gralco/l5-schematic/CAD/PADS/librem5_mainboard/librem5_mainboard_kicad_conversion/librem5_mainboard_sheet3.kicad_sch

## KiCad design CAD/PADS/librem5_mainboard/librem5_mainboard_kicad_conversion/librem5_mainboard_sheet3.kicad_sch (2026-05-21)

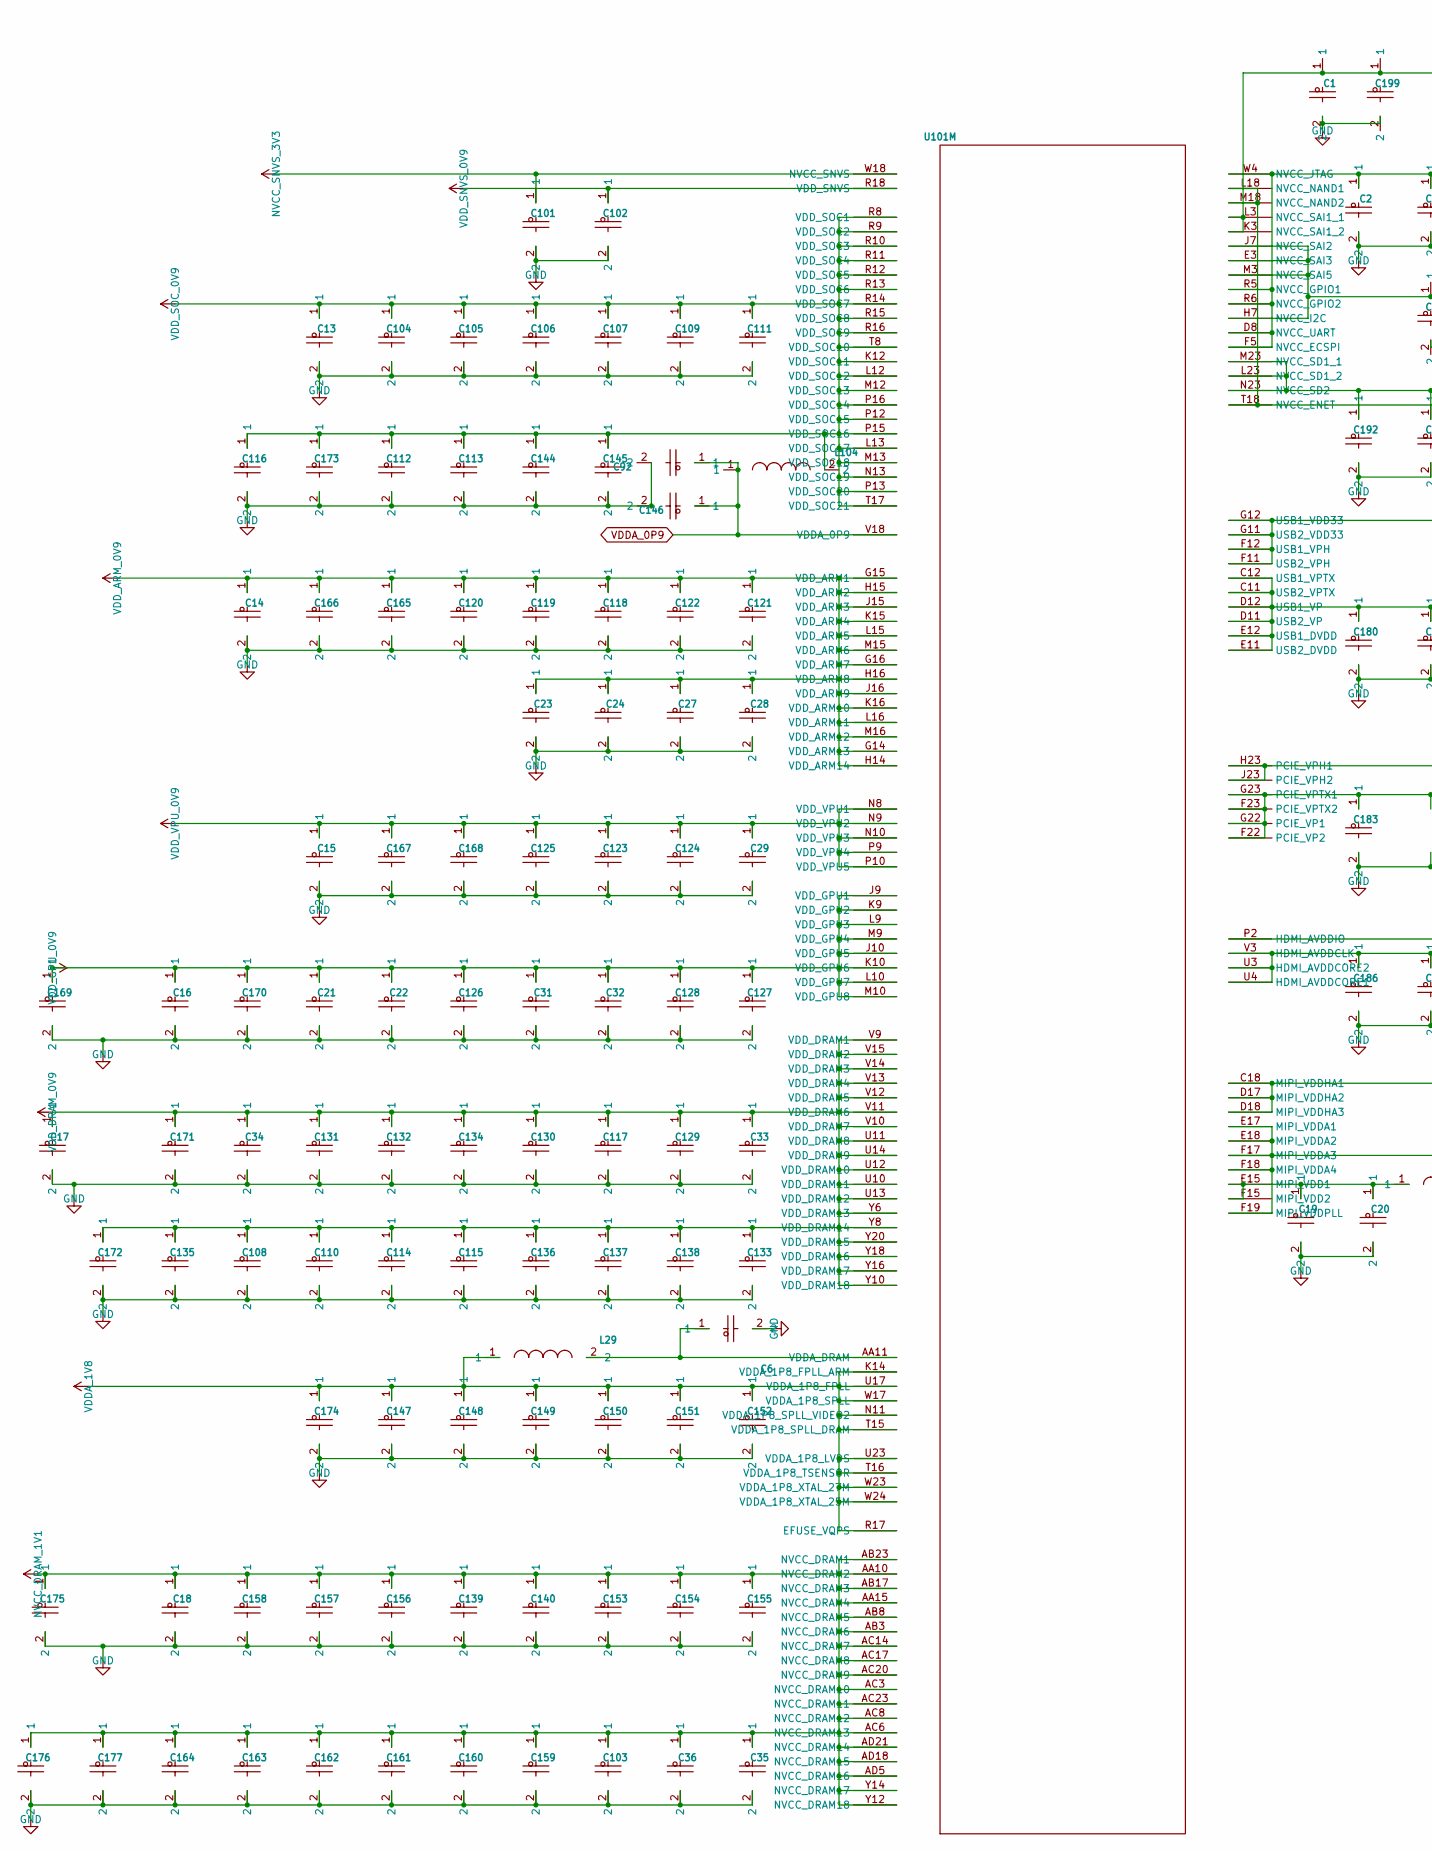
[picture p36: schematic librem5_mainboard_sheet3.kicad_sch, part in row 1, column 1]

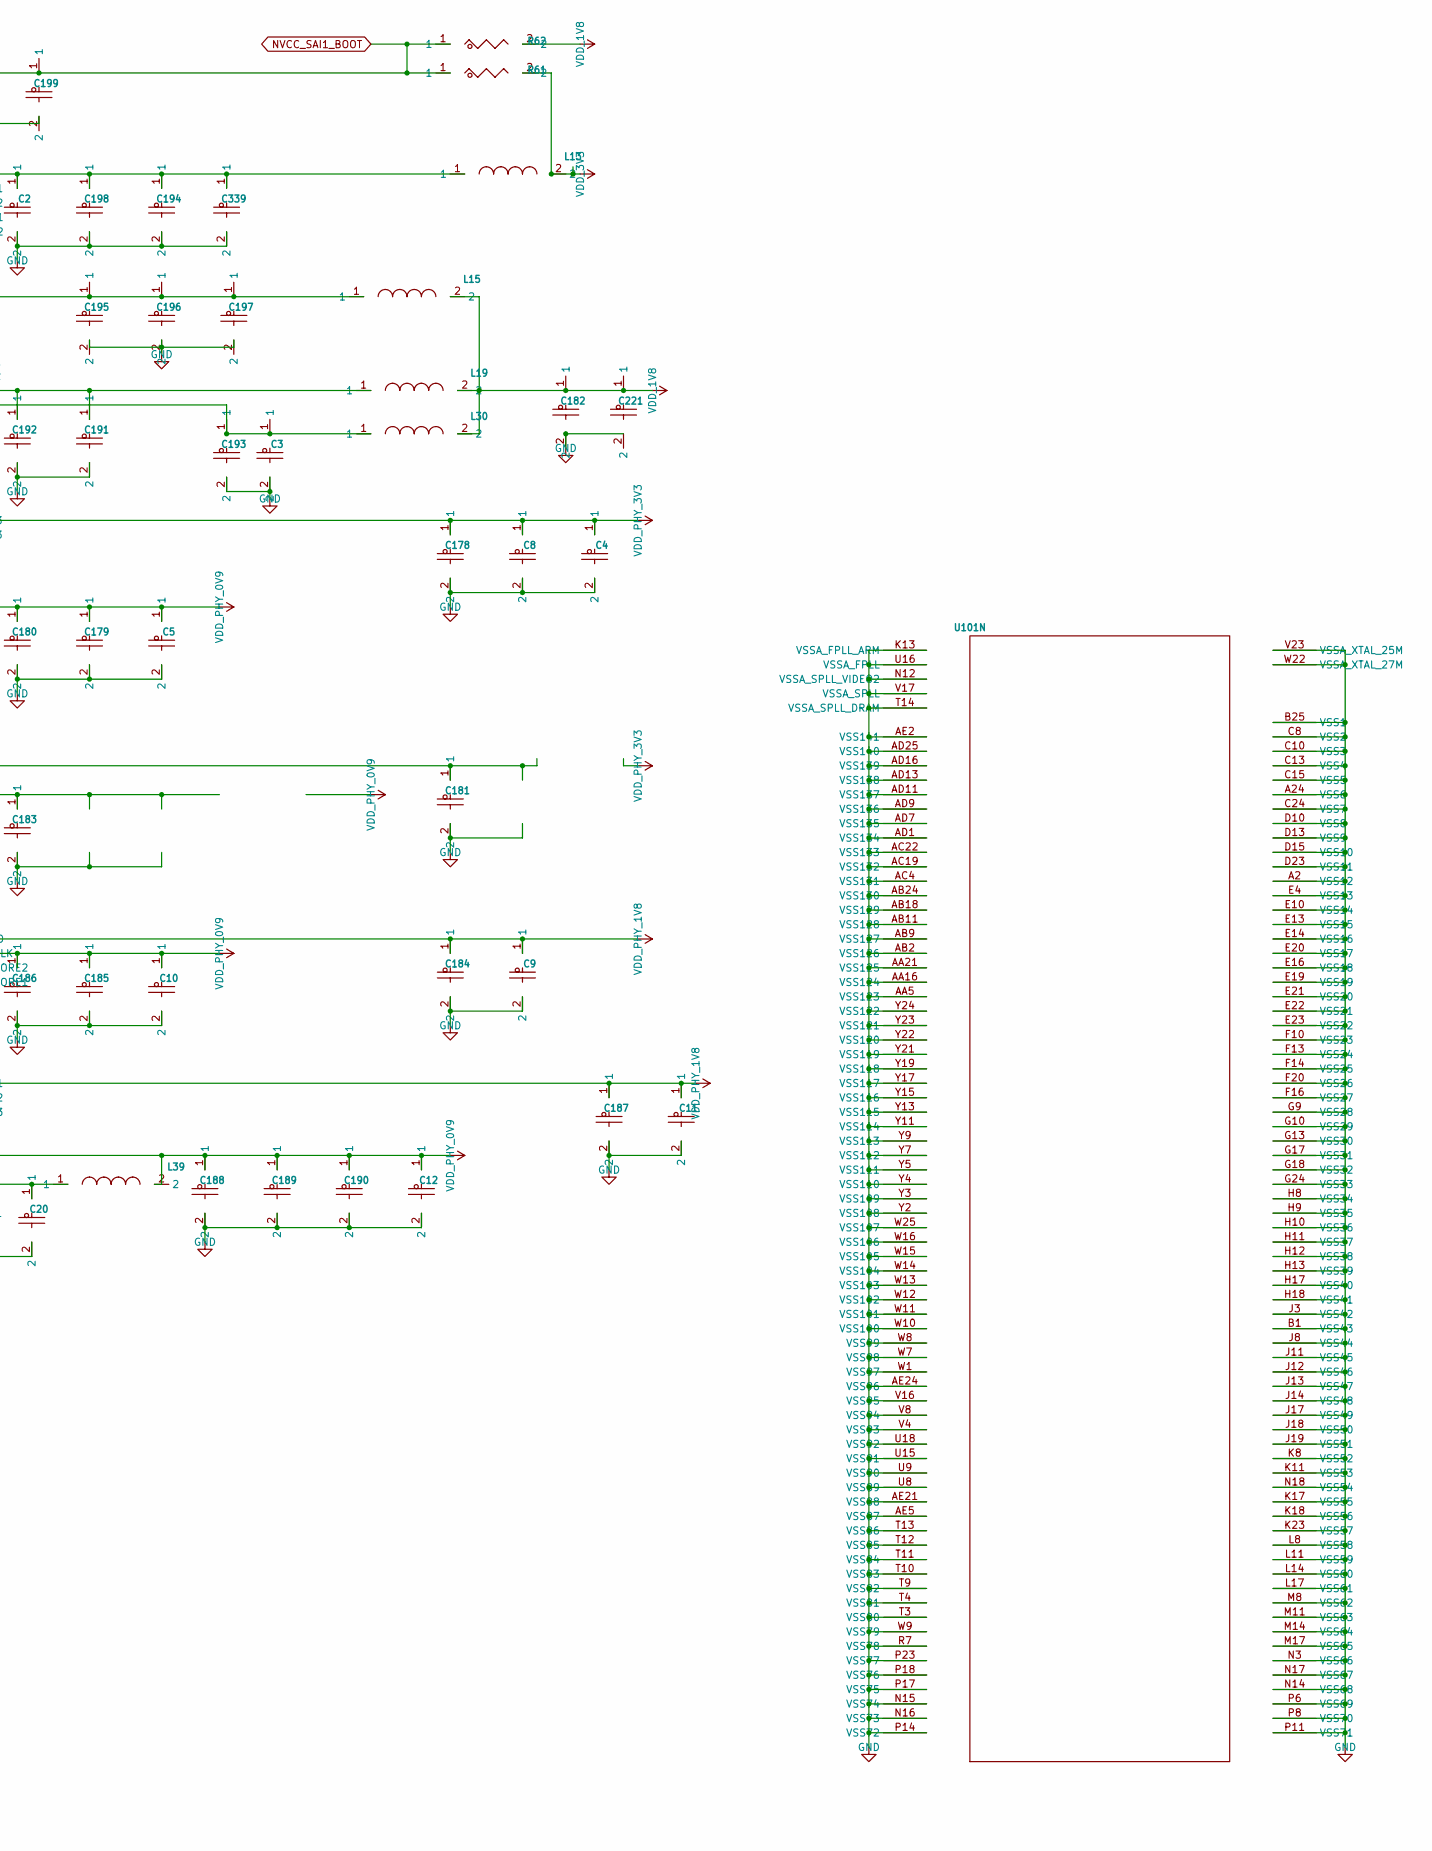
[picture p37: schematic librem5_mainboard_sheet3.kicad_sch, part in row 1, column 2]

Parts:
C1, C2, C3, C6, C8, C19, C20, C21, C22, C23, C24, C27, C28, C29, C31, C32, C34, C35, C36, C101, C102, C103, C104, C105, C106, C107, C109, C111, C112, C113, C118, C119, C120, C121, C122, C123, C124, C125, C126, C127, C128, C131, C132, C134, C139, C140, C144, C145, C146, C147, C148, C149, C150, C151, C152, C153, C154, C155, C156, C157, C158, C159, C160, C161, C162, C163, C164, C177, C178, C179, C180, C182, C184, C185, C186, C187, C188, C189, C190, C191, C192, C193, C194, C195, C196, C197, C198, C199, C221, C339: C0201; VOLTAGE 6.3V
C4, C5, C9, C10, C11, C12, C92: C0402; VOLTAGE 6.3V
C13, C14, C15, C16, C17, C18, C116, C165, C166, C167, C168, C169, C170, C171, C172, C173, C174, C175, C176: C0603; VOLTAGE 6.3V
C33, C108, C110, C114, C115, C117, C129, C130, C133, C135, C136, C137, C138: C0201; VOLTAGE 25V
C181, C183: C0201
L13, L15, L19, L29, L30, L39, L104: BEAD-0201
R61, R62: RES_2
U101: MIMX8MQ6DVAJZAA_BGA621

Connections:
GND: C1.2, C2.2, C3.2, C4.2, C5.2, C6.2, C8.2, C9.2, C10.2, C11.2, C12.2, C13.2, C14.2, C15.2, C16.2, C17.2, C18.2, C19.2, C20.2, C21.2, C22.2, C23.2, C24.2, C27.2, C28.2, C29.2, C31.2, C32.2, C33.2, C34.2, C35.2, C36.2, C92.2, C101.2, C102.2, C103.2, C104.2, C105.2, C106.2, C107.2, C108.2, C109.2, C110.2, C111.2, C112.2, C113.2, C114.2, C115.2, C116.2, C117.2, C118.2, C119.2, C120.2, C121.2, C122.2, C123.2, C124.2, C125.2, C126.2, C127.2, C128.2, C129.2, C130.2, C131.2, C132.2, C133.2, C134.2, C135.2, C136.2, C137.2, C138.2, C139.2, C140.2, C144.2, C145.2, C146.2, C147.2, C148.2, C149.2, C150.2, C151.2, C152.2, C153.2, C154.2, C155.2, C156.2, C157.2, C158.2, C159.2, C160.2, C161.2, C162.2, C163.2, C164.2, C165.2, C166.2, C167.2, C168.2, C169.2, C170.2, C171.2, C172.2, C173.2, C174.2, C175.2, C176.2, C177.2, C178.2, C179.2, C180.2, C181.2, C182.2, C183.2, C184.2, C185.2, C186.2, C187.2, C188.2, C189.2, C190.2, C191.2, C192.2, C193.2, C194.2, C195.2, C196.2, C197.2, C198.2, C199.2, C221.2, C339.2, U101.A2 (VSS12), U101.A24 (VSS6), U101.AA5 (VSS123), U101.AA16 (VSS124), U101.AA21 (VSS125), U101.AB2 (VSS126), U101.AB9 (VSS127), U101.AB11 (VSS128), U101.AB18 (VSS129), U101.AB24 (VSS130), U101.AC4 (VSS131), U101.AC19 (VSS132), U101.AC22 (VSS133), U101.AD1 (VSS134), U101.AD7 (VSS135), U101.AD9 (VSS136), U101.AD11 (VSS137), U101.AD13 (VSS138), U101.AD16 (VSS139), U101.AD25 (VSS140), U101.AE2 (VSS141), U101.AE5 (VSS87), U101.AE21 (VSS88), U101.AE24 (VSS96), U101.B1 (VSS43), U101.B25 (VSS1), U101.C8 (VSS2), U101.C10 (VSS3), U101.C13 (VSS4), U101.C15 (VSS5), U101.C24 (VSS7), U101.D10 (VSS8), U101.D13 (VSS9), U101.D15 (VSS10), U101.D23 (VSS11), U101.E4 (VSS13), U101.E10 (VSS14), U101.E13 (VSS15), U101.E14 (VSS16), U101.E16 (VSS18), U101.E19 (VSS19), U101.E20 (VSS17), U101.E21 (VSS20), U101.E22 (VSS21), U101.E23 (VSS22), U101.F10 (VSS23), U101.F13 (VSS24), U101.F14 (VSS25), U101.F16 (VSS27), U101.F20 (VSS26), U101.G9 (VSS28), U101.G10 (VSS29), U101.G13 (VSS30), U101.G17 (VSS31), U101.G18 (VSS32), U101.G24 (VSS33), U101.H8 (VSS34), U101.H9 (VSS35), U101.H10 (VSS36), U101.H11 (VSS37), U101.H12 (VSS38), U101.H13 (VSS39), U101.H17 (VSS40), U101.H18 (VSS41), U101.J3 (VSS42), U101.J8 (VSS44), U101.J11 (VSS45), U101.J12 (VSS46), U101.J13 (VSS47), U101.J14 (VSS48), U101.J17 (VSS49), U101.J18 (VSS50), U101.J19 (VSS51), U101.K8 (VSS52), U101.K11 (VSS53), U101.K13 (VSSA_FPLL_ARM), U101.K17 (VSS55), U101.K18 (VSS56), U101.K23 (VSS57), U101.L8 (VSS58), U101.L11 (VSS59), U101.L14 (VSS60), U101.L17 (VSS61), U101.M8 (VSS62), U101.M11 (VSS63), U101.M14 (VSS64), U101.M17 (VSS65), U101.N3 (VSS66), U101.N12 (VSSA_SPLL_VIDEO2), U101.N14 (VSS68), U101.N15 (VSS74), U101.N16 (VSS73), U101.N17 (VSS67), U101.N18 (VSS54), U101.P6 (VSS69), U101.P8 (VSS70), U101.P11 (VSS71), U101.P14 (VSS72), U101.P17 (VSS75), U101.P18 (VSS76), U101.P23 (VSS77), U101.R7 (VSS78), U101.T3 (VSS80), U101.T4 (VSS81), U101.T9 (VSS82), U101.T10 (VSS83), U101.T11 (VSS84), U101.T12 (VSS85), U101.T13 (VSS86), U101.T14 (VSSA_SPLL_DRAM), U101.U8 (VSS89), U101.U9 (VSS90), U101.U15 (VSS91), U101.U16 (VSSA_FPLL), U101.U18 (VSS92), U101.V4 (VSS93), U101.V8 (VSS94), U101.V16 (VSS95), U101.V17 (VSSA_SPLL), U101.V23 (VSSA_XTAL_25M), U101.W1 (VSS97), U101.W7 (VSS98), U101.W8 (VSS99), U101.W9 (VSS79), U101.W10 (VSS100), U101.W11 (VSS101), U101.W12 (VSS102), U101.W13 (VSS103), U101.W14 (VSS104), U101.W15 (VSS105), U101.W16 (VSS106), U101.W22 (VSSA_XTAL_27M), U101.W25 (VSS107), U101.Y2 (VSS108), U101.Y3 (VSS109), U101.Y4 (VSS110), U101.Y5 (VSS111), U101.Y7 (VSS112), U101.Y9 (VSS113), U101.Y11 (VSS114), U101.Y13 (VSS115), U101.Y15 (VSS116), U101.Y17 (VSS117), U101.Y19 (VSS118), U101.Y21 (VSS119), U101.Y22 (VSS120), U101.Y23 (VSS121), U101.Y24 (VSS122)
NVCC_DRAM_1V1: C18.1, C35.1, C36.1, C103.1, C139.1, C140.1, C153.1, C154.1, C155.1, C156.1, C157.1, C158.1, C159.1, C160.1, C161.1, C162.1, C163.1, C164.1, C175.1, C176.1, C177.1, U101.AA10 (NVCC_DRAM2), U101.AA15 (NVCC_DRAM4), U101.AB3 (NVCC_DRAM6), U101.AB8 (NVCC_DRAM5), U101.AB17 (NVCC_DRAM3), U101.AB23 (NVCC_DRAM1), U101.AC3 (NVCC_DRAM10), U101.AC6 (NVCC_DRAM13), U101.AC8 (NVCC_DRAM12), U101.AC14 (NVCC_DRAM7), U101.AC17 (NVCC_DRAM8), U101.AC20 (NVCC_DRAM9), U101.AC23 (NVCC_DRAM11), U101.AD5 (NVCC_DRAM16), U101.AD18 (NVCC_DRAM15), U101.AD21 (NVCC_DRAM14), U101.Y12 (NVCC_DRAM18), U101.Y14 (NVCC_DRAM17)
NVCC_SAI1_BOOT: C1.1, C199.1, R61.1, R62.1, U101.K3 (NVCC_SAI1_2), U101.L3 (NVCC_SAI1_1)
NVCC_SNVS_3V3: C101.1, U101.W18 (NVCC_SNVS)
unnamed: C6.1, L29.2, U101.AA11 (VDDA_DRAM)
unnamed: C19.1, C20.1, L39.1, U101.E15 (MIPI_VDD1), U101.F15 (MIPI_VDD2)
unnamed: C181.1, U101.H23 (PCIE_VPH1), U101.J23 (PCIE_VPH2)
unnamed: C183.1, U101.F22 (PCIE_VP2), U101.F23 (PCIE_VPTX2), U101.G22 (PCIE_VP1), U101.G23 (PCIE_VPTX1)
unnamed: C191.1, C192.1, L19.1, U101.L23 (NVCC_SD1_2), U101.M23 (NVCC_SD1_1), U101.N23 (NVCC_SD2)
unnamed: C3.1, C193.1, L30.1, U101.L18 (NVCC_NAND1), U101.M18 (NVCC_NAND2), U101.T18 (NVCC_ENET)
unnamed: C2.1, C194.1, C198.1, C339.1, L13.1, U101.D8 (NVCC_UART), U101.F5 (NVCC_ECSPI), U101.R5 (NVCC_GPIO1), U101.R6 (NVCC_GPIO2), U101.W4 (NVCC_JTAG)
unnamed: C195.1, C196.1, C197.1, L15.1, U101.E3 (NVCC_SAI3), U101.H7 (NVCC_I2C), U101.J7 (NVCC_SAI2), U101.M3 (NVCC_SAI5)
VDDA_0P9: C92.1, C146.1, L104.1, U101.V18 (VDDA_0P9)
VDDA_1V8: C147.1, C148.1, C149.1, C150.1, C151.1, C152.1, C174.1, L29.1, U101.K14 (VDDA_1P8_FPLL_ARM), U101.N11 (VDDA_1P8_SPLL_VIDEO2), U101.R17 (EFUSE_VQPS), U101.T15 (VDDA_1P8_SPLL_DRAM), U101.T16 (VDDA_1P8_TSENSOR), U101.U17 (VDDA_1P8_FPLL), U101.U23 (VDDA_1P8_LVDS), U101.W17 (VDDA_1P8_SPLL), U101.W23 (VDDA_1P8_XTAL_27M), U101.W24 (VDDA_1P8_XTAL_25M)
VDD_1V8: C182.1, C221.1, L15.2, L19.2, L30.2, R62.2
VDD_3V3: L13.2, R61.2
VDD_ARM_0V9: C14.1, C23.1, C24.1, C27.1, C28.1, C118.1, C119.1, C120.1, C121.1, C122.1, C165.1, C166.1, U101.G14 (VDD_ARM13), U101.G15 (VDD_ARM1), U101.G16 (VDD_ARM7), U101.H14 (VDD_ARM14), U101.H15 (VDD_ARM2), U101.H16 (VDD_ARM8), U101.J15 (VDD_ARM3), U101.J16 (VDD_ARM9), U101.K15 (VDD_ARM4), U101.K16 (VDD_ARM10), U101.L15 (VDD_ARM5), U101.L16 (VDD_ARM11), U101.M15 (VDD_ARM6), U101.M16 (VDD_ARM12)
VDD_DRAM_0V9: C17.1, C33.1, C34.1, C108.1, C110.1, C114.1, C115.1, C117.1, C129.1, C130.1, C131.1, C132.1, C133.1, C134.1, C135.1, C136.1, C137.1, C138.1, C171.1, C172.1, U101.U10 (VDD_DRAM11), U101.U11 (VDD_DRAM8), U101.U12 (VDD_DRAM10), U101.U13 (VDD_DRAM12), U101.U14 (VDD_DRAM9), U101.V9 (VDD_DRAM1), U101.V10 (VDD_DRAM7), U101.V11 (VDD_DRAM6), U101.V12 (VDD_DRAM5), U101.V13 (VDD_DRAM4), U101.V14 (VDD_DRAM3), U101.V15 (VDD_DRAM2), U101.Y6 (VDD_DRAM13), U101.Y8 (VDD_DRAM14), U101.Y10 (VDD_DRAM18), U101.Y16 (VDD_DRAM17), U101.Y18 (VDD_DRAM16), U101.Y20 (VDD_DRAM15)
VDD_GPU_0V9: C16.1, C21.1, C22.1, C31.1, C32.1, C126.1, C127.1, C128.1, C169.1, C170.1, U101.J9 (VDD_GPU1), U101.J10 (VDD_GPU5), U101.K9 (VDD_GPU2), U101.K10 (VDD_GPU6), U101.L9 (VDD_GPU3), U101.L10 (VDD_GPU7), U101.M9 (VDD_GPU4), U101.M10 (VDD_GPU8)
VDD_PHY_0V9: C5.1, C10.1, C12.1, C179.1, C180.1, C185.1, C186.1, C188.1, C189.1, C190.1, L39.2, U101.C11 (USB2_VPTX), U101.C12 (USB1_VPTX), U101.D11 (USB2_VP), U101.D12 (USB1_VP), U101.E11 (USB2_DVDD), U101.E12 (USB1_DVDD), U101.E17 (MIPI_VDDA1), U101.E18 (MIPI_VDDA2), U101.F17 (MIPI_VDDA3), U101.F18 (MIPI_VDDA4), U101.F19 (MIPI_VDDPLL), U101.U3 (HDMI_AVDDCORE2), U101.U4 (HDMI_AVDDCORE1), U101.V3 (HDMI_AVDDCLK)
VDD_PHY_1V8: C9.1, C11.1, C184.1, C187.1, U101.C18 (MIPI_VDDHA1), U101.D17 (MIPI_VDDHA2), U101.D18 (MIPI_VDDHA3), U101.P2 (HDMI_AVDDIO)
VDD_PHY_3V3: C4.1, C8.1, C178.1, U101.F11 (USB2_VPH), U101.F12 (USB1_VPH), U101.G11 (USB2_VDD33), U101.G12 (USB1_VDD33)
VDD_SNVS_0V9: C102.1, U101.R18 (VDD_SNVS)
VDD_SOC_0V9: C13.1, C104.1, C105.1, C106.1, C107.1, C109.1, C111.1, C112.1, C113.1, C116.1, C144.1, C145.1, C173.1, L104.2, U101.K12 (VDD_SOC11), U101.L12 (VDD_SOC12), U101.L13 (VDD_SOC17), U101.M12 (VDD_SOC13), U101.M13 (VDD_SOC18), U101.N13 (VDD_SOC19), U101.P12 (VDD_SOC15), U101.P13 (VDD_SOC20), U101.P15 (VDD_SOC16), U101.P16 (VDD_SOC14), U101.R8 (VDD_SOC1), U101.R9 (VDD_SOC2), U101.R10 (VDD_SOC3), U101.R11 (VDD_SOC4), U101.R12 (VDD_SOC5), U101.R13 (VDD_SOC6), U101.R14 (VDD_SOC7), U101.R15 (VDD_SOC8), U101.R16 (VDD_SOC9), U101.T8 (VDD_SOC10), U101.T17 (VDD_SOC21)
VDD_VPU_0V9: C15.1, C29.1, C123.1, C124.1, C125.1, C167.1, C168.1, U101.N8 (VDD_VPU1), U101.N9 (VDD_VPU2), U101.N10 (VDD_VPU3), U101.P9 (VDD_VPU4), U101.P10 (VDD_VPU5)
