gralco/l5-schematic/CAD/PADS/librem5_mainboard/librem5_mainboard_kicad_conversion/librem5_mainboard_sheet4.kicad_sch

## KiCad design CAD/PADS/librem5_mainboard/librem5_mainboard_kicad_conversion/librem5_mainboard_sheet4.kicad_sch (2026-05-21)

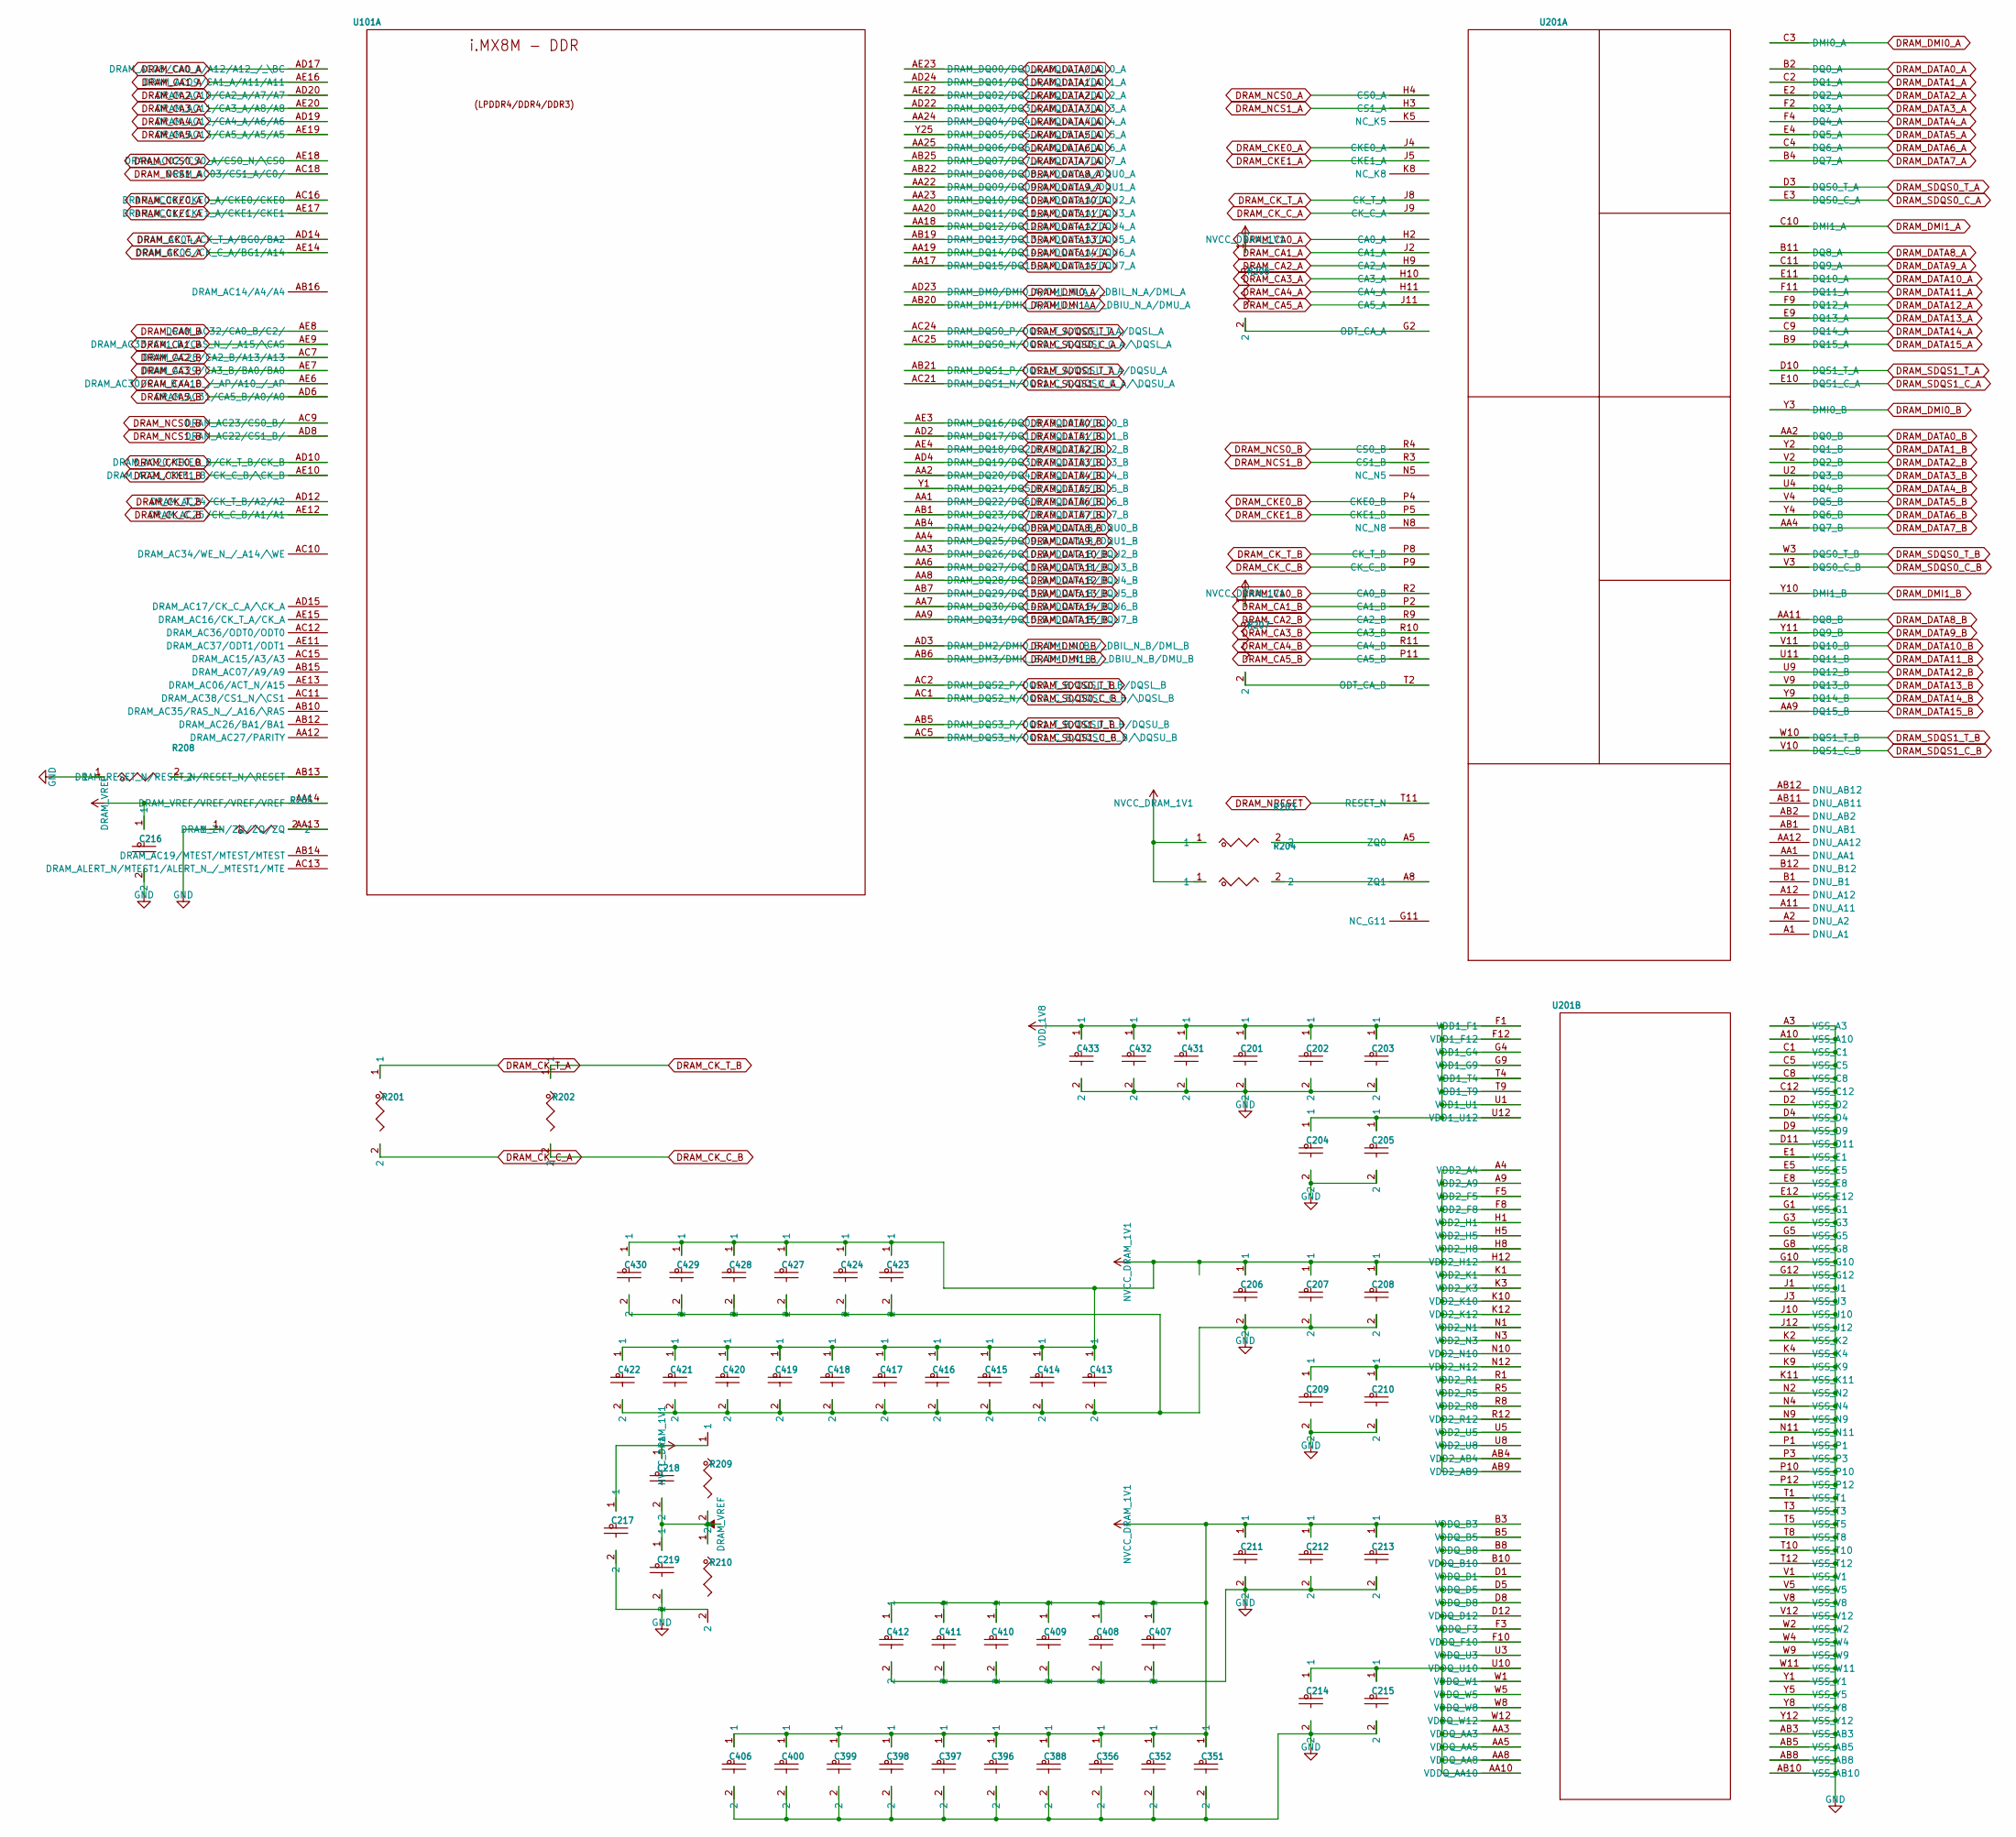
[picture p38: schematic librem5_mainboard_sheet4.kicad_sch]

Parts:
C201, C206, C211: C0603; VOLTAGE 6.3V
C202, C203, C204, C205, C207, C208, C209, C210, C212, C213, C214, C215, C217: C0402; VOLTAGE 6.3V
C216, C218, C219, C351, C352, C356, C388, C396, C397, C398, C399, C400, C406, C407, C408, C409, C410, C411, C412, C413, C414, C415, C416, C417, C418, C419, C420, C421, C422, C423, C424, C427, C428, C429, C430, C431, C432, C433: C0201; VOLTAGE 6.3V
R201, R202, R203, R204, R205, R206, R207, R208, R209, R210: RES_2
U101: MIMX8MQ6DVAJZAA_BGA621
U201: MT53B768M32D4NQ_200P

Connections:
DRAM_CA0_A: U101.AD17 (DRAM_AC08/CA0_A/A12/A12_/_\BC), U201.H2 (CA0_A)
DRAM_CA0_B: U101.AE8 (DRAM_AC32/CA0_B/C2/), U201.R2 (CA0_B)
DRAM_CA1_A: U101.AE16 (DRAM_AC09/CA1_A/A11/A11), U201.J2 (CA1_A)
DRAM_CA1_B: U101.AE9 (DRAM_AC33/CA1_B/CAS_N_/_A15/\CAS), U201.P2 (CA1_B)
DRAM_CA2_A: U101.AD20 (DRAM_AC10/CA2_A/A7/A7), U201.H9 (CA2_A)
DRAM_CA2_B: U101.AC7 (DRAM_AC28/CA2_B/A13/A13), U201.R9 (CA2_B)
DRAM_CA3_A: U101.AE20 (DRAM_AC11/CA3_A/A8/A8), U201.H10 (CA3_A)
DRAM_CA3_B: U101.AE7 (DRAM_AC29/CA3_B/BA0/BA0), U201.R10 (CA3_B)
DRAM_CA4_A: U101.AD19 (DRAM_AC12/CA4_A/A6/A6), U201.H11 (CA4_A)
DRAM_CA4_B: U101.AE6 (DRAM_AC30/CA4_B/A10_/_AP/A10_/_AP), U201.R11 (CA4_B)
DRAM_CA5_A: U101.AE19 (DRAM_AC13/CA5_A/A5/A5), U201.J11 (CA5_A)
DRAM_CA5_B: U101.AD6 (DRAM_AC31/CA5_B/A0/A0), U201.P11 (CA5_B)
DRAM_CKE0_A: U101.AC16 (DRAM_AC00/CKE0_A/CKE0/CKE0), U201.J4 (CKE0_A)
DRAM_CKE0_B: U101.AD10 (DRAM_AC20/CKE0_B/CK_T_B/CK_B), U201.P4 (CKE0_B)
DRAM_CKE1_A: U101.AE17 (DRAM_AC01/CKE1_A/CKE1/CKE1), U201.J5 (CKE1_A)
DRAM_CKE1_B: U101.AE10 (DRAM_AC21/CKE1_B/CK_C_B/\CK_B), U201.P5 (CKE1_B)
DRAM_CK_C_A: R201.2, U101.AE14 (DRAM_AC05/CK_C_A/BG1/A14), U201.J9 (CK_C_A)
DRAM_CK_C_B: R202.2, U101.AE12 (DRAM_AC25/CK_C_B/A1/A1), U201.P9 (CK_C_B)
DRAM_CK_T_A: R201.1, U101.AD14 (DRAM_AC04/CK_T_A/BG0/BA2), U201.J8 (CK_T_A)
DRAM_CK_T_B: R202.1, U101.AD12 (DRAM_AC24/CK_T_B/A2/A2), U201.P8 (CK_T_B)
DRAM_DATA0_A: U101.AE23 (DRAM_DQ00/DQ0_A/DQL0_A/DQL0_A), U201.B2 (DQ0_A)
DRAM_DATA0_B: U101.AE3 (DRAM_DQ16/DQ0_B/DQL0_B/DQL0_B), U201.AA2 (DQ0_B)
DRAM_DATA1_A: U101.AD24 (DRAM_DQ01/DQ1_A/DQL1_A/DQL1_A), U201.C2 (DQ1_A)
DRAM_DATA1_B: U101.AD2 (DRAM_DQ17/DQ1_B/DQL1_B/DQL1_B), U201.Y2 (DQ1_B)
DRAM_DATA2_A: U101.AE22 (DRAM_DQ02/DQ2_A/DQL2_A/DQL2_A), U201.E2 (DQ2_A)
DRAM_DATA2_B: U101.AE4 (DRAM_DQ18/DQ2_B/DQL2_B/DQL2_B), U201.V2 (DQ2_B)
DRAM_DATA3_A: U101.AD22 (DRAM_DQ03/DQ3_A/DQL3_A/DQL3_A), U201.F2 (DQ3_A)
DRAM_DATA3_B: U101.AD4 (DRAM_DQ19/DQ3_B/DQL3_B/DQL3_B), U201.U2 (DQ3_B)
DRAM_DATA4_A: U101.AA24 (DRAM_DQ04/DQ4_A/DQL4_A/DQL4_A), U201.F4 (DQ4_A)
DRAM_DATA4_B: U101.AA2 (DRAM_DQ20/DQ4_B/DQL4_B/DQL4_B), U201.U4 (DQ4_B)
DRAM_DATA5_A: U101.Y25 (DRAM_DQ05/DQ5_A/DQL5_A/DQL5_A), U201.E4 (DQ5_A)
DRAM_DATA5_B: U101.Y1 (DRAM_DQ21/DQ5_B/DQL5_B/DQL5_B), U201.V4 (DQ5_B)
DRAM_DATA6_A: U101.AA25 (DRAM_DQ06/DQ6_A/DQL6_A/DQL6_A), U201.C4 (DQ6_A)
DRAM_DATA6_B: U101.AA1 (DRAM_DQ22/DQ6_B/DQL6_B/DQL6_B), U201.Y4 (DQ6_B)
DRAM_DATA7_A: U101.AB25 (DRAM_DQ07/DQ7_A/DQL7_A/DQL7_A), U201.B4 (DQ7_A)
DRAM_DATA7_B: U101.AB1 (DRAM_DQ23/DQ7_B/DQL7_B/DQL7_B), U201.AA4 (DQ7_B)
DRAM_DATA8_A: U101.AB22 (DRAM_DQ08/DQ08_A/DQU0_A/DQU0_A), U201.B11 (DQ8_A)
DRAM_DATA8_B: U101.AB4 (DRAM_DQ24/DQ08_B/DQU0_B/DQU0_B), U201.AA11 (DQ8_B)
DRAM_DATA9_A: U101.AA22 (DRAM_DQ09/DQ09_A/DQU1_A/DQU1_A), U201.C11 (DQ9_A)
DRAM_DATA9_B: U101.AA4 (DRAM_DQ25/DQ09_B/DQU1_B/DQU1_B), U201.Y11 (DQ9_B)
DRAM_DATA10_A: U101.AA23 (DRAM_DQ10/DQ10_A/DQU2_A/DQU2_A), U201.E11 (DQ10_A)
DRAM_DATA10_B: U101.AA3 (DRAM_DQ26/DQ10_B/DQU2_B/DQU2_B), U201.V11 (DQ10_B)
DRAM_DATA11_A: U101.AA20 (DRAM_DQ11/DQ11_A/DQU3_A/DQU3_A), U201.F11 (DQ11_A)
DRAM_DATA11_B: U101.AA6 (DRAM_DQ27/DQ11_B/DQU3_B/DQU3_B), U201.U11 (DQ11_B)
DRAM_DATA12_A: U101.AA18 (DRAM_DQ12/DQ12_A/DQU4_A/DQU4_A), U201.F9 (DQ12_A)
DRAM_DATA12_B: U101.AA8 (DRAM_DQ28/DQ12_B/DQU4_B/DQU4_B), U201.U9 (DQ12_B)
DRAM_DATA13_A: U101.AB19 (DRAM_DQ13/DQ13_A/DQU5_A/DQU5_A), U201.E9 (DQ13_A)
DRAM_DATA13_B: U101.AB7 (DRAM_DQ29/DQ13_B/DQU5_B/DQU5_B), U201.V9 (DQ13_B)
DRAM_DATA14_A: U101.AA19 (DRAM_DQ14/DQ14_A/DQU6_A/DQU6_A), U201.C9 (DQ14_A)
DRAM_DATA14_B: U101.AA7 (DRAM_DQ30/DQ14_B/DQU6_B/DQU6_B), U201.Y9 (DQ14_B)
DRAM_DATA15_A: U101.AA17 (DRAM_DQ15/DQ15_A/DQU7_A/DQU7_A), U201.B9 (DQ15_A)
DRAM_DATA15_B: U101.AA9 (DRAM_DQ31/DQ15_B/DQU7_B/DQU7_B), U201.AA9 (DQ15_B)
DRAM_DMI0_A: U101.AD23 (DRAM_DM0/DMI0_A/DML_N_A_/_DBIL_N_A/DML_A), U201.C3 (DMI0_A)
DRAM_DMI0_B: U101.AD3 (DRAM_DM2/DMI0_B/DML_N_B_/_DBIL_N_B/DML_B), U201.Y3 (DMI0_B)
DRAM_DMI1_A: U101.AB20 (DRAM_DM1/DMI1_A/DMU_N_A_/_DBIU_N_A/DMU_A), U201.C10 (DMI1_A)
DRAM_DMI1_B: U101.AB6 (DRAM_DM3/DMI1_B/DMU_N_B_/_DBIU_N_B/DMU_B), U201.Y10 (DMI1_B)
DRAM_NCS0_A: U101.AE18 (DRAM_AC02/CS0_A/CS0_N/\CS0), U201.H4 (CS0_A)
DRAM_NCS0_B: U101.AC9 (DRAM_AC23/CS0_B/), U201.R4 (CS0_B)
DRAM_NCS1_A: U101.AC18 (DRAM_AC03/CS1_A/C0/), U201.H3 (CS1_A)
DRAM_NCS1_B: U101.AD8 (DRAM_AC22/CS1_B/), U201.R3 (CS1_B)
DRAM_NRESET: U201.T11 (RESET_N)
DRAM_SDQS0_C_A: U101.AC25 (DRAM_DQS0_N/DQS0_C_A/DQSL_C_A/\DQSL_A), U201.E3 (DQS0_C_A)
DRAM_SDQS0_C_B: U101.AC1 (DRAM_DQS2_N/DQS0_C_B/DQSL_C_B/\DQSL_B), U201.V3 (DQS0_C_B)
DRAM_SDQS0_T_A: U101.AC24 (DRAM_DQS0_P/DQS0_T_A/DQSL_T_A/DQSL_A), U201.D3 (DQS0_T_A)
DRAM_SDQS0_T_B: U101.AC2 (DRAM_DQS2_P/DQS0_T_B/DQSL_T_B/DQSL_B), U201.W3 (DQS0_T_B)
DRAM_SDQS1_C_A: U101.AC21 (DRAM_DQS1_N/DQS1_C_A/DQSU_C_A/\DQSU_A), U201.E10 (DQS1_C_A)
DRAM_SDQS1_C_B: U101.AC5 (DRAM_DQS3_N/DQS1_C_B/DQSU_C_B/\DQSU_B), U201.V10 (DQS1_C_B)
DRAM_SDQS1_T_A: U101.AB21 (DRAM_DQS1_P/DQS1_T_A/DQSU_T_A/DQSU_A), U201.D10 (DQS1_T_A)
DRAM_SDQS1_T_B: U101.AB5 (DRAM_DQS3_P/DQS1_T_B/DQSU_T_B/DQSU_B), U201.W10 (DQS1_T_B)
DRAM_VREF: C216.1, C218.2, C219.1, R209.2, R210.1, U101.AA14 (DRAM_VREF/VREF/VREF/VREF)
GND: C201.2, C202.2, C203.2, C204.2, C205.2, C206.2, C207.2, C208.2, C209.2, C210.2, C211.2, C212.2, C213.2, C214.2, C215.2, C216.2, C217.2, C219.2, C351.2, C352.2, C356.2, C388.2, C396.2, C397.2, C398.2, C399.2, C400.2, C406.2, C407.2, C408.2, C409.2, C410.2, C411.2, C412.2, C413.2, C414.2, C415.2, C416.2, C417.2, C418.2, C419.2, C420.2, C421.2, C422.2, C423.2, C424.2, C427.2, C428.2, C429.2, C430.2, C431.2, C432.2, C433.2, R205.1, R208.1, R210.2, U201.A3 (VSS_A3), U201.A10 (VSS_A10), U201.AB3 (VSS_AB3), U201.AB5 (VSS_AB5), U201.AB8 (VSS_AB8), U201.AB10 (VSS_AB10), U201.C1 (VSS_C1), U201.C5 (VSS_C5), U201.C8 (VSS_C8), U201.C12 (VSS_C12), U201.D2 (VSS_D2), U201.D4 (VSS_D4), U201.D9 (VSS_D9), U201.D11 (VSS_D11), U201.E1 (VSS_E1), U201.E5 (VSS_E5), U201.E8 (VSS_E8), U201.E12 (VSS_E12), U201.G1 (VSS_G1), U201.G3 (VSS_G3), U201.G5 (VSS_G5), U201.G8 (VSS_G8), U201.G10 (VSS_G10), U201.G12 (VSS_G12), U201.J1 (VSS_J1), U201.J3 (VSS_J3), U201.J10 (VSS_J10), U201.J12 (VSS_J12), U201.K2 (VSS_K2), U201.K4 (VSS_K4), U201.K9 (VSS_K9), U201.K11 (VSS_K11), U201.N2 (VSS_N2), U201.N4 (VSS_N4), U201.N9 (VSS_N9), U201.N11 (VSS_N11), U201.P1 (VSS_P1), U201.P3 (VSS_P3), U201.P10 (VSS_P10), U201.P12 (VSS_P12), U201.T1 (VSS_T1), U201.T3 (VSS_T3), U201.T5 (VSS_T5), U201.T8 (VSS_T8), U201.T10 (VSS_T10), U201.T12 (VSS_T12), U201.V1 (VSS_V1), U201.V5 (VSS_V5), U201.V8 (VSS_V8), U201.V12 (VSS_V12), U201.W2 (VSS_W2), U201.W4 (VSS_W4), U201.W9 (VSS_W9), U201.W11 (VSS_W11), U201.Y1 (VSS_Y1), U201.Y5 (VSS_Y5), U201.Y8 (VSS_Y8), U201.Y12 (VSS_Y12)
NVCC_DRAM_1V1: C206.1, C207.1, C208.1, C209.1, C210.1, C211.1, C212.1, C213.1, C214.1, C215.1, C217.1, C218.1, C351.1, C352.1, C356.1, C388.1, C396.1, C397.1, C398.1, C399.1, C400.1, C406.1, C407.1, C408.1, C409.1, C410.1, C411.1, C412.1, C413.1, C414.1, C415.1, C416.1, C417.1, C418.1, C419.1, C420.1, C421.1, C422.1, C423.1, C424.1, C427.1, C428.1, C429.1, C430.1, R203.1, R204.1, R206.1, R207.1, R209.1, U201.A4 (VDD2_A4), U201.A9 (VDD2_A9), U201.AA3 (VDDQ_AA3), U201.AA5 (VDDQ_AA5), U201.AA8 (VDDQ_AA8), U201.AA10 (VDDQ_AA10), U201.AB4 (VDD2_AB4), U201.AB9 (VDD2_AB9), U201.B3 (VDDQ_B3), U201.B5 (VDDQ_B5), U201.B8 (VDDQ_B8), U201.B10 (VDDQ_B10), U201.D1 (VDDQ_D1), U201.D5 (VDDQ_D5), U201.D8 (VDDQ_D8), U201.D12 (VDDQ_D12), U201.F3 (VDDQ_F3), U201.F5 (VDD2_F5), U201.F8 (VDD2_F8), U201.F10 (VDDQ_F10), U201.H1 (VDD2_H1), U201.H5 (VDD2_H5), U201.H8 (VDD2_H8), U201.H12 (VDD2_H12), U201.K1 (VDD2_K1), U201.K3 (VDD2_K3), U201.K10 (VDD2_K10), U201.K12 (VDD2_K12), U201.N1 (VDD2_N1), U201.N3 (VDD2_N3), U201.N10 (VDD2_N10), U201.N12 (VDD2_N12), U201.R1 (VDD2_R1), U201.R5 (VDD2_R5), U201.R8 (VDD2_R8), U201.R12 (VDD2_R12), U201.U3 (VDDQ_U3), U201.U5 (VDD2_U5), U201.U8 (VDD2_U8), U201.U10 (VDDQ_U10), U201.W1 (VDDQ_W1), U201.W5 (VDDQ_W5), U201.W8 (VDDQ_W8), U201.W12 (VDDQ_W12)
unnamed: R203.2, U201.A5 (ZQ0)
unnamed: R204.2, U201.A8 (ZQ1)
unnamed: R205.2, U101.AA13 (DRAM_ZN/ZQ/ZQ/ZQ)
unnamed: R206.2, U201.G2 (ODT_CA_A)
unnamed: R207.2, U201.T2 (ODT_CA_B)
unnamed: R208.2, U101.AB13 (DRAM_RESET_N/RESET_N/RESET_N/\RESET)
VDD_1V8: C201.1, C202.1, C203.1, C204.1, C205.1, C431.1, C432.1, C433.1, U201.F1 (VDD1_F1), U201.F12 (VDD1_F12), U201.G4 (VDD1_G4), U201.G9 (VDD1_G9), U201.T4 (VDD1_T4), U201.T9 (VDD1_T9), U201.U1 (VDD1_U1), U201.U12 (VDD1_U12)
