gralco/l5-schematic/CAD/PADS/librem5_mainboard/librem5_mainboard_kicad_conversion/librem5_mainboard_sheet5.kicad_sch

## KiCad design CAD/PADS/librem5_mainboard/librem5_mainboard_kicad_conversion/librem5_mainboard_sheet5.kicad_sch (2026-05-21)

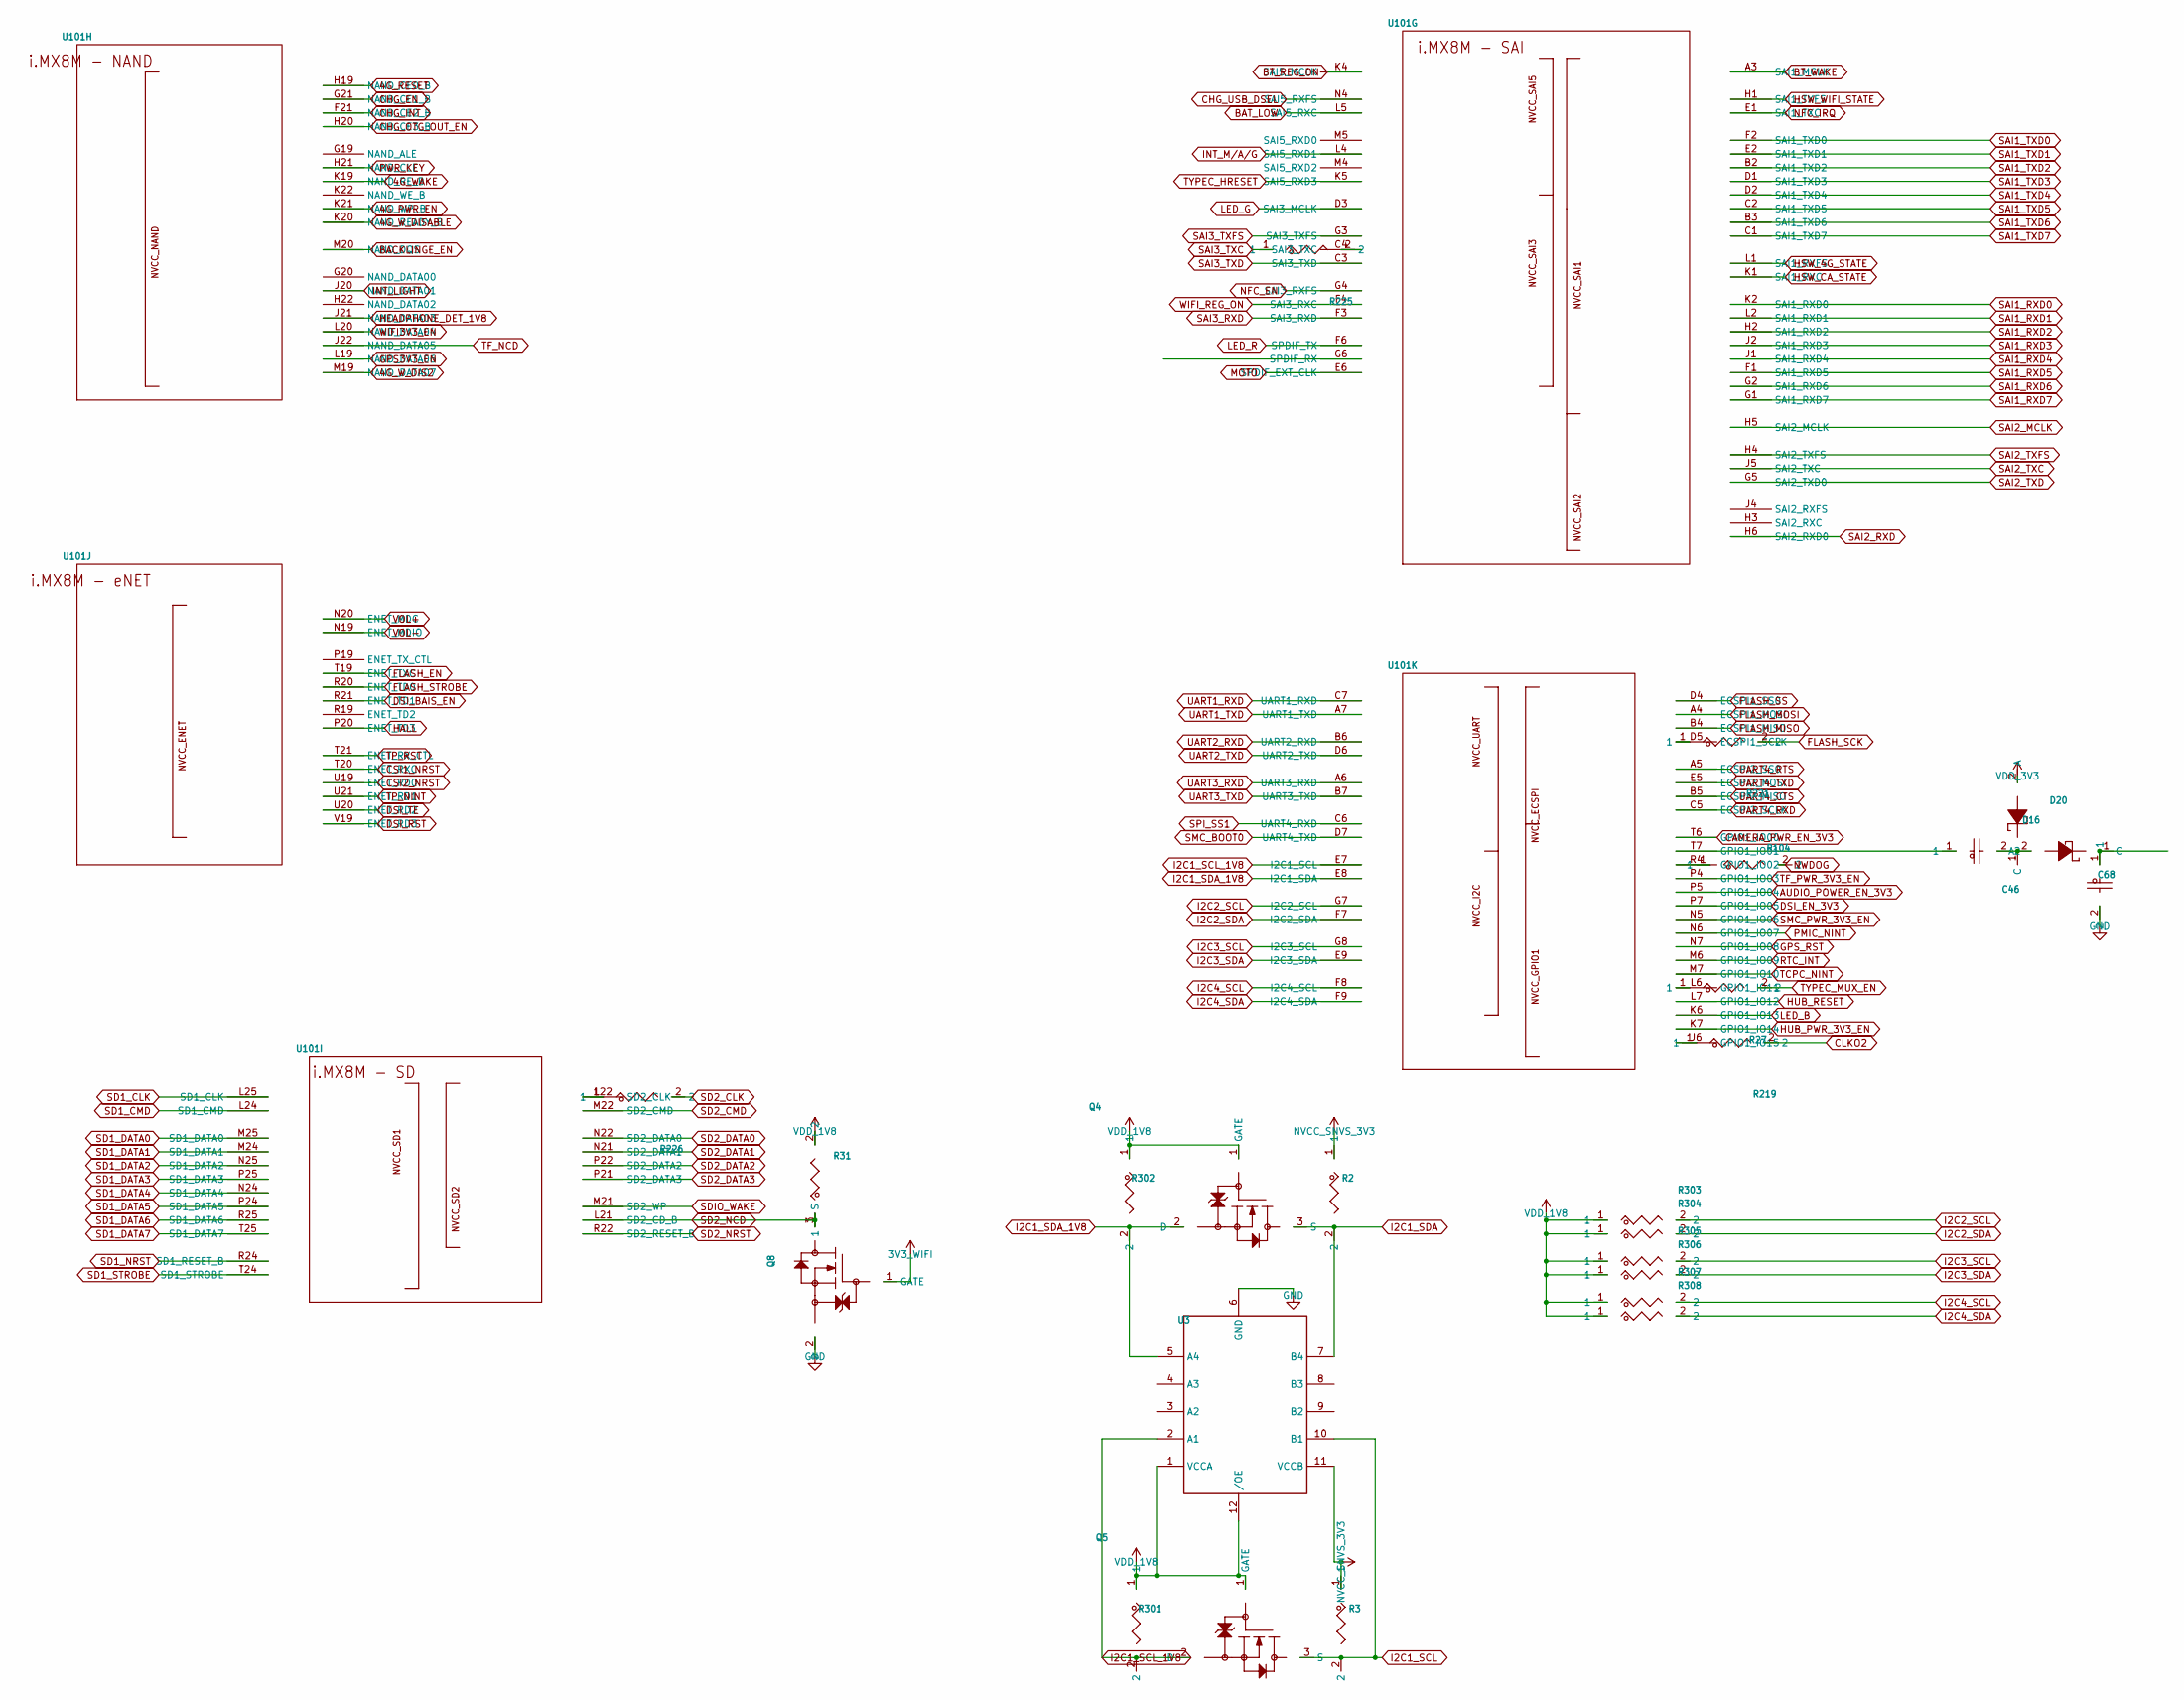
[picture p39: schematic librem5_mainboard_sheet5.kicad_sch]

Parts:
C46: C0402; VOLTAGE 6.3V
C68: C0402; VOLTAGE 25V
D16, D20: DIODE_SCHTKY_0
Q4, Q5, Q8: 2SK3018
R2, R3, R27, R31, R104, R219, R221, R225, R226, R301, R302, R303, R304, R305, R306, R307, R308: RES_2
U3: NTBA104_XQFN12
U101: MIMX8MQ6DVAJZAA_BGA621

Connections:
3V3_WIFI: Q8.1 (GATE)
4G_PWR_EN: U101.K21 (NAND_WP_B)
4G_RESET: U101.H19 (NAND_CE0_B)
4G_WAKE: U101.K19 (NAND_RE_B)
4G_W_DIS2: U101.M19 (NAND_DATA07)
4G_W_DISABLE: U101.K20 (NAND_READY_B)
AUDIO_POWER_EN_3V3: U101.P5 (GPIO1_IO04)
BACKLINGE_EN: U101.M20 (NAND_DQS)
BAT_LOW: U101.L5 (SAI5_RXC)
BT_REG_ON: U101.K4 (SAI5_MCLK)
BT_WAKE: U101.A3 (SAI1_MCLK)
CAMERA_PWR_EN_3V3: U101.T6 (GPIO1_IO00)
CHG_EN: U101.G21 (NAND_CE1_B)
CHG_INT: U101.F21 (NAND_CE2_B)
CHG_OTG_OUT_EN: U101.H20 (NAND_CE3_B)
CHG_USB_DSEL: U101.N4 (SAI5_RXFS)
CLKO2: R219.2
CSI1_NRST: U101.T20 (ENET_RXC)
CSI2_NRST: U101.U19 (ENET_RD0)
DSI_BAIS_EN: U101.R21 (ENET_TD1)
DSI_EN_3V3: U101.P7 (GPIO1_IO05)
DSI_RST: U101.V19 (ENET_RD3)
DSI_TE: U101.U20 (ENET_RD2)
FLASH_EN: U101.T19 (ENET_TXC)
FLASH_MISO: U101.B4 (ECSPI1_MISO)
FLASH_MOSI: U101.A4 (ECSPI1_MOSI)
FLASH_SCK: R221.2
FLASH_SS: U101.D4 (ECSPI1_SS0)
FLASH_STROBE: U101.R20 (ENET_TD0)
GND: C68.2, Q8.2 (D), U3.6 (GND)
GPS3V3_EN: U101.L19 (NAND_DATA06)
GPS_RST: U101.N7 (GPIO1_IO08)
HALL: U101.P20 (ENET_TD3)
HEADPHONE_DET_1V8: U101.J21 (NAND_DATA03)
HSW_4G_STATE: U101.L1 (SAI1_RXFS)
HSW_CA_STATE: U101.K1 (SAI1_RXC)
HSW_WIFI_STATE: U101.H1 (SAI1_TXFS)
HUB_PWR_3V3_EN: U101.K7 (GPIO1_IO14)
HUB_RESET: U101.L7 (GPIO1_IO12)
I2C1_SCL: Q5.3 (S), R3.2, U3.10 (B1)
I2C1_SCL_1V8: Q5.2 (D), R301.2, U3.2 (A1), U101.E7 (I2C1_SCL)
I2C1_SDA: Q4.3 (S), R2.2, U3.7 (B4)
I2C1_SDA_1V8: Q4.2 (D), R302.2, U3.5 (A4), U101.E8 (I2C1_SDA)
I2C2_SCL: R303.2, U101.G7 (I2C2_SCL)
I2C2_SDA: R304.2, U101.F7 (I2C2_SDA)
I2C3_SCL: R305.2, U101.G8 (I2C3_SCL)
I2C3_SDA: R306.2, U101.E9 (I2C3_SDA)
I2C4_SCL: R307.2, U101.F8 (I2C4_SCL)
I2C4_SDA: R308.2, U101.F9 (I2C4_SDA)
INT_LIGHT: U101.J20 (NAND_DATA01)
INT_M/A/G: U101.L4 (SAI5_RXD1)
LED_B: U101.K6 (GPIO1_IO13)
LED_G: U101.D3 (SAI3_MCLK)
LED_R: U101.F6 (SPDIF_TX)
MOTO: U101.E6 (SPDIF_EXT_CLK)
NFC_EN: U101.G4 (SAI3_RXFS)
NFC_IRQ: U101.E1 (SAI1_TXC)
NVCC_SNVS_3V3: R2.1, R3.1, U3.11 (VCCB)
NWDOG: R104.2
unnamed: C46.1, U101.T7 (GPIO1_IO01)
unnamed: C46.2, D16.1 (C), D20.2 (A)
unnamed: C68.1, D20.1 (C)
unnamed: R27.1, U101.L6 (GPIO1_IO11)
unnamed: R104.1, U101.R4 (GPIO1_IO02)
unnamed: R219.1, U101.J6 (GPIO1_IO15)
unnamed: R221.1, U101.D5 (ECSPI1_SCLK)
unnamed: R225.2, U101.C4 (SAI3_TXC)
unnamed: R226.1, U101.L22 (SD2_CLK)
PMIC_NINT: U101.N6 (GPIO1_IO07)
PWR_KEY: U101.H21 (NAND_CLE)
RTC_INT: U101.M6 (GPIO1_IO09)
SAI1_RXD0: U101.K2 (SAI1_RXD0)
SAI1_RXD1: U101.L2 (SAI1_RXD1)
SAI1_RXD2: U101.H2 (SAI1_RXD2)
SAI1_RXD3: U101.J2 (SAI1_RXD3)
SAI1_RXD4: U101.J1 (SAI1_RXD4)
SAI1_RXD5: U101.F1 (SAI1_RXD5)
SAI1_RXD6: U101.G2 (SAI1_RXD6)
SAI1_RXD7: U101.G1 (SAI1_RXD7)
SAI1_TXD0: U101.F2 (SAI1_TXD0)
SAI1_TXD1: U101.E2 (SAI1_TXD1)
SAI1_TXD2: U101.B2 (SAI1_TXD2)
SAI1_TXD3: U101.D1 (SAI1_TXD3)
SAI1_TXD4: U101.D2 (SAI1_TXD4)
SAI1_TXD5: U101.C2 (SAI1_TXD5)
SAI1_TXD6: U101.B3 (SAI1_TXD6)
SAI1_TXD7: U101.C1 (SAI1_TXD7)
SAI2_MCLK: U101.H5 (SAI2_MCLK)
SAI2_RXD: U101.H6 (SAI2_RXD0)
SAI2_TXC: U101.J5 (SAI2_TXC)
SAI2_TXD: U101.G5 (SAI2_TXD0)
SAI2_TXFS: U101.H4 (SAI2_TXFS)
SAI3_RXD: U101.F3 (SAI3_RXD)
SAI3_TXC: R225.1
SAI3_TXD: U101.C3 (SAI3_TXD)
SAI3_TXFS: U101.G3 (SAI3_TXFS)
SD1_CLK: U101.L25 (SD1_CLK)
SD1_CMD: U101.L24 (SD1_CMD)
SD1_DATA0: U101.M25 (SD1_DATA0)
SD1_DATA1: U101.M24 (SD1_DATA1)
SD1_DATA2: U101.N25 (SD1_DATA2)
SD1_DATA3: U101.P25 (SD1_DATA3)
SD1_DATA4: U101.N24 (SD1_DATA4)
SD1_DATA5: U101.P24 (SD1_DATA5)
SD1_DATA6: U101.R25 (SD1_DATA6)
SD1_DATA7: U101.T25 (SD1_DATA7)
SD1_NRST: U101.R24 (SD1_RESET_B)
SD1_STROBE: U101.T24 (SD1_STROBE)
SD2_CLK: R226.2
SD2_CMD: U101.M22 (SD2_CMD)
SD2_DATA0: U101.N22 (SD2_DATA0)
SD2_DATA1: U101.N21 (SD2_DATA1)
SD2_DATA2: U101.P22 (SD2_DATA2)
SD2_DATA3: U101.P21 (SD2_DATA3)
SD2_NCD: Q8.3 (S), R31.1, U101.L21 (SD2_CD_B)
SD2_NRST: U101.R22 (SD2_RESET_B)
SDIO_WAKE: U101.M21 (SD2_WP)
SMC_BOOT0: U101.D7 (UART4_TXD)
SMC_PWR_3V3_EN: U101.N5 (GPIO1_IO06)
SPI_SS1: U101.C6 (UART4_RXD)
TCPC_NINT: U101.M7 (GPIO1_IO10)
TF_NCD: U101.J22 (NAND_DATA05)
TF_PWR_3V3_EN: U101.P4 (GPIO1_IO03)
TP_NINT: U101.U21 (ENET_RD1)
TP_RST: U101.T21 (ENET_RX_CTL)
TYPEC_HRESET: U101.K5 (SAI5_RXD3)
TYPEC_MUX_EN: R27.2
UART1_RXD: U101.C7 (UART1_RXD)
UART1_TXD: U101.A7 (UART1_TXD)
UART2_RXD: U101.B6 (UART2_RXD)
UART2_TXD: U101.D6 (UART2_TXD)
UART3_RXD: U101.A6 (UART3_RXD)
UART3_TXD: U101.B7 (UART3_TXD)
UART4_CTS: U101.B5 (ECSPI2_MISO)
UART4_RTS: U101.A5 (ECSPI2_SS0)
UART4_RXD: U101.C5 (ECSPI2_SCLK)
UART4_TXD: U101.E5 (ECSPI2_MOSI)
VDD_1V8: Q4.1 (GATE), Q5.1 (GATE), R31.2, R301.1, R302.1, R303.1, R304.1, R305.1, R306.1, R307.1, R308.1, U3.1 (VCCA), U3.12 (/OE)
VDD_3V3: D16.2 (A)
VOL+: U101.N20 (ENET_MDC)
VOL-: U101.N19 (ENET_MDIO)
WIFI3V3_EN: U101.L20 (NAND_DATA04)
WIFI_REG_ON: U101.F4 (SAI3_RXC)
