gralco/l5-schematic/CAD/PADS/librem5_mainboard/librem5_mainboard_kicad_conversion/librem5_mainboard_sheet6.kicad_sch

## KiCad design CAD/PADS/librem5_mainboard/librem5_mainboard_kicad_conversion/librem5_mainboard_sheet6.kicad_sch (2026-05-21)

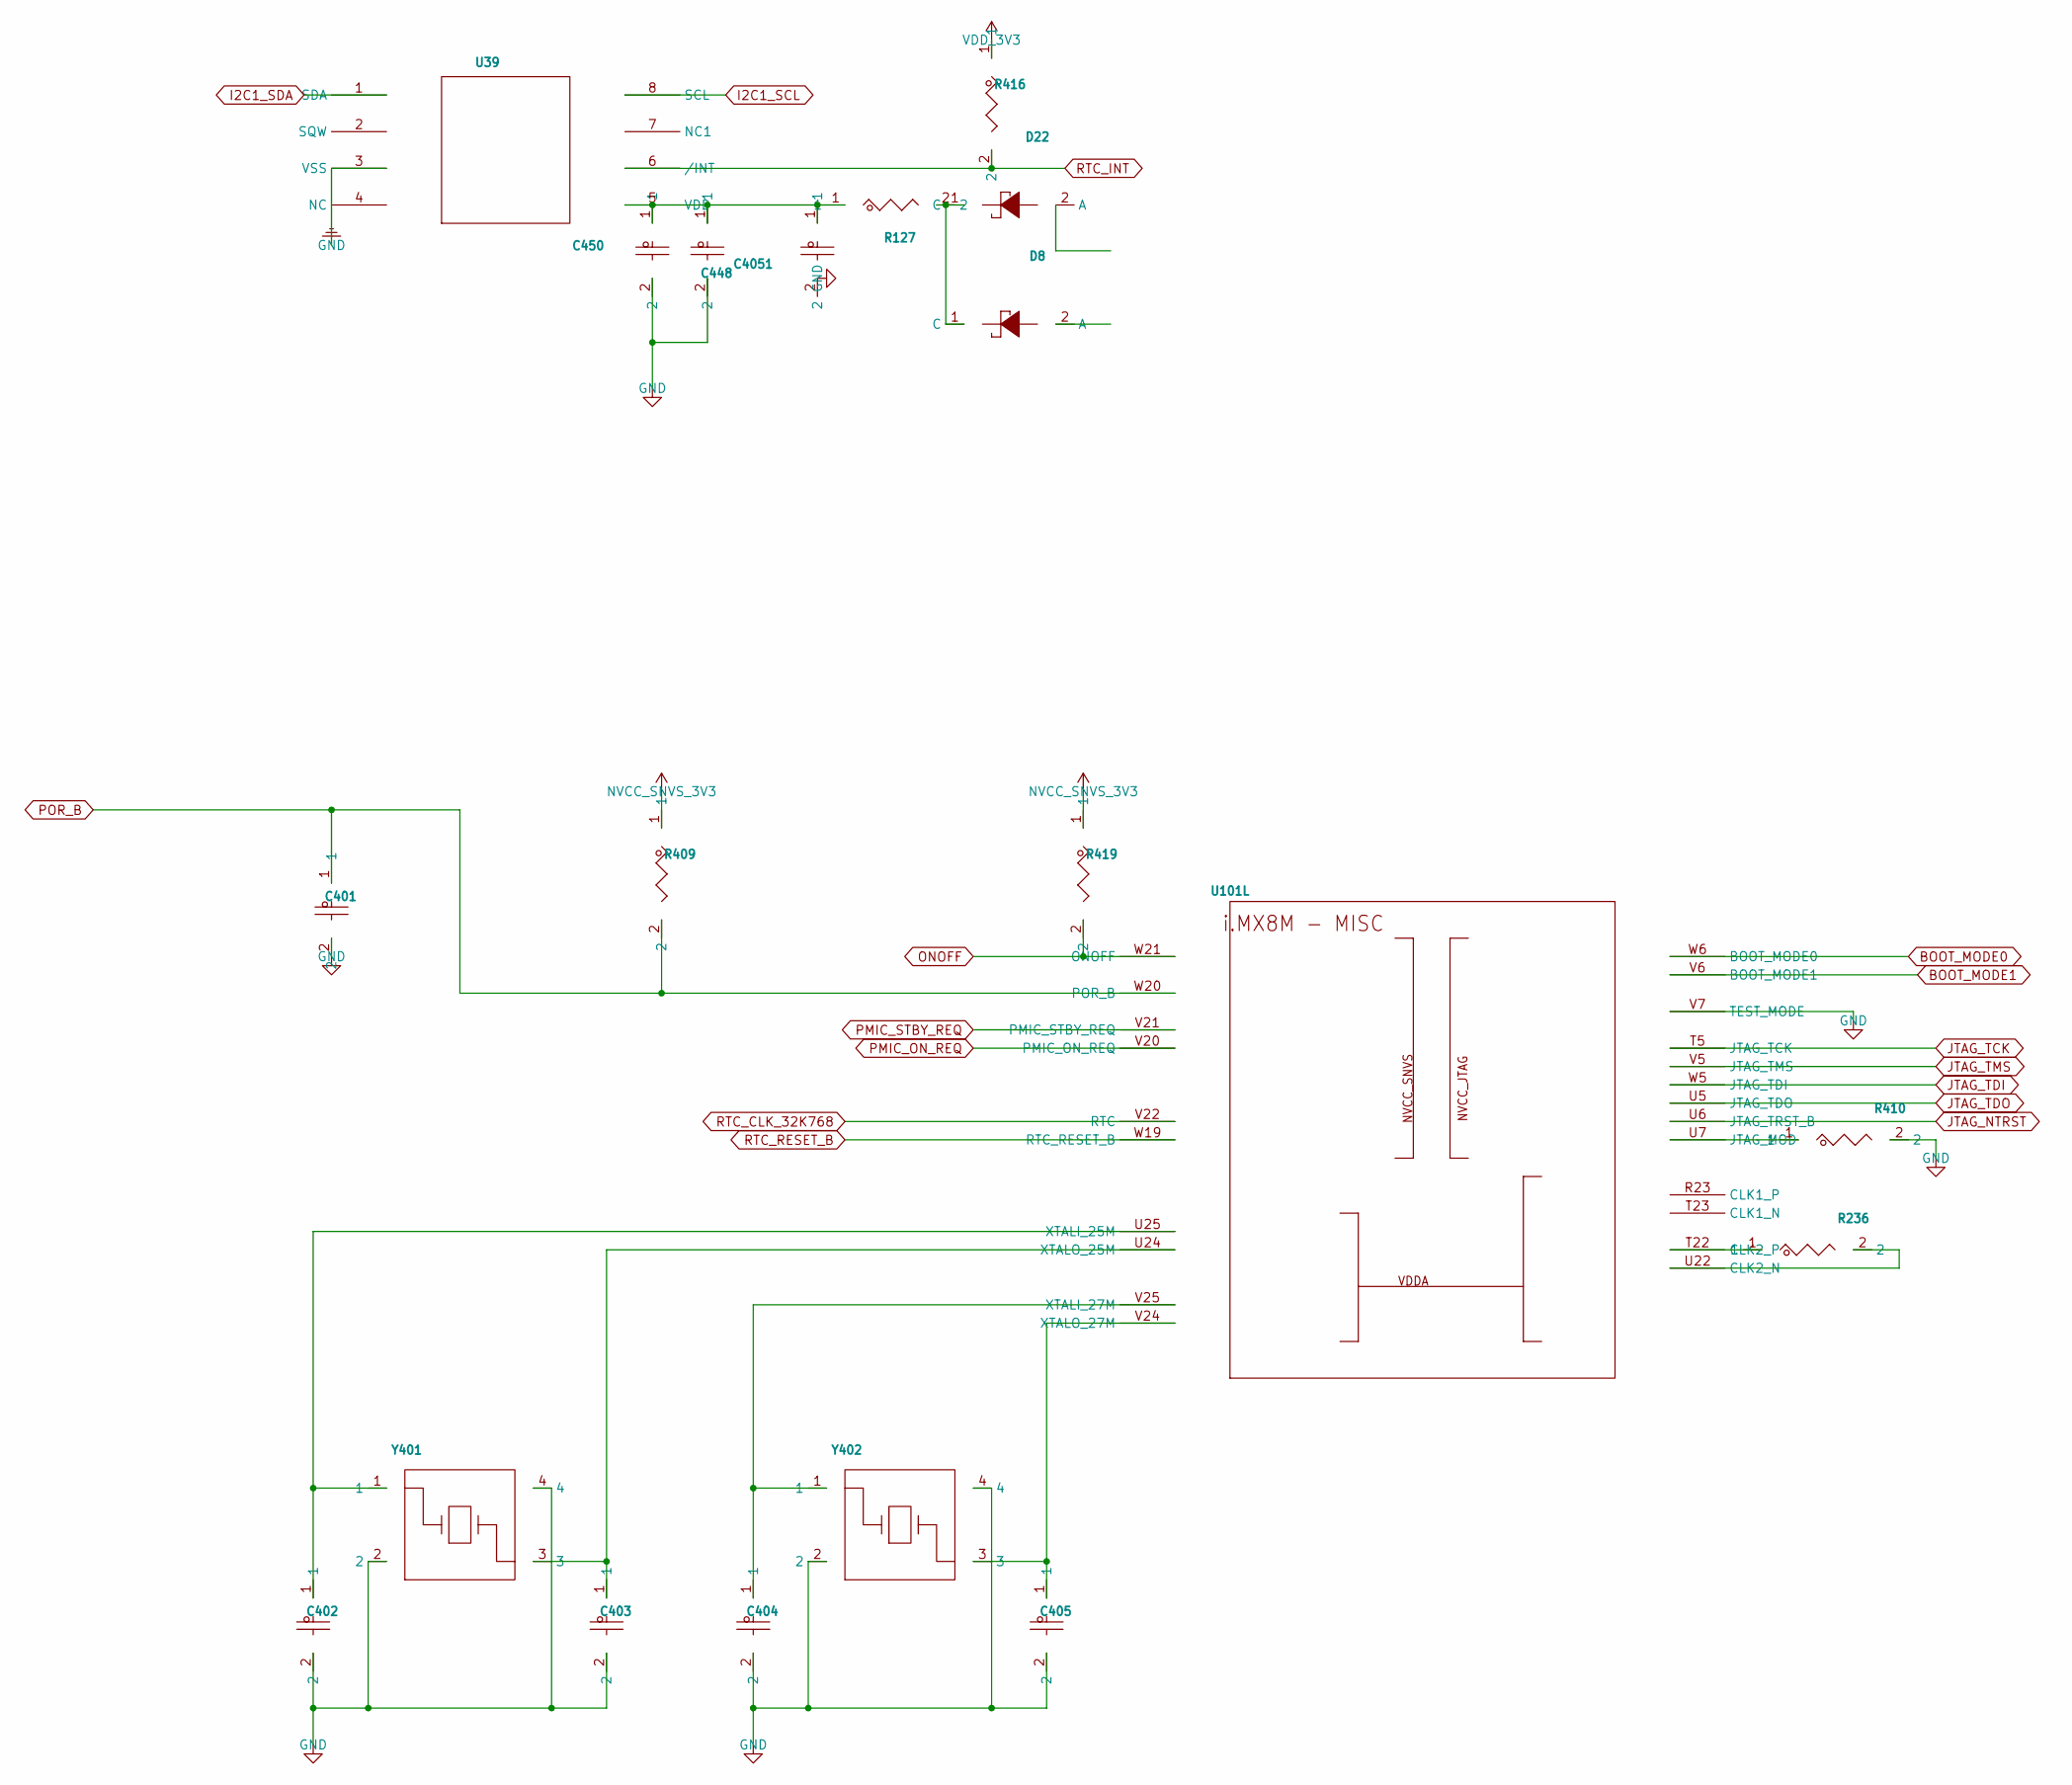
[picture p40: schematic librem5_mainboard_sheet6.kicad_sch]

Parts:
C401, C4051: C0201; VOLTAGE 6.3V
C402, C403, C404, C405: C0201; VOLTAGE 25V
C448, C450: C0603; VOLTAGE 6.3V
D8, D22: DIODE_SCHTKY_0
R127, R236, R409, R410, R416, R419: RES_2
U39: RV-4162-C7
U101: MIMX8MQ6DVAJZAA_BGA621
Y401, Y402: XTAL_13Y

Connections:
BOOT_MODE0: U101.W6 (BOOT_MODE0)
BOOT_MODE1: U101.V6 (BOOT_MODE1)
GND: C401.2, C402.2, C403.2, C404.2, C405.2, C448.2, C450.2, C4051.2, R410.2, U39.3 (VSS), U101.V7 (TEST_MODE), Y401.2, Y401.4, Y402.2, Y402.4
I2C1_SCL: U39.8 (SCL)
I2C1_SDA: U39.1 (SDA)
JTAG_NTRST: U101.U6 (JTAG_TRST_B)
JTAG_TCK: U101.T5 (JTAG_TCK)
JTAG_TDI: U101.W5 (JTAG_TDI)
JTAG_TDO: U101.U5 (JTAG_TDO)
JTAG_TMS: U101.V5 (JTAG_TMS)
NVCC_SNVS_3V3: R409.1, R419.1
unnamed: C402.1, U101.U25 (XTALI_25M), Y401.1
unnamed: C403.1, U101.U24 (XTALO_25M), Y401.3
unnamed: C404.1, U101.V25 (XTALI_27M), Y402.1
unnamed: C405.1, U101.V24 (XTALO_27M), Y402.3
unnamed: C448.1, C450.1, C4051.1, R127.1, U39.5 (VDD)
unnamed: D8.1 (C), D22.1 (C), R127.2
unnamed: R236.1, U101.T22 (CLK2_P)
unnamed: R236.2, U101.U22 (CLK2_N)
unnamed: R410.1, U101.U7 (JTAG_MOD)
ONOFF: R419.2, U101.W21 (ONOFF)
PMIC_ON_REQ: U101.V20 (PMIC_ON_REQ)
PMIC_STBY_REQ: U101.V21 (PMIC_STBY_REQ)
POR_B: C401.1, R409.2, U101.W20 (POR_B)
RTC_CLK_32K768: U101.V22 (RTC)
RTC_INT: R416.2, U39.6 (/INT)
RTC_RESET_B: U101.W19 (RTC_RESET_B)
VDD_3V3: R416.1
