gralco/l5-schematic/CAD/PADS/librem5_mainboard/librem5_mainboard_kicad_conversion/librem5_mainboard_sheet7.kicad_sch

## KiCad design CAD/PADS/librem5_mainboard/librem5_mainboard_kicad_conversion/librem5_mainboard_sheet7.kicad_sch (2026-05-21)

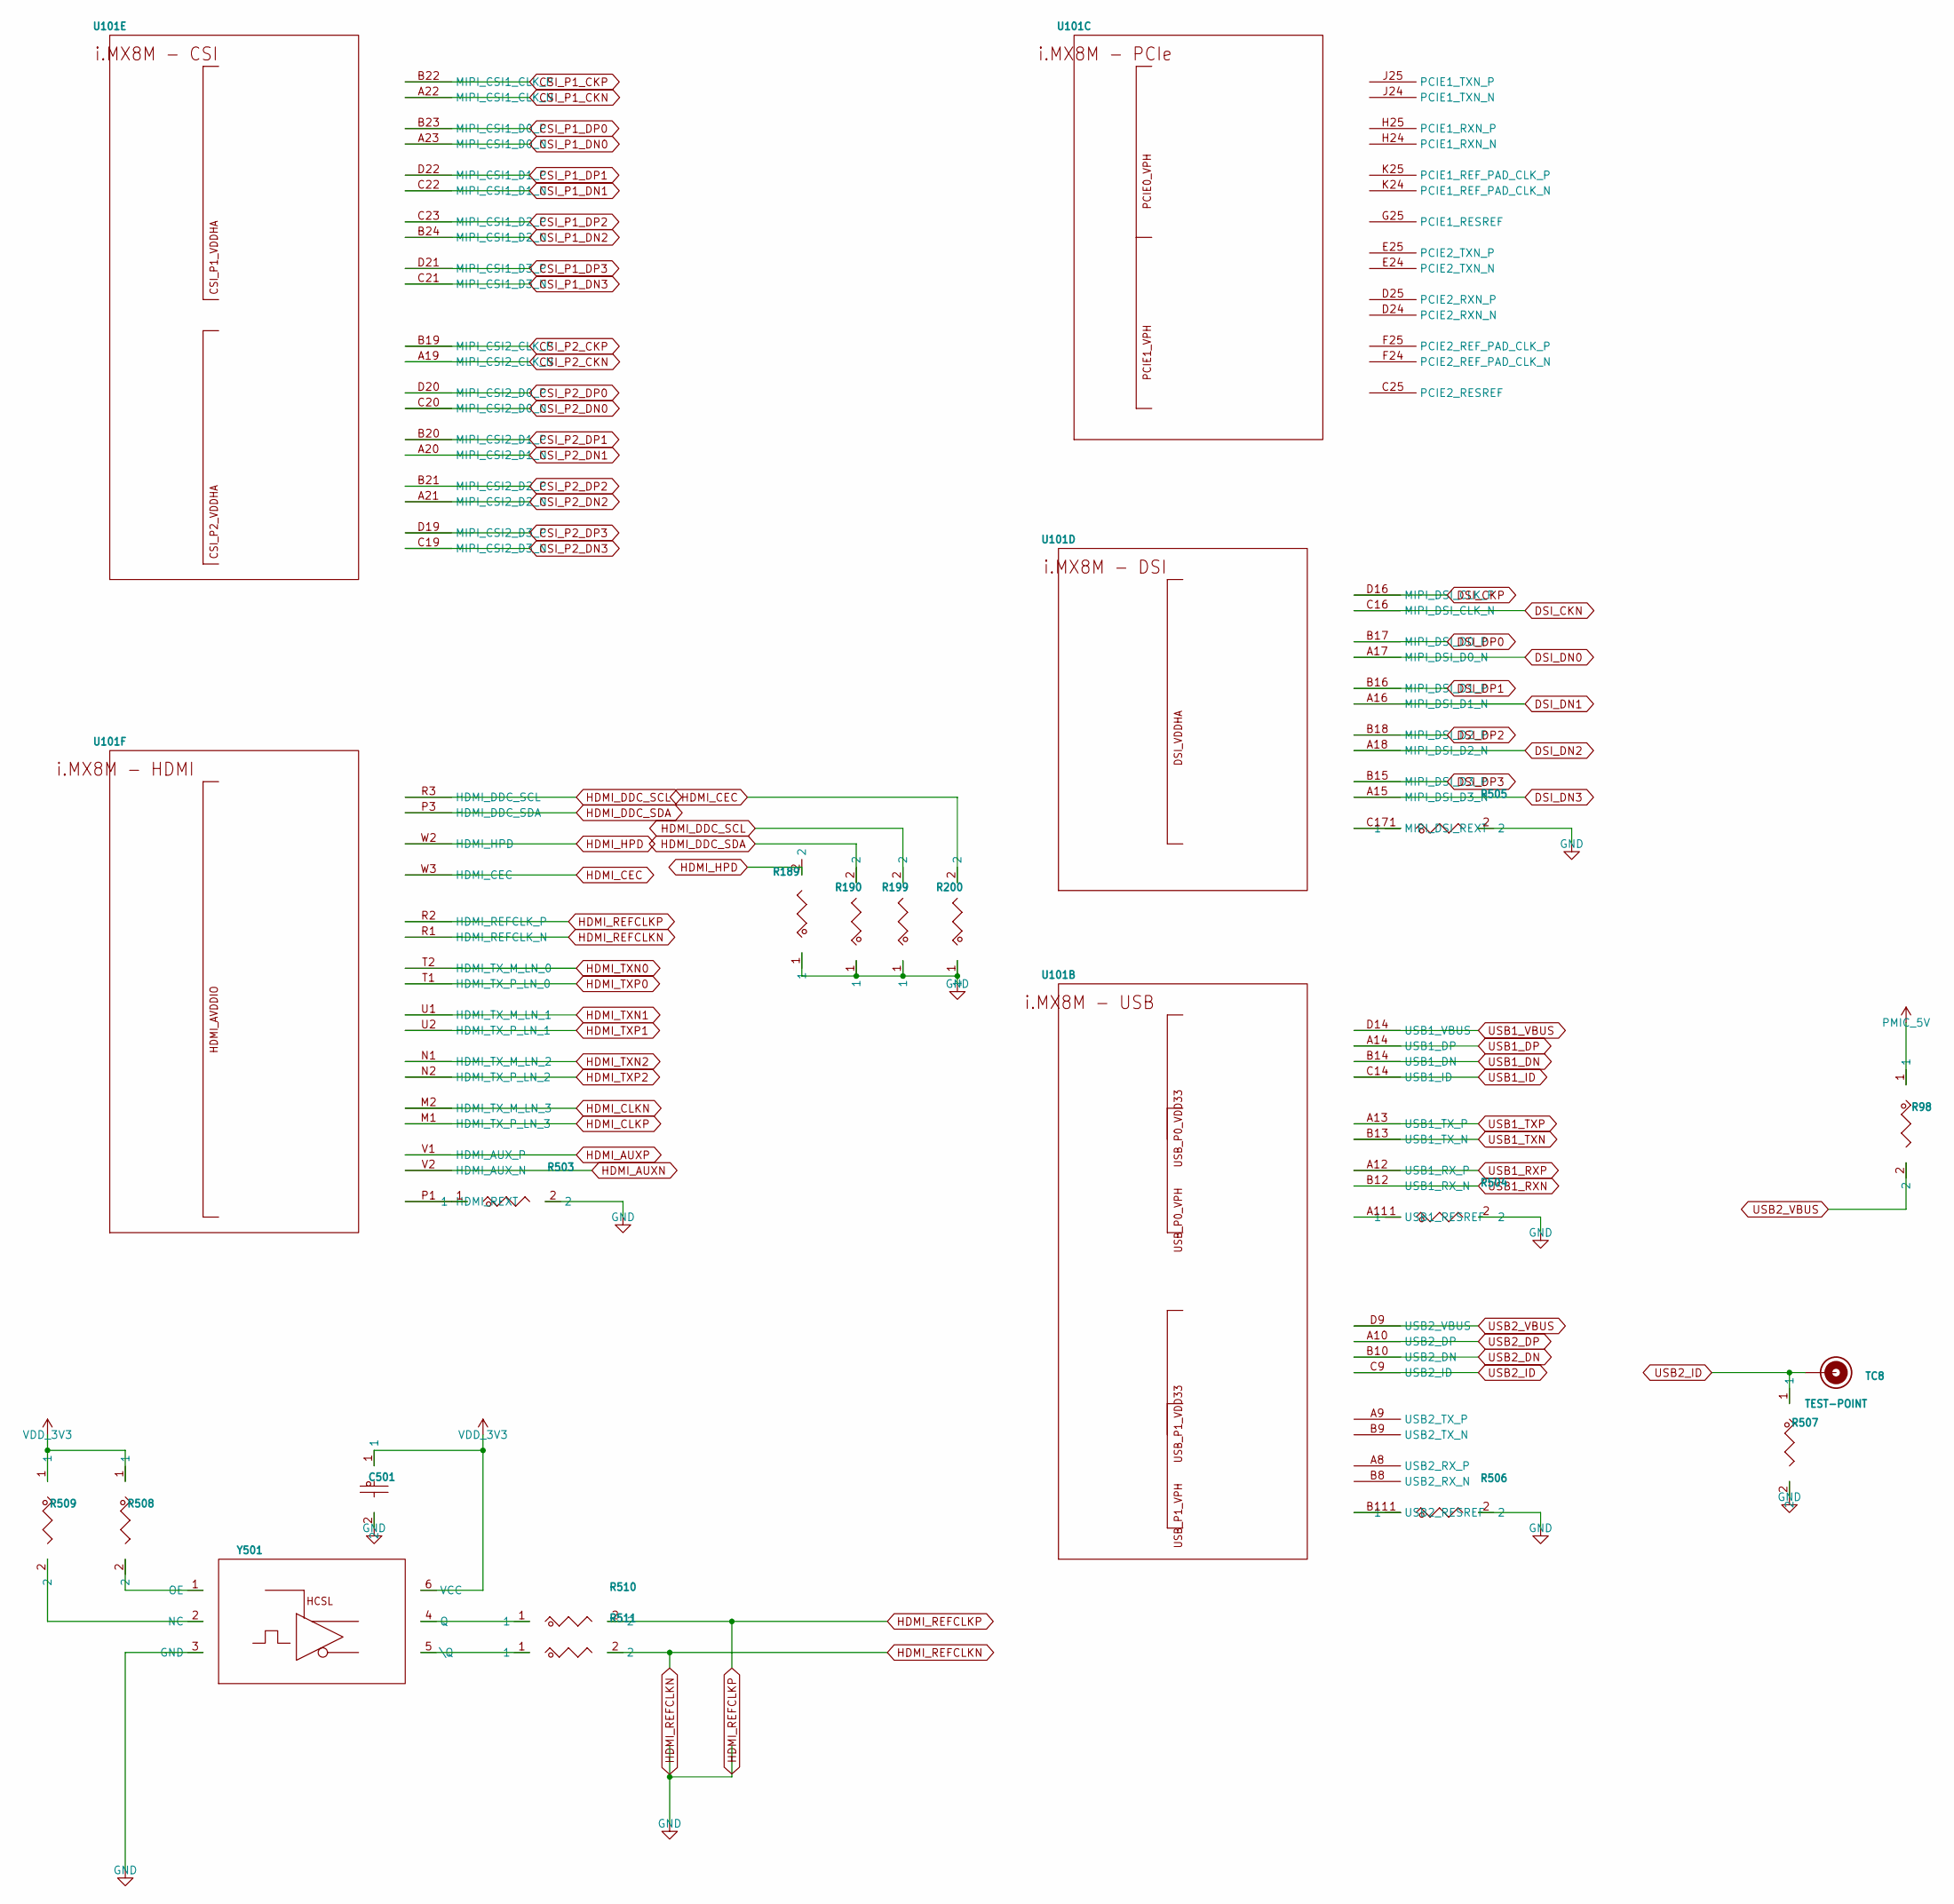
[picture p41: schematic librem5_mainboard_sheet7.kicad_sch]

Parts:
C501: C0201; VOLTAGE 6.3V
R98, R189, R190, R199, R200, R503, R504, R505, R506, R507, R508, R509, R510, R511: RES_2
TC8: TEST-POINT
U101: MIMX8MQ6DVAJZAA_BGA621
Y501: NX5427001Z_6P

Connections:
CSI_P1_CKN: U101.A22 (MIPI_CSI1_CLK_N)
CSI_P1_CKP: U101.B22 (MIPI_CSI1_CLK_P)
CSI_P1_DN0: U101.A23 (MIPI_CSI1_D0_N)
CSI_P1_DN1: U101.C22 (MIPI_CSI1_D1_N)
CSI_P1_DN2: U101.B24 (MIPI_CSI1_D2_N)
CSI_P1_DN3: U101.C21 (MIPI_CSI1_D3_N)
CSI_P1_DP0: U101.B23 (MIPI_CSI1_D0_P)
CSI_P1_DP1: U101.D22 (MIPI_CSI1_D1_P)
CSI_P1_DP2: U101.C23 (MIPI_CSI1_D2_P)
CSI_P1_DP3: U101.D21 (MIPI_CSI1_D3_P)
CSI_P2_CKN: U101.A19 (MIPI_CSI2_CLK_N)
CSI_P2_CKP: U101.B19 (MIPI_CSI2_CLK_P)
CSI_P2_DN0: U101.C20 (MIPI_CSI2_D0_N)
CSI_P2_DN1: U101.A20 (MIPI_CSI2_D1_N)
CSI_P2_DN2: U101.A21 (MIPI_CSI2_D2_N)
CSI_P2_DN3: U101.C19 (MIPI_CSI2_D3_N)
CSI_P2_DP0: U101.D20 (MIPI_CSI2_D0_P)
CSI_P2_DP1: U101.B20 (MIPI_CSI2_D1_P)
CSI_P2_DP2: U101.B21 (MIPI_CSI2_D2_P)
CSI_P2_DP3: U101.D19 (MIPI_CSI2_D3_P)
DSI_CKN: U101.C16 (MIPI_DSI_CLK_N)
DSI_CKP: U101.D16 (MIPI_DSI_CLK_P)
DSI_DN0: U101.A17 (MIPI_DSI_D0_N)
DSI_DN1: U101.A16 (MIPI_DSI_D1_N)
DSI_DN2: U101.A18 (MIPI_DSI_D2_N)
DSI_DN3: U101.A15 (MIPI_DSI_D3_N)
DSI_DP0: U101.B17 (MIPI_DSI_D0_P)
DSI_DP1: U101.B16 (MIPI_DSI_D1_P)
DSI_DP2: U101.B18 (MIPI_DSI_D2_P)
DSI_DP3: U101.B15 (MIPI_DSI_D3_P)
GND: C501.2, R189.1, R190.1, R199.1, R200.1, R503.2, R504.2, R505.2, R506.2, R507.2, Y501.3 (GND)
HDMI_AUXN: U101.V2 (HDMI_AUX_N)
HDMI_AUXP: U101.V1 (HDMI_AUX_P)
HDMI_CEC: R200.2, U101.W3 (HDMI_CEC)
HDMI_CLKN: U101.M2 (HDMI_TX_M_LN_3)
HDMI_CLKP: U101.M1 (HDMI_TX_P_LN_3)
HDMI_DDC_SCL: R199.2, U101.R3 (HDMI_DDC_SCL)
HDMI_DDC_SDA: R190.2, U101.P3 (HDMI_DDC_SDA)
HDMI_HPD: R189.2, U101.W2 (HDMI_HPD)
HDMI_REFCLKN: R511.2, U101.R1 (HDMI_REFCLK_N)
HDMI_REFCLKP: R510.2, U101.R2 (HDMI_REFCLK_P)
HDMI_TXN0: U101.T2 (HDMI_TX_M_LN_0)
HDMI_TXN1: U101.U1 (HDMI_TX_M_LN_1)
HDMI_TXN2: U101.N1 (HDMI_TX_M_LN_2)
HDMI_TXP0: U101.T1 (HDMI_TX_P_LN_0)
HDMI_TXP1: U101.U2 (HDMI_TX_P_LN_1)
HDMI_TXP2: U101.N2 (HDMI_TX_P_LN_2)
unnamed: R503.1, U101.P1 (HDMI_REXT)
unnamed: R504.1, U101.A11 (USB1_RESREF)
unnamed: R505.1, U101.C17 (MIPI_DSI_REXT)
unnamed: R506.1, U101.B11 (USB2_RESREF)
unnamed: R508.2, Y501.1 (OE)
unnamed: R509.2, Y501.2 (NC)
unnamed: R510.1, Y501.4 (Q)
unnamed: R511.1, Y501.5 (\Q)
PMIC_5V: R98.1
USB1_DN: U101.B14 (USB1_DN)
USB1_DP: U101.A14 (USB1_DP)
USB1_ID: U101.C14 (USB1_ID)
USB1_RXN: U101.B12 (USB1_RX_N)
USB1_RXP: U101.A12 (USB1_RX_P)
USB1_TXN: U101.B13 (USB1_TX_N)
USB1_TXP: U101.A13 (USB1_TX_P)
USB1_VBUS: U101.D14 (USB1_VBUS)
USB2_DN: U101.B10 (USB2_DN)
USB2_DP: U101.A10 (USB2_DP)
USB2_ID: R507.1, TC8.1, U101.C9 (USB2_ID)
USB2_VBUS: R98.2, U101.D9 (USB2_VBUS)
VDD_3V3: C501.1, R508.1, R509.1, Y501.6 (VCC)
