gralco/l5-schematic/CAD/PADS/librem5_mainboard/librem5_mainboard_kicad_conversion/librem5_mainboard_sheet8.kicad_sch

## KiCad design CAD/PADS/librem5_mainboard/librem5_mainboard_kicad_conversion/librem5_mainboard_sheet8.kicad_sch (2026-05-21)

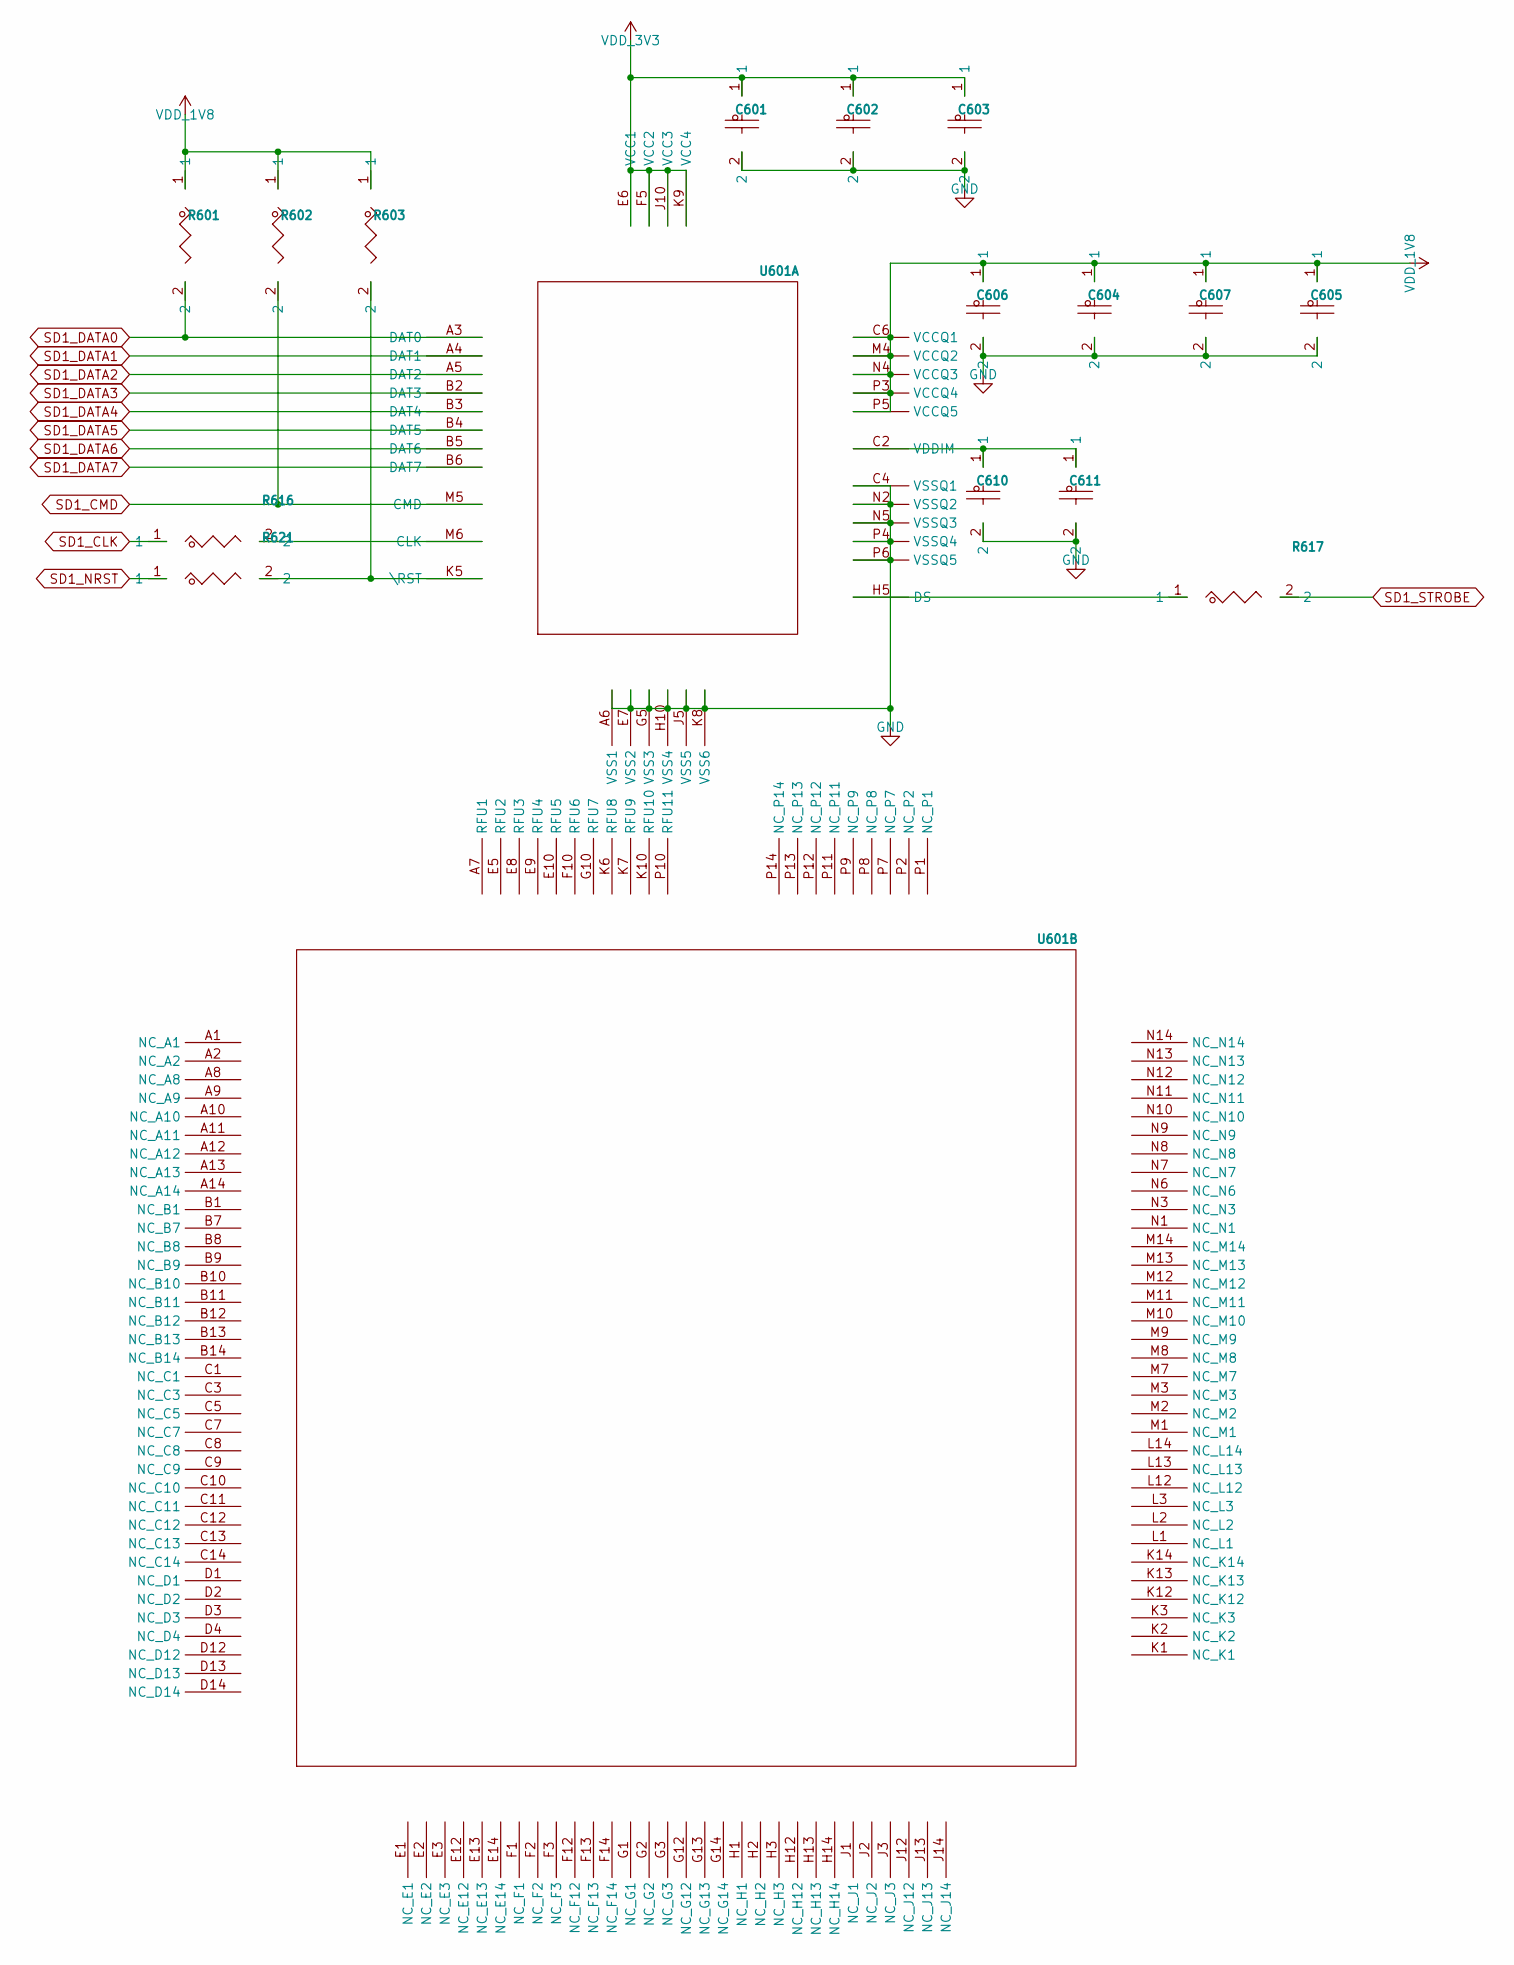
[picture p42: schematic librem5_mainboard_sheet8.kicad_sch]

Parts:
C601, C605: C0402; VOLTAGE 6.3V
C602, C603, C604, C606, C607, C610, C611: C0201; VOLTAGE 6.3V
R601, R602, R603, R616, R617, R621: RES_2
U601: MTFC8GACAEAM_VFBGA_0

Connections:
GND: C601.2, C602.2, C603.2, C604.2, C605.2, C606.2, C607.2, C610.2, C611.2, U601.A6 (VSS1), U601.C4 (VSSQ1), U601.E7 (VSS2), U601.G5 (VSS3), U601.H10 (VSS4), U601.J5 (VSS5), U601.K8 (VSS6), U601.N2 (VSSQ2), U601.N5 (VSSQ3), U601.P4 (VSSQ4), U601.P6 (VSSQ5)
unnamed: C610.1, C611.1, U601.C2 (VDDIM)
unnamed: R603.2, R621.2, U601.K5 (\RST)
unnamed: R616.2, U601.M6 (CLK)
unnamed: R617.1, U601.H5 (DS)
SD1_CLK: R616.1
SD1_CMD: R602.2, U601.M5 (CMD)
SD1_DATA0: R601.2, U601.A3 (DAT0)
SD1_DATA1: U601.A4 (DAT1)
SD1_DATA2: U601.A5 (DAT2)
SD1_DATA3: U601.B2 (DAT3)
SD1_DATA4: U601.B3 (DAT4)
SD1_DATA5: U601.B4 (DAT5)
SD1_DATA6: U601.B5 (DAT6)
SD1_DATA7: U601.B6 (DAT7)
SD1_NRST: R621.1
SD1_STROBE: R617.2
VDD_1V8: C604.1, C605.1, C606.1, C607.1, R601.1, R602.1, R603.1, U601.C6 (VCCQ1), U601.M4 (VCCQ2), U601.N4 (VCCQ3), U601.P3 (VCCQ4), U601.P5 (VCCQ5)
VDD_3V3: C601.1, C602.1, C603.1, U601.E6 (VCC1), U601.F5 (VCC2), U601.J10 (VCC3), U601.K9 (VCC4)
