gralco/l5-schematic/CAD/PADS/librem5_mainboard/librem5_mainboard_kicad_conversion/librem5_mainboard_sheet9.kicad_sch

## KiCad design CAD/PADS/librem5_mainboard/librem5_mainboard_kicad_conversion/librem5_mainboard_sheet9.kicad_sch (2026-05-21)

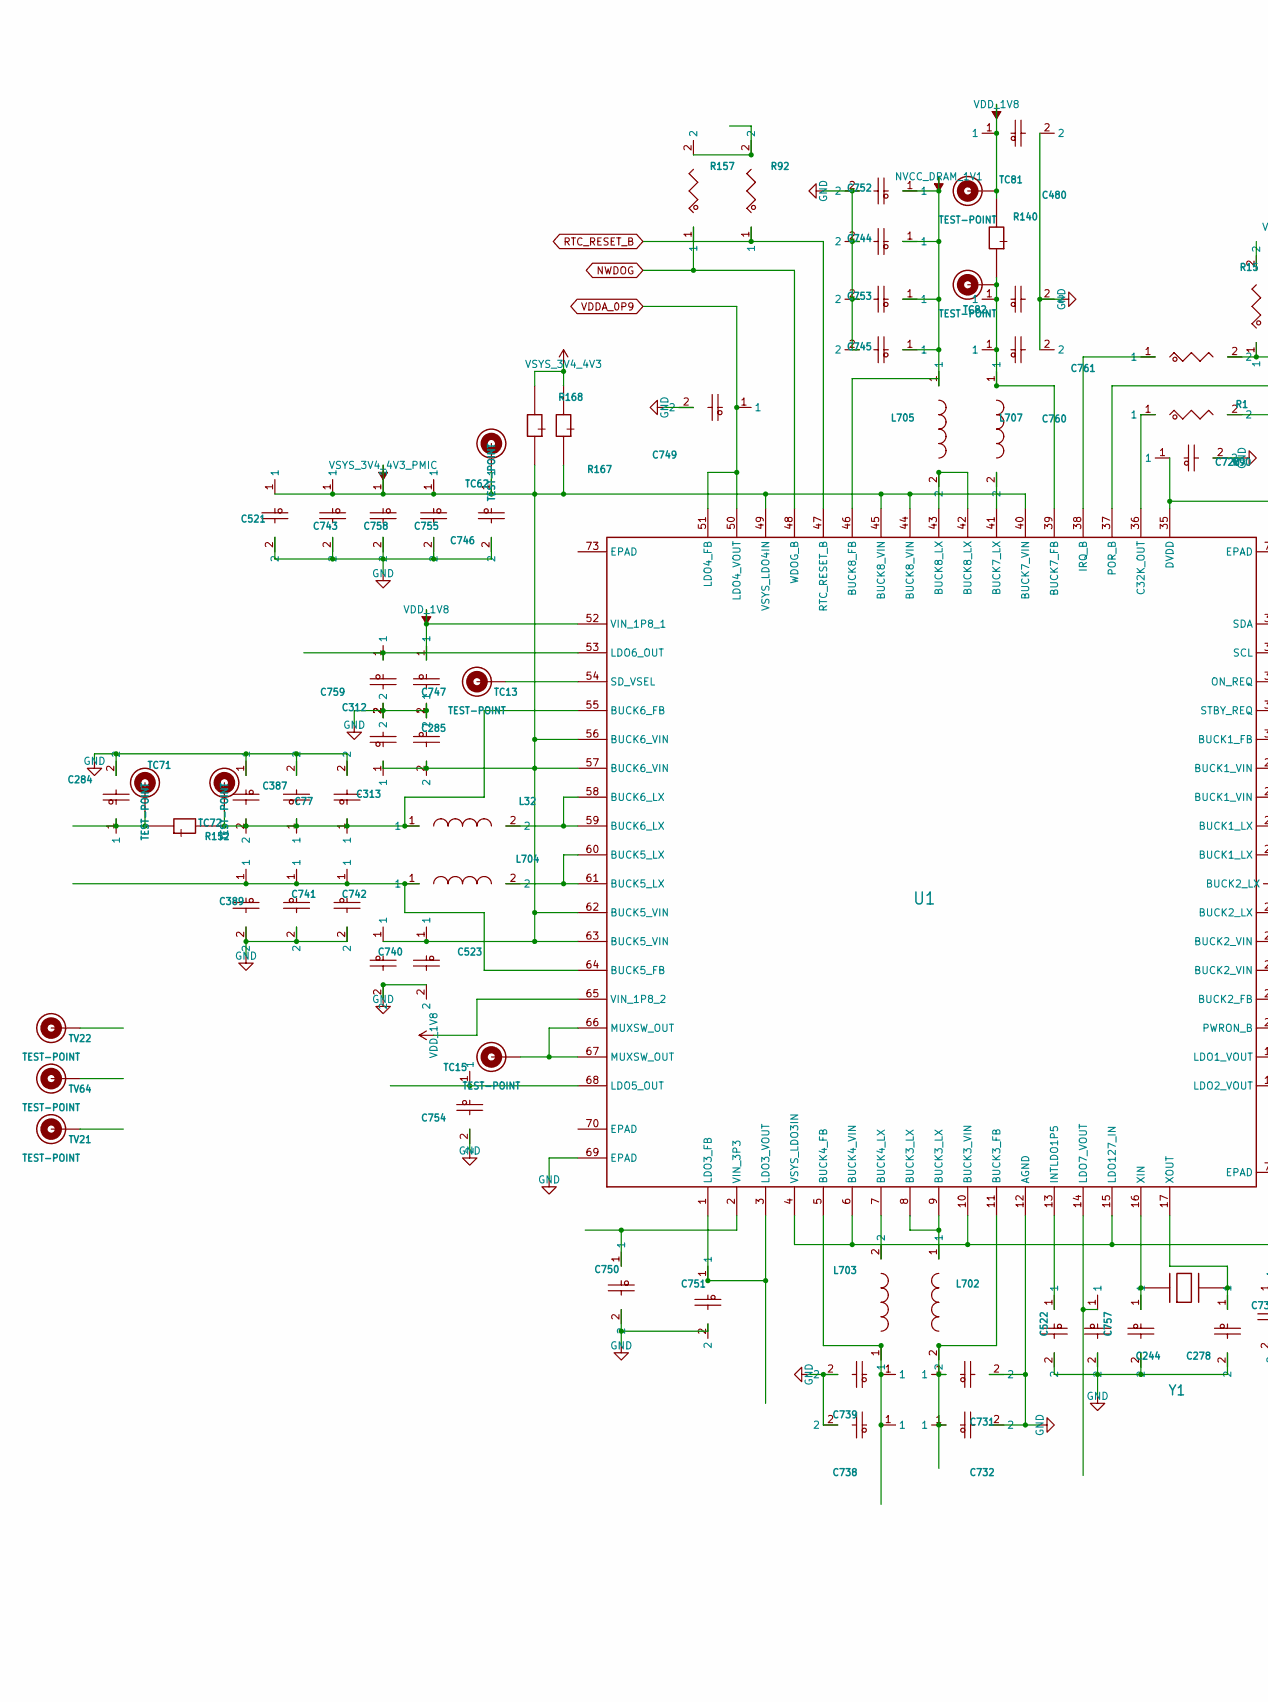
[picture p43: schematic librem5_mainboard_sheet9.kicad_sch, part in row 1, column 1]

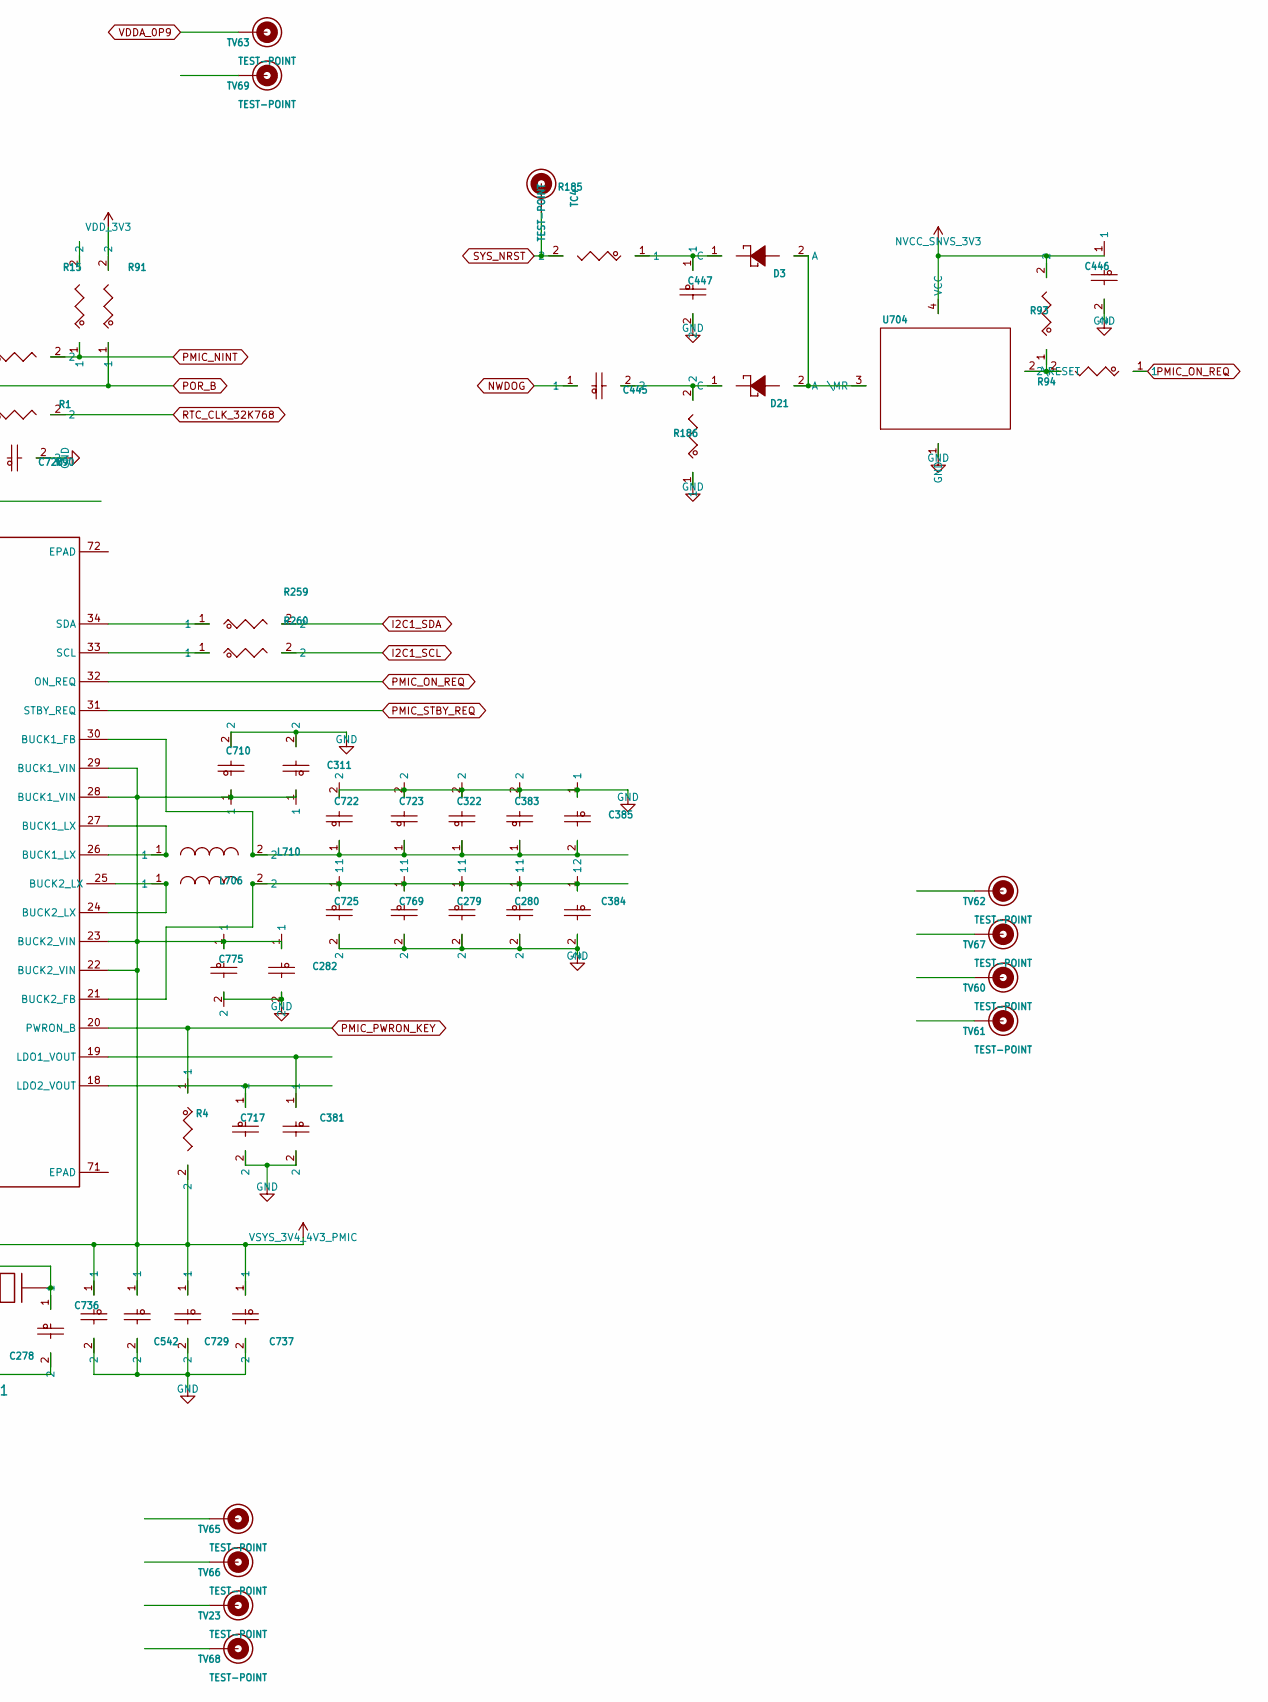
[picture p44: schematic librem5_mainboard_sheet9.kicad_sch, part in row 1, column 2]

Parts:
C77, C284, C285, C313, C521, C710, C722, C723, C725, C731, C739, C741, C742, C745, C753, C760, C769, C775: C0603; VOLTAGE 6.3V
C244, C278: C0201
C279, C280, C322, C383, C732, C738, C744, C752, C761: C0603
C282, C311, C312, C480, C542, C729, C737, C743, C747, C749, C750, C751, C754, C755, C757, C759: C0402; VOLTAGE 6.3V
C381, C384, C385, C387, C389, C445, C446, C522, C523, C717, C728, C746, C758: C0201; VOLTAGE 6.3V
C447: C0201; VOLTAGE 25V
C736, C740: C0603; Tolerance 10%; VOLTAGE 6.3V; MFG_PN01 C0603X5R6R3-475KNP
D3, D21: DIODE_SCHTKY_0
L32, L702, L703, L704, L705, L706, L707, L710: INDUCTOR
R1, R4, R15, R90, R91, R92, R93, R94, R157, R185, R186: RES_2
R140, R152, R167, R168: CURRENT_R
R259, R260: R_0201
TC4, TC13, TC15, TC62, TC71, TC72, TC81, TC82: TEST-POINT
TV21, TV22, TV23, TV60, TV61, TV62, TV63, TV64, TV65, TV66, TV67, TV68, TV69: TEST-POINT
U1: BD71837-24
U704: UM805_4P
Y1: 32768-2

Connections:
GND: C77.2, C244.2, C278.2, C279.2, C280.2, C282.2, C284.2, C285.1, C311.2, C312.2, C313.2, C322.2, C381.2, C383.2, C384.2, C385.1, C387.1, C389.2, C446.2, C447.2, C480.2, C521.2, C522.2, C523.2, C542.2, C710.2, C717.2, C722.2, C723.2, C725.2, C728.2, C729.2, C731.2, C732.2, C736.2, C737.2, C738.2, C739.2, C740.2, C741.2, C742.2, C743.2, C744.2, C745.2, C746.2, C747.2, C749.2, C750.2, C751.2, C752.2, C753.2, C754.2, C755.2, C757.2, C758.2, C759.2, C760.2, C761.2, C769.2, C775.2, R186.1, U1.12 (AGND), U1.69 (EPAD), U704.1 (GND)
I2C1_SCL: R260.2
I2C1_SDA: R259.2
NVCC_DRAM_1V1: C744.1, C745.1, C752.1, C753.1, L705.1
NVCC_SNVS_3V3: C446.1, R93.2, U704.4 (VCC)
NWDOG: C445.1, R157.1, U1.48 (WDOG_B)
unnamed: C244.1, U1.16 (XIN), Y1.1
unnamed: C278.1, U1.17 (XOUT), Y1.2
unnamed: C279.1, C280.1, C384.1, C725.1, C769.1, L706.2, U1.21 (BUCK2_FB)
unnamed: C284.1, R152.1, TC71.1
unnamed: C77.1, C313.1, C387.2, L32.1, R152.2, TC72.1, U1.55 (BUCK6_FB)
unnamed: C322.1, C383.1, C385.2, C722.1, C723.1, L710.2, U1.30 (BUCK1_FB)
unnamed: C381.1, U1.19 (LDO1_VOUT)
unnamed: C389.1, C741.1, C742.1, L704.1, U1.64 (BUCK5_FB)
unnamed: C445.2, D21.1 (C), R186.2
unnamed: C447.1, D3.1 (C), R185.1
unnamed: C522.1, U1.13 (INTLDO1P5)
unnamed: C717.1, U1.18 (LDO2_VOUT)
unnamed: C728.1, U1.35 (DVDD)
unnamed: C731.1, C732.1, L702.2, U1.11 (BUCK3_FB)
unnamed: C738.1, C739.1, L703.1, U1.5 (BUCK4_FB)
unnamed: C750.1, U1.2 (VIN_3P3)
unnamed: C751.1, U1.1 (LDO3_FB), U1.3 (LDO3_VOUT)
unnamed: C754.1, U1.68 (LDO5_OUT)
unnamed: C757.1, U1.14 (LDO7_VOUT)
unnamed: C759.1, U1.53 (LDO6_OUT)
unnamed: C760.1, C761.1, L707.1, R140.1, TC82.1, U1.39 (BUCK7_FB)
unnamed: D3.2 (A), D21.2 (A), U704.3 (\MR)
unnamed: L32.2, U1.58 (BUCK6_LX), U1.59 (BUCK6_LX)
unnamed: L702.1, U1.8 (BUCK3_LX), U1.9 (BUCK3_LX)
unnamed: L703.2, U1.7 (BUCK4_LX)
unnamed: L704.2, U1.60 (BUCK5_LX), U1.61 (BUCK5_LX)
unnamed: L705.2, U1.42 (BUCK8_LX), U1.43 (BUCK8_LX)
unnamed: L706.1, U1.24 (BUCK2_LX), U1.25 (BUCK2_LX)
unnamed: L707.2, U1.41 (BUCK7_LX)
unnamed: L710.1, U1.26 (BUCK1_LX), U1.27 (BUCK1_LX)
unnamed: R1.1, U1.38 (IRQ_B)
unnamed: R90.1, U1.36 (C32K_OUT)
unnamed: R93.1, R94.2, U704.2 (\RESET)
unnamed: R92.2, R157.2
unnamed: R259.1, U1.34 (SDA)
unnamed: R260.1, U1.33 (SCL)
unnamed: TC13.1, U1.54 (SD_VSEL)
unnamed: TC15.1, U1.66 (MUXSW_OUT), U1.67 (MUXSW_OUT)
PMIC_NINT: R1.2, R15.1
PMIC_ON_REQ: R94.1, U1.32 (ON_REQ)
PMIC_PWRON_KEY: R4.1, U1.20 (PWRON_B)
PMIC_STBY_REQ: U1.31 (STBY_REQ)
POR_B: R91.1, U1.37 (POR_B)
RTC_CLK_32K768: R90.2
RTC_RESET_B: R92.1, U1.47 (RTC_RESET_B)
SYS_NRST: R185.2, TC4.1
VDDA_0P9: C749.1, TV63.1, U1.50 (LDO4_VOUT), U1.51 (LDO4_FB)
VDD_1V8: C480.1, C747.1, R140.2, TC81.1, U1.52 (VIN_1P8_1), U1.65 (VIN_1P8_2)
VDD_3V3: R91.2
VSYS_3V4_4V3: R167.2, R168.2
VSYS_3V4_4V3_PMIC: C282.1, C285.2, C311.1, C312.1, C521.1, C523.1, C542.1, C710.1, C729.1, C736.1, C737.1, C740.1, C743.1, C746.1, C755.1, C758.1, C775.1, R4.2, R167.1, R168.1, TC62.1, U1.4 (VSYS_LDO3IN), U1.6 (BUCK4_VIN), U1.10 (BUCK3_VIN), U1.15 (LDO127_IN), U1.22 (BUCK2_VIN), U1.23 (BUCK2_VIN), U1.28 (BUCK1_VIN), U1.29 (BUCK1_VIN), U1.40 (BUCK7_VIN), U1.44 (BUCK8_VIN), U1.45 (BUCK8_VIN), U1.49 (VSYS_LDO4IN), U1.56 (BUCK6_VIN), U1.57 (BUCK6_VIN), U1.62 (BUCK5_VIN), U1.63 (BUCK5_VIN)
