gralco/l5-schematic/CAD/PADS/librem5_mainboard/librem5_mainboard_kicad_conversion/librem5_mainboard_sheet10.kicad_sch

## KiCad design CAD/PADS/librem5_mainboard/librem5_mainboard_kicad_conversion/librem5_mainboard_sheet10.kicad_sch (2026-05-21)

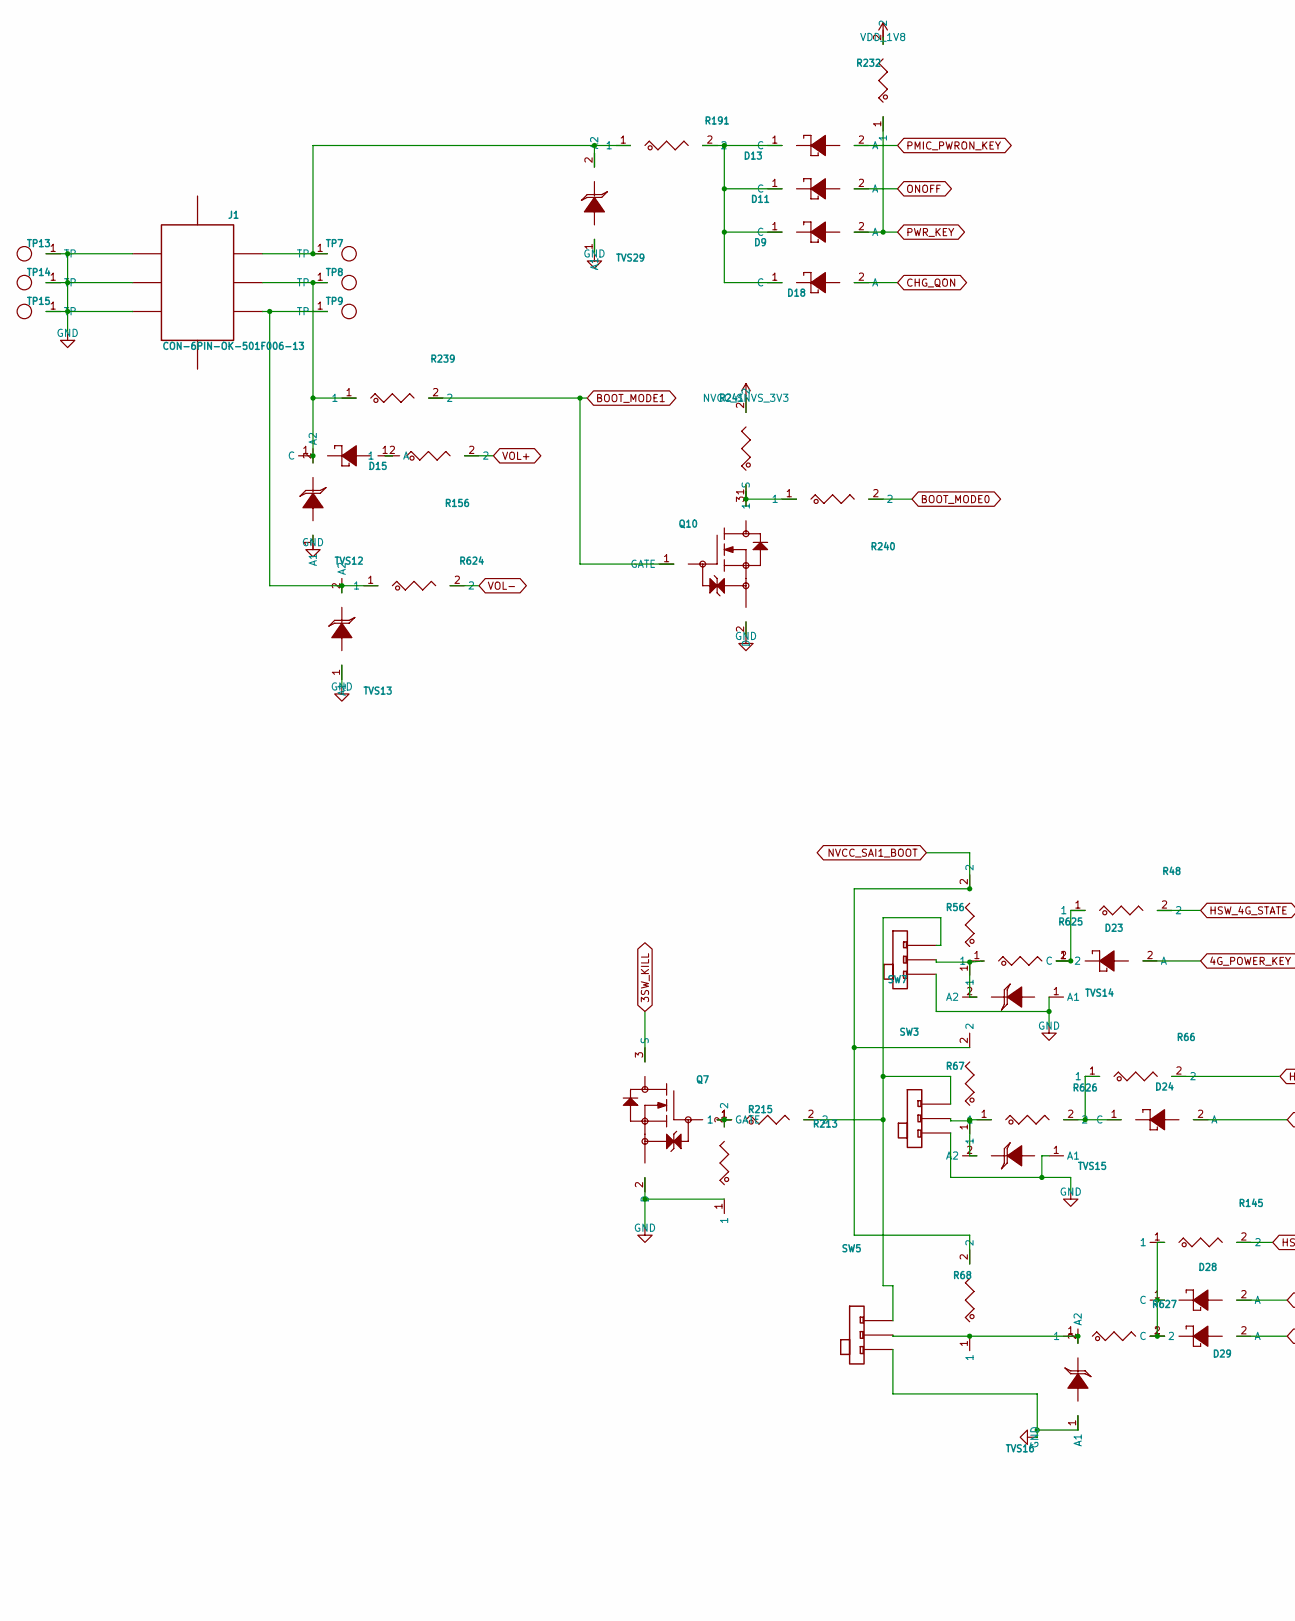
[picture p45: schematic librem5_mainboard_sheet10.kicad_sch, part in row 1, column 1]

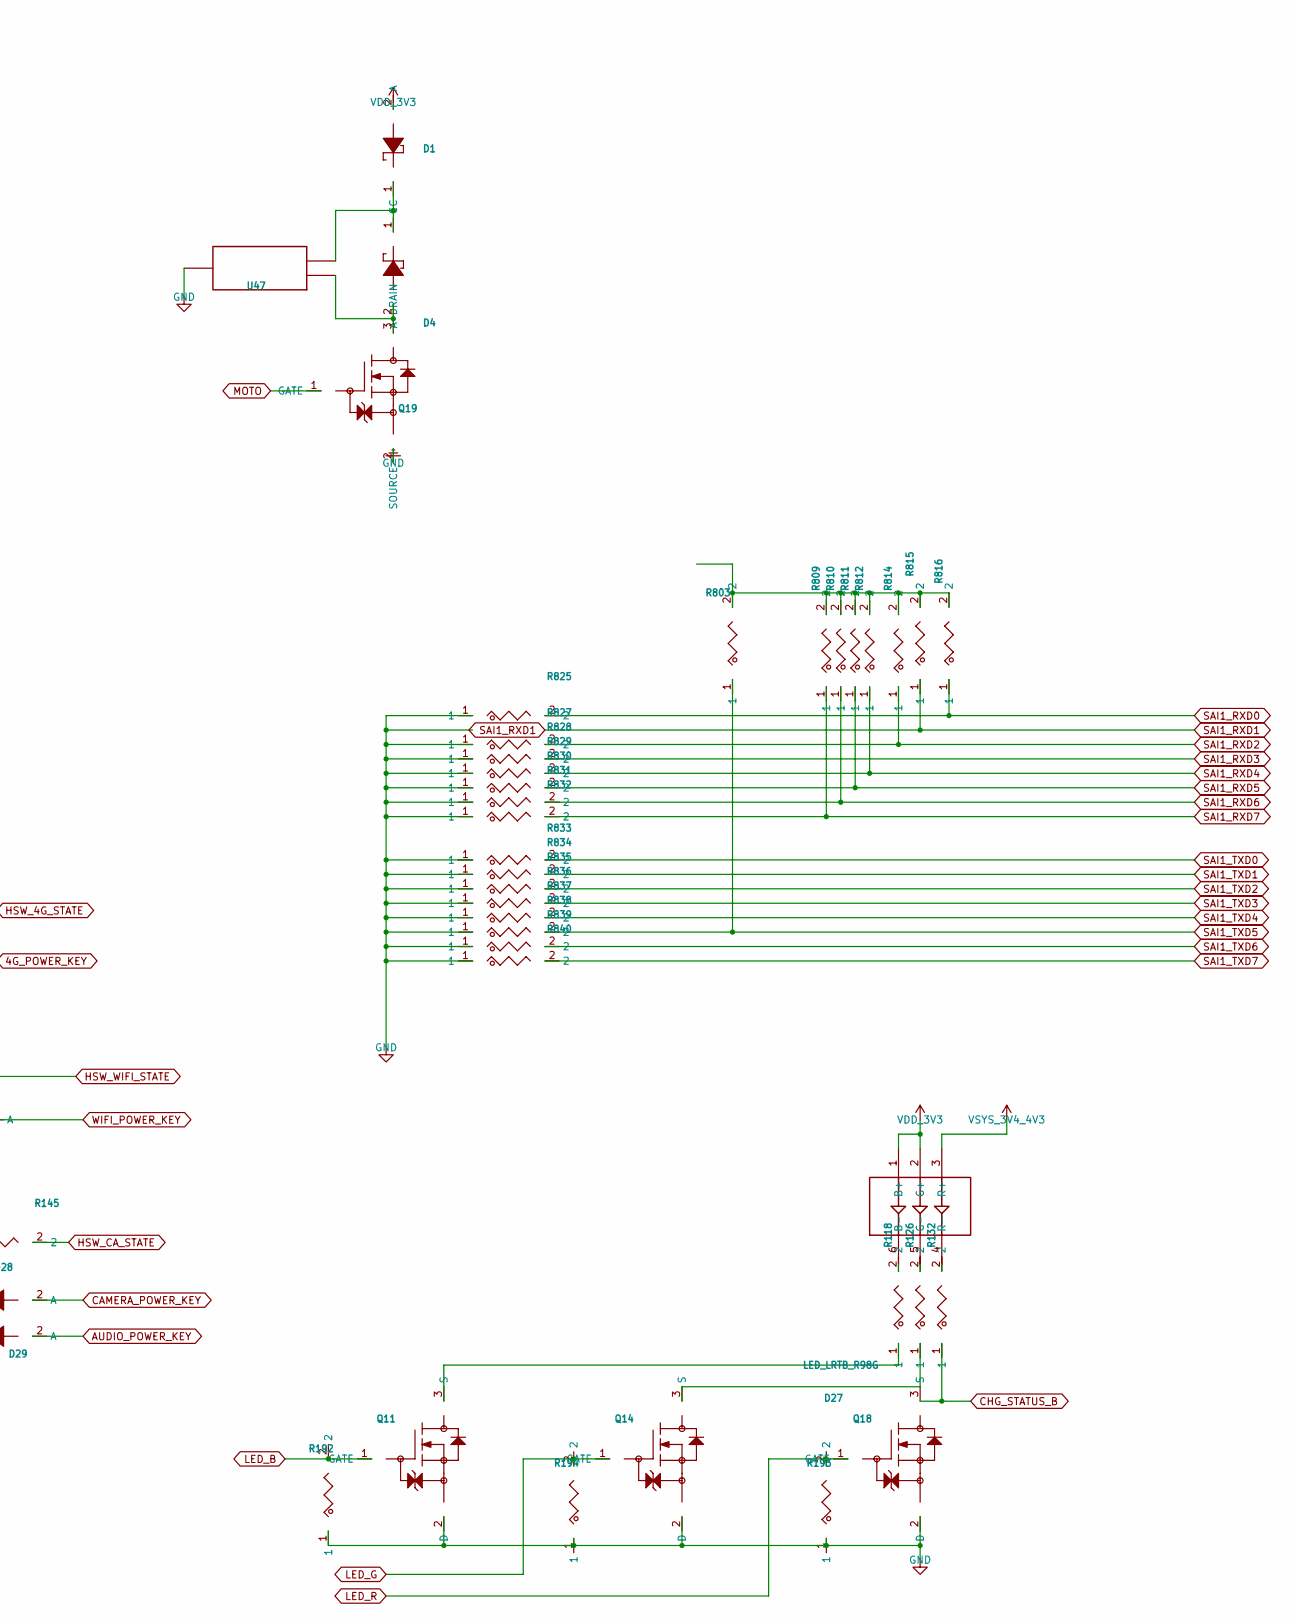
[picture p46: schematic librem5_mainboard_sheet10.kicad_sch, part in row 1, column 2]

Parts:
D1, D4: ZLLS400
D9, D11, D13, D15, D18, D23, D24, D28, D29: DIODE_SCHTKY_0
D27: LED_LRTB_R98G
J1: CON-6PIN-OK-501F006-13
Q7, Q10, Q11, Q14, Q18: 2SK3018
Q19: AP2302
R48, R56, R66, R67, R68, R118, R126, R132, R145, R156, R191, R192, R193, R194, R213, R215, R232, R239, R240, R241, R624, R625, R626, R627, R803, R809, R810, R811, R812, R814, R815, R816, R825, R827, R828, R829, R830, R831, R832, R833, R834, R835, R836, R837, R838, R839, R840: RES_2
SW3, SW5, SW7: HOLD-3P
TP7, TP8, TP9, TP13, TP14, TP15: T_POINT_R
TVS12, TVS13, TVS14, TVS15, TVS16, TVS29: TVS_0402_882
U47: SMD-MOTO

Connections:
3SW_KILL: Q7.3 (S)
4G_POWER_KEY: D23.2 (A)
AUDIO_POWER_KEY: D29.2 (A)
BOOT_MODE0: R240.2
BOOT_MODE1: Q10.1 (GATE), R239.2
CAMERA_POWER_KEY: D28.2 (A)
CHG_QON: D18.2 (A)
CHG_STATUS_B: Q18.3 (S), R132.1
GND: J1.1, J1.3, J1.5, Q7.2 (D), Q10.2 (D), Q11.2 (D), Q14.2 (D), Q18.2 (D), Q19.2 (SOURCE), R192.1, R193.1, R194.1, R215.1, R825.1, R827.1, R828.1, R829.1, R830.1, R831.1, R832.1, R833.1, R834.1, R835.1, R836.1, R837.1, R838.1, R839.1, R840.1, SW3.3, SW5.3, SW7.3, TP13.1, TP14.1, TP15.1, TVS12.1 (A1), TVS13.1 (A1), TVS14.1 (A1), TVS15.1 (A1), TVS16.1 (A1), TVS29.1 (A1), U47.3
HSW_4G_STATE: R48.2
HSW_CA_STATE: R145.2
HSW_WIFI_STATE: R66.2
LED_B: Q11.1 (GATE), R192.2
LED_G: Q14.1 (GATE), R194.2
LED_R: Q18.1 (GATE), R193.2
MOTO: Q19.1 (GATE)
NVCC_SAI1_BOOT: R56.2, R67.2, R68.2
NVCC_SNVS_3V3: R241.2
unnamed: D1.1 (C), D4.1 (C), U47.1
unnamed: D4.2 (A), Q19.3 (DRAIN), U47.2
unnamed: D9.1 (C), D11.1 (C), D13.1 (C), D18.1 (C), R191.2
unnamed: D15.1 (C), J1.4, R239.1, TP8.1, TVS12.2 (A2)
unnamed: D15.2 (A), R156.1
unnamed: D23.1 (C), R48.1, R625.2
unnamed: D24.1 (C), R66.1, R626.2
unnamed: D27.4 (R-), R132.2
unnamed: D27.5 (G-), R126.2
unnamed: D27.6 (B-), R118.2
unnamed: D28.1 (C), D29.1 (C), R145.1, R627.2
unnamed: J1.2, R624.1, TP9.1, TVS13.2 (A2)
unnamed: J1.6, R191.1, TP7.1, TVS29.2 (A2)
unnamed: Q7.1 (GATE), R213.1, R215.2
unnamed: Q10.3 (S), R240.1, R241.1
unnamed: Q11.3 (S), R118.1
unnamed: Q14.3 (S), R126.1
unnamed: R56.1, R625.1, SW7.2, TVS14.2 (A2)
unnamed: R213.2, SW3.1, SW5.1, SW7.1
unnamed: R67.1, R626.1, SW3.2, TVS15.2 (A2)
unnamed: R68.1, R627.1, SW5.2, TVS16.2 (A2)
unnamed: R803.2, R809.2, R810.2, R811.2, R812.2, R814.2, R815.2, R816.2
ONOFF: D11.2 (A)
PMIC_PWRON_KEY: D13.2 (A)
PWR_KEY: D9.2 (A), R232.1
SAI1_RXD0: R816.1, R825.2
SAI1_RXD1: R815.1
SAI1_RXD2: R814.1, R827.2
SAI1_RXD3: R828.2
SAI1_RXD4: R812.1, R829.2
SAI1_RXD5: R811.1, R830.2
SAI1_RXD6: R810.1, R831.2
SAI1_RXD7: R809.1, R832.2
SAI1_TXD0: R833.2
SAI1_TXD1: R834.2
SAI1_TXD2: R835.2
SAI1_TXD3: R836.2
SAI1_TXD4: R837.2
SAI1_TXD5: R803.1, R838.2
SAI1_TXD6: R839.2
SAI1_TXD7: R840.2
VDD_1V8: R232.2
VDD_3V3: D1.2 (A), D27.1 (B+), D27.2 (G+)
VOL+: R156.2
VOL-: R624.2
VSYS_3V4_4V3: D27.3 (R+)
WIFI_POWER_KEY: D24.2 (A)
