gralco/l5-schematic/CAD/PADS/librem5_mainboard/librem5_mainboard_kicad_conversion/librem5_mainboard_sheet11.kicad_sch

## KiCad design CAD/PADS/librem5_mainboard/librem5_mainboard_kicad_conversion/librem5_mainboard_sheet11.kicad_sch (2026-05-21)

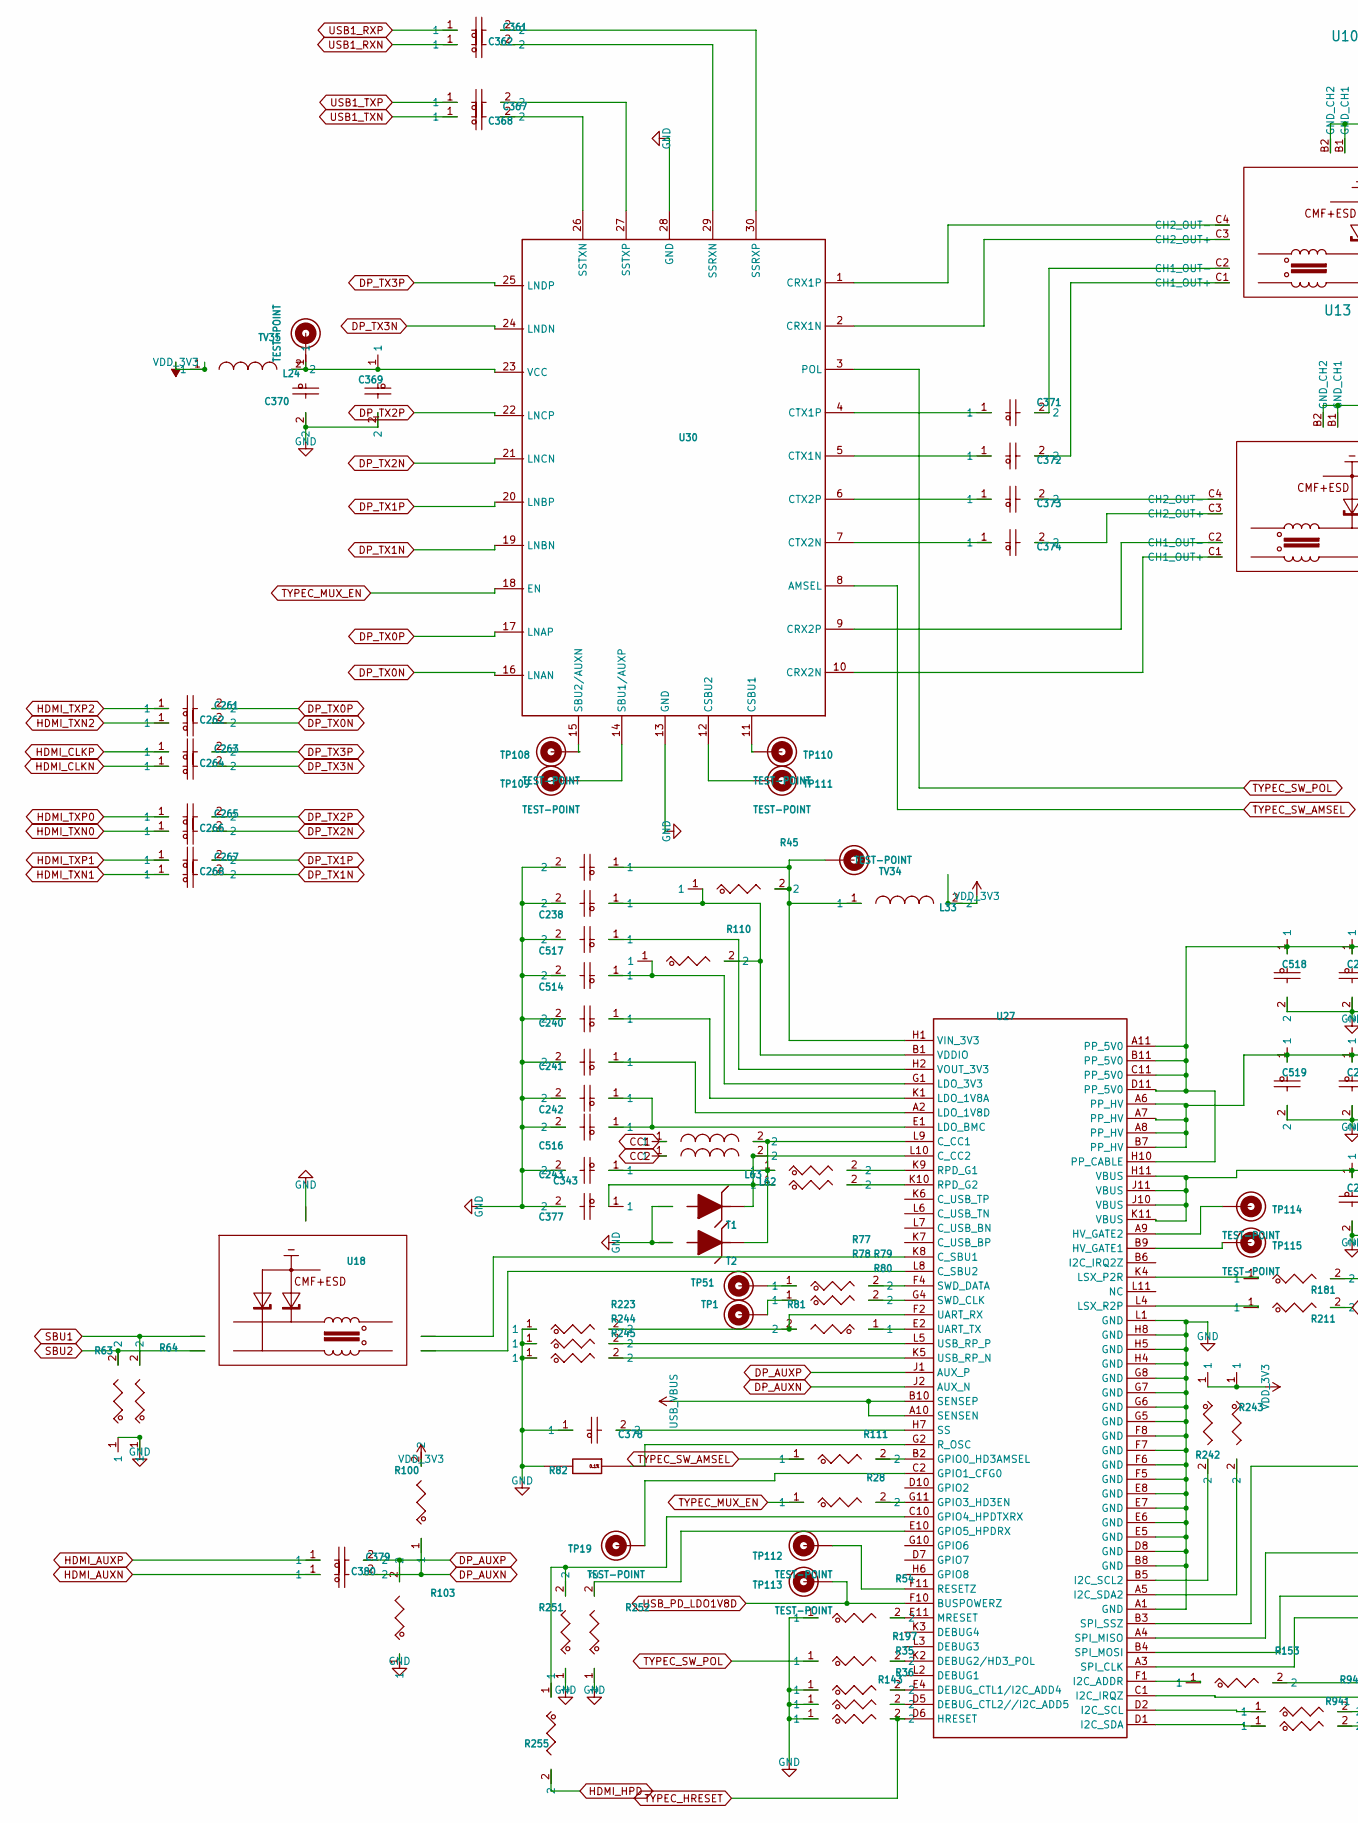
[picture p47: schematic librem5_mainboard_sheet11.kicad_sch, part in row 1, column 1]

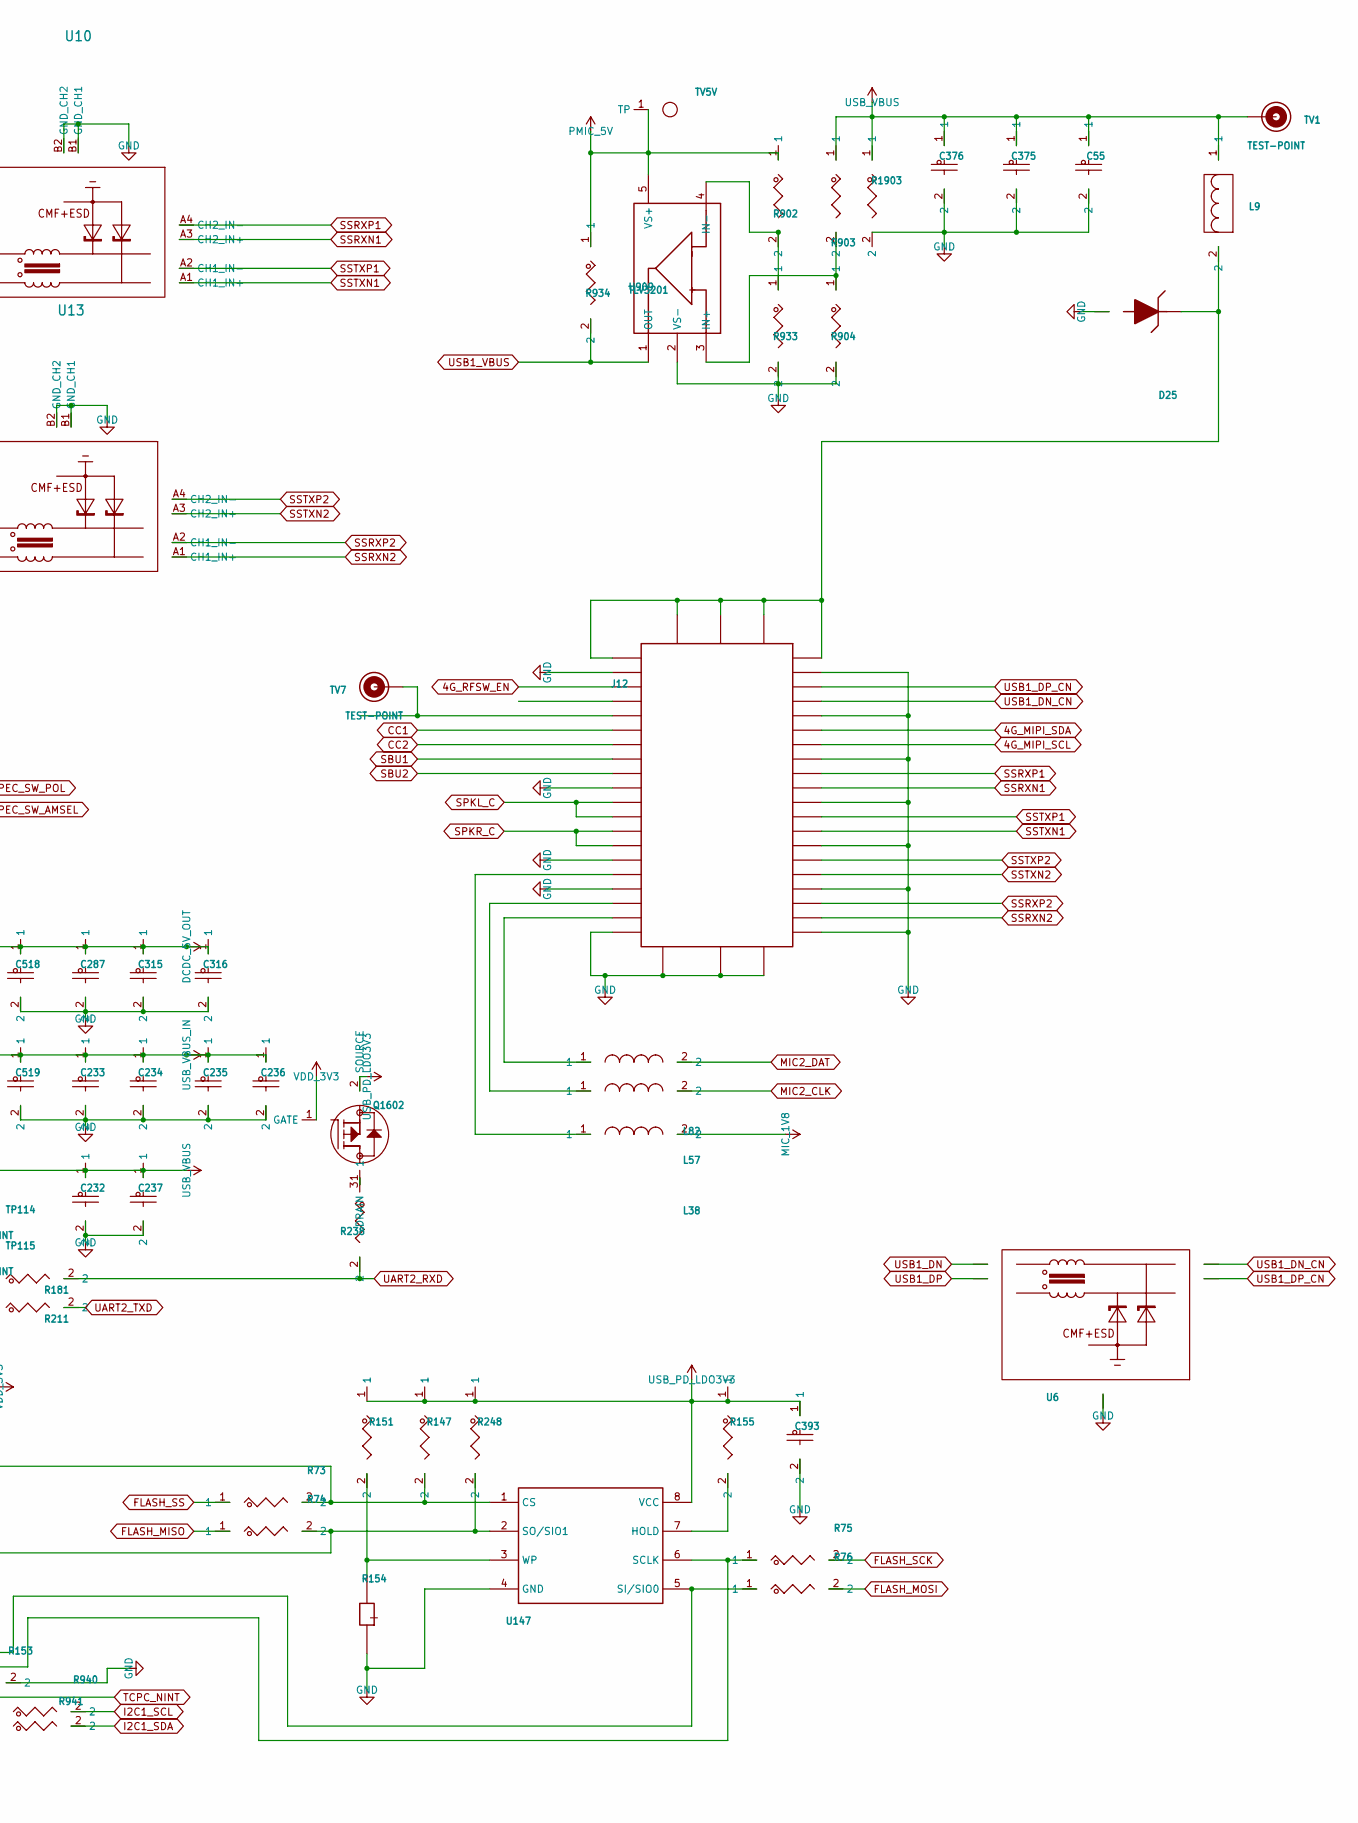
[picture p48: schematic librem5_mainboard_sheet11.kicad_sch, part in row 1, column 2]

Parts:
C55, C232, C233, C234, C287, C518, C519: C0603; VOLTAGE 35V
C235, C237, C315, C375, C376, C378: C0402; VOLTAGE 35V
C236, C316: C0201; VOLTAGE 35V
C238, C241, C242: C0402; VOLTAGE 6.3V
C240: C0603; VOLTAGE 6.3V
C243, C369, C370, C371, C372, C373, C374, C379, C380, C393, C514, C516, C517: C0201; VOLTAGE 6.3V
C261, C262, C263, C264, C265, C266, C267, C268, C361, C362, C367, C368: C0201
C343, C377: C0201; VOLTAGE 25V
D25: NSR20F30NXT5G
J12: BTB40-0.35-KYOCERA5857
L9: BEAD-4030
L24, L33, L38, L57, L62, L63, L82: BEAD-0402
Q1602: MOSFET_P
R28, R35, R36, R45, R54, R63, R64, R73, R74, R75, R76, R77, R78, R79, R80, R81, R100, R103, R110, R111, R143, R147, R151, R153, R155, R181, R197, R211, R223, R238, R242, R243, R244, R245, R248, R251, R252, R255, R902, R903, R904, R933, R934, R940, R941, R1903: RES_2
R82: R_0.1%
R154: CURRENT_R
T1, T2: TPD1E05U06
TP1, TP19, TP51, TP108, TP109, TP110, TP111, TP112, TP113, TP114, TP115: TEST-POINT
TV1, TV7, TV34, TV35: TEST-POINT
TV5V: T_POINT_R
U6, U18: PCMF1USB3S_5P
U10, U13: PCMF2USB3S_10P
U27: TPS65983B
U30: HD3SS460
U147: MX25L1606E
U909: TLV3201

Connections:
4G_MIPI_SCL: J12.14
4G_MIPI_SDA: J12.15
4G_RFSW_EN: J12.23
CC1: J12.26, L62.1
CC2: J12.27, L63.1
DCDC_5V_OUT: C287.1, C315.1, C316.1, C518.1, U27.A11 (PP_5V0), U27.B11 (PP_5V0), U27.C11 (PP_5V0), U27.D11 (PP_5V0), U27.H10 (PP_CABLE)
DP_AUXN: C380.2, R100.1, U27.J2 (AUX_N)
DP_AUXP: C379.2, R103.2, U27.J1 (AUX_P)
DP_TX0N: C262.2, U30.16 (LNAN)
DP_TX0P: C261.2, U30.17 (LNAP)
DP_TX1N: C268.2, U30.19 (LNBN)
DP_TX1P: C267.2, U30.20 (LNBP)
DP_TX2N: C266.2, U30.21 (LNCN)
DP_TX2P: C265.2, U30.22 (LNCP)
DP_TX3N: C264.2, U30.24 (LNDN)
DP_TX3P: C263.2, U30.25 (LNDP)
FLASH_MISO: R74.1
FLASH_MOSI: R76.2
FLASH_SCK: R75.2
FLASH_SS: R73.1
GND: C55.2, C232.2, C233.2, C234.2, C235.2, C236.2, C237.2, C238.2, C240.2, C241.2, C242.2, C243.2, C287.2, C315.2, C316.2, C343.2, C369.2, C370.2, C375.2, C376.2, C377.2, C378.1, C393.2, C514.2, C516.2, C517.2, C518.2, C519.2, D25.2, J12.1, J12.4, J12.7, J12.10, J12.13, J12.16, J12.19, J12.22, J12.30, J12.35, J12.37, J12.40, J12.41, J12.42, J12.43, R35.1, R36.1, R54.1, R63.1, R64.1, R82.2, R103.1, R143.1, R153.2, R154.1, R223.1, R244.1, R245.1, R251.1, R252.1, R904.2, R933.2, R1903.2, T1.2, T2.2, U6.3, U10.B1 (GND_CH1), U10.B2 (GND_CH2), U13.B1 (GND_CH1), U13.B2 (GND_CH2), U18.3, U27.A1 (GND), U27.B8 (GND), U27.D8 (GND), U27.E5 (GND), U27.E6 (GND), U27.E7 (GND), U27.E8 (GND), U27.F5 (GND), U27.F6 (GND), U27.F7 (GND), U27.F8 (GND), U27.G5 (GND), U27.G6 (GND), U27.G7 (GND), U27.G8 (GND), U27.H4 (GND), U27.H5 (GND), U27.H8 (GND), U27.L1 (GND), U30.13 (GND), U30.28 (GND), U147.4 (GND), U909.2 (VS-)
HDMI_AUXN: C380.1
HDMI_AUXP: C379.1
HDMI_CLKN: C264.1
HDMI_CLKP: C263.1
HDMI_HPD: R255.2
HDMI_TXN0: C266.1
HDMI_TXN1: C268.1
HDMI_TXN2: C262.1
HDMI_TXP0: C265.1
HDMI_TXP1: C267.1
HDMI_TXP2: C261.1
I2C1_SCL: R940.2
I2C1_SDA: R941.2
MIC2_CLK: L57.2
MIC2_DAT: L82.2
MIC_1V8: L38.2
unnamed: C238.1, L33.1, R45.2, TV34.1, U27.H1 (VIN_3V3)
unnamed: C240.1, R110.1, U27.G1 (LDO_3V3)
unnamed: C241.1, U27.K1 (LDO_1V8A)
unnamed: C242.1, U27.A2 (LDO_1V8D)
unnamed: C243.1, C516.1, U27.E1 (LDO_BMC)
unnamed: C343.1, L62.2, R77.1, T2.1, U27.L9 (C_CC1)
unnamed: C361.2, U30.30 (SSRXP)
unnamed: C362.2, U30.29 (SSRXN)
unnamed: C367.2, U30.27 (SSTXP)
unnamed: C368.2, U30.26 (SSTXN)
unnamed: C369.1, C370.1, L24.2, TV35.1, U30.23 (VCC)
unnamed: C371.1, U30.4 (CTX1P)
unnamed: C371.2, U10.C2 (CH1_OUT-)
unnamed: C372.1, U30.5 (CTX1N)
unnamed: C372.2, U10.C1 (CH1_OUT+)
unnamed: C373.1, U30.6 (CTX2P)
unnamed: C373.2, U13.C4 (CH2_OUT-)
unnamed: C374.1, U30.7 (CTX2N)
unnamed: C374.2, U13.C3 (CH2_OUT+)
unnamed: C377.1, L63.2, R78.1, T1.1, U27.L10 (C_CC2)
unnamed: C378.2, U27.H7 (SS)
unnamed: C514.1, U27.H2 (VOUT_3V3)
unnamed: C517.1, R45.1, R110.2, U27.B1 (VDDIO)
unnamed: D25.1, J12.20, J12.21, J12.44, J12.45, J12.46, L9.2
unnamed: J12.25, TV7.1
unnamed: J12.36, L38.1
unnamed: J12.38, L57.1
unnamed: J12.39, L82.1
unnamed: Q1602.3 (DRAIN), R238.1
unnamed: R28.2, U27.G11 (GPIO3_HD3EN)
unnamed: R35.2, U27.E4 (DEBUG_CTL1/I2C_ADD4)
unnamed: R36.2, U27.D5 (DEBUG_CTL2//I2C_ADD5)
unnamed: R54.2, U27.E11 (MRESET)
unnamed: R75.1, U27.A3 (SPI_CLK), U147.6 (SCLK)
unnamed: R76.1, U27.B4 (SPI_MOSI), U147.5 (SI/SIO0)
unnamed: R77.2, U27.K9 (RPD_G1)
unnamed: R78.2, U27.K10 (RPD_G2)
unnamed: R79.1, TP51.1
unnamed: R79.2, U27.F4 (SWD_DATA)
unnamed: R80.1, TP1.1
unnamed: R80.2, U27.G4 (SWD_CLK)
unnamed: R81.1, U27.E2 (UART_TX)
unnamed: R82.1, U27.G2 (R_OSC)
unnamed: R111.2, U27.B2 (GPIO0_HD3AMSEL)
unnamed: R73.2, R147.2, U27.B3 (SPI_SSZ), U147.1 (CS)
unnamed: R151.2, R154.2, U147.3 (WP)
unnamed: R153.1, U27.F1 (I2C_ADDR)
unnamed: R155.2, U147.7 (HOLD)
unnamed: R181.1, U27.K4 (LSX_P2R)
unnamed: R197.2, U27.K2 (DEBUG2/HD3_POL)
unnamed: R211.1, U27.L4 (LSX_R2P)
unnamed: R81.2, R223.2, U27.F2 (UART_RX)
unnamed: R242.2, U27.B5 (I2C_SCL2)
unnamed: R243.2, U27.A5 (I2C_SDA2)
unnamed: R244.2, U27.L5 (USB_RP_P)
unnamed: R245.2, U27.K5 (USB_RP_N)
unnamed: R74.2, R248.2, U27.A4 (SPI_MISO), U147.2 (SO/SIO1)
unnamed: R251.2, R255.1, U27.C10 (GPIO4_HPDTXRX)
unnamed: R252.2, U27.E10 (GPIO5_HPDRX)
unnamed: R902.2, R933.1, U909.4 (IN-)
unnamed: R903.2, R904.1, U909.3 (IN+)
unnamed: R940.1, U27.D2 (I2C_SCL)
unnamed: R941.1, U27.D1 (I2C_SDA)
unnamed: TP19.1, U27.C2 (GPIO1_CFG0)
unnamed: TP108.1, U30.15 (SBU2/AUXN)
unnamed: TP109.1, U30.14 (SBU1/AUXP)
unnamed: TP110.1, U30.11 (CSBU1)
unnamed: TP111.1, U30.12 (CSBU2)
unnamed: TP112.1, U27.F11 (RESETZ)
unnamed: TP114.1, U27.A9 (HV_GATE2)
unnamed: TP115.1, U27.B9 (HV_GATE1)
unnamed: U10.C3 (CH2_OUT+), U30.2 (CRX1N)
unnamed: U10.C4 (CH2_OUT-), U30.1 (CRX1P)
unnamed: U13.C1 (CH1_OUT+), U30.10 (CRX2N)
unnamed: U13.C2 (CH1_OUT-), U30.9 (CRX2P)
unnamed: U18.4, U27.L8 (C_SBU2)
unnamed: U18.5, U27.K8 (C_SBU1)
PMIC_5V: R902.1, R934.1, TV5V.1, U909.5 (VS+)
SBU1: J12.28, R64.2, U18.2
SBU2: J12.29, R63.2, U18.1
SPKL_C: J12.31, J12.32
SPKR_C: J12.33, J12.34
SSRXN1: J12.11, U10.A3 (CH2_IN+)
SSRXN2: J12.2, U13.A1 (CH1_IN+)
SSRXP1: J12.12, U10.A4 (CH2_IN-)
SSRXP2: J12.3, U13.A2 (CH1_IN-)
SSTXN1: J12.8, U10.A1 (CH1_IN+)
SSTXN2: J12.5, U13.A3 (CH2_IN+)
SSTXP1: J12.9, U10.A2 (CH1_IN-)
SSTXP2: J12.6, U13.A4 (CH2_IN-)
TCPC_NINT: U27.C1 (I2C_IRQZ)
TYPEC_HRESET: R143.2, U27.D6 (HRESET)
TYPEC_MUX_EN: R28.1, U30.18 (EN)
TYPEC_SW_AMSEL: R111.1, U30.8 (AMSEL)
TYPEC_SW_POL: R197.1, U30.3 (POL)
UART2_RXD: R181.2, R238.2
UART2_TXD: R211.2
USB1_DN: U6.4
USB1_DN_CN: J12.17, U6.1
USB1_DP: U6.5
USB1_DP_CN: J12.18, U6.2
USB1_RXN: C362.1
USB1_RXP: C361.1
USB1_TXN: C368.1
USB1_TXP: C367.1
USB1_VBUS: R934.2, U909.1 (OUT)
USB_PD_LDO1V8D: TP113.1, U27.F10 (BUSPOWERZ)
USB_PD_LDO3V3: C393.1, Q1602.2 (SOURCE), R147.1, R151.1, R155.1, R248.1, U147.8 (VCC)
USB_VBUS: C55.1, C232.1, C237.1, C375.1, C376.1, L9.1, R903.1, R1903.1, TV1.1, U27.A10 (SENSEN), U27.B10 (SENSEP), U27.H11 (VBUS), U27.J10 (VBUS), U27.J11 (VBUS), U27.K11 (VBUS)
USB_VBUS_IN: C233.1, C234.1, C235.1, C236.1, C519.1, U27.A6 (PP_HV), U27.A7 (PP_HV), U27.A8 (PP_HV), U27.B7 (PP_HV)
VDD_3V3: L24.1, L33.2, Q1602.1 (GATE), R100.2, R242.1, R243.1
