gralco/l5-schematic/CAD/PADS/librem5_mainboard/librem5_mainboard_kicad_conversion/librem5_mainboard_sheet12.kicad_sch

## KiCad design CAD/PADS/librem5_mainboard/librem5_mainboard_kicad_conversion/librem5_mainboard_sheet12.kicad_sch (2026-05-21)

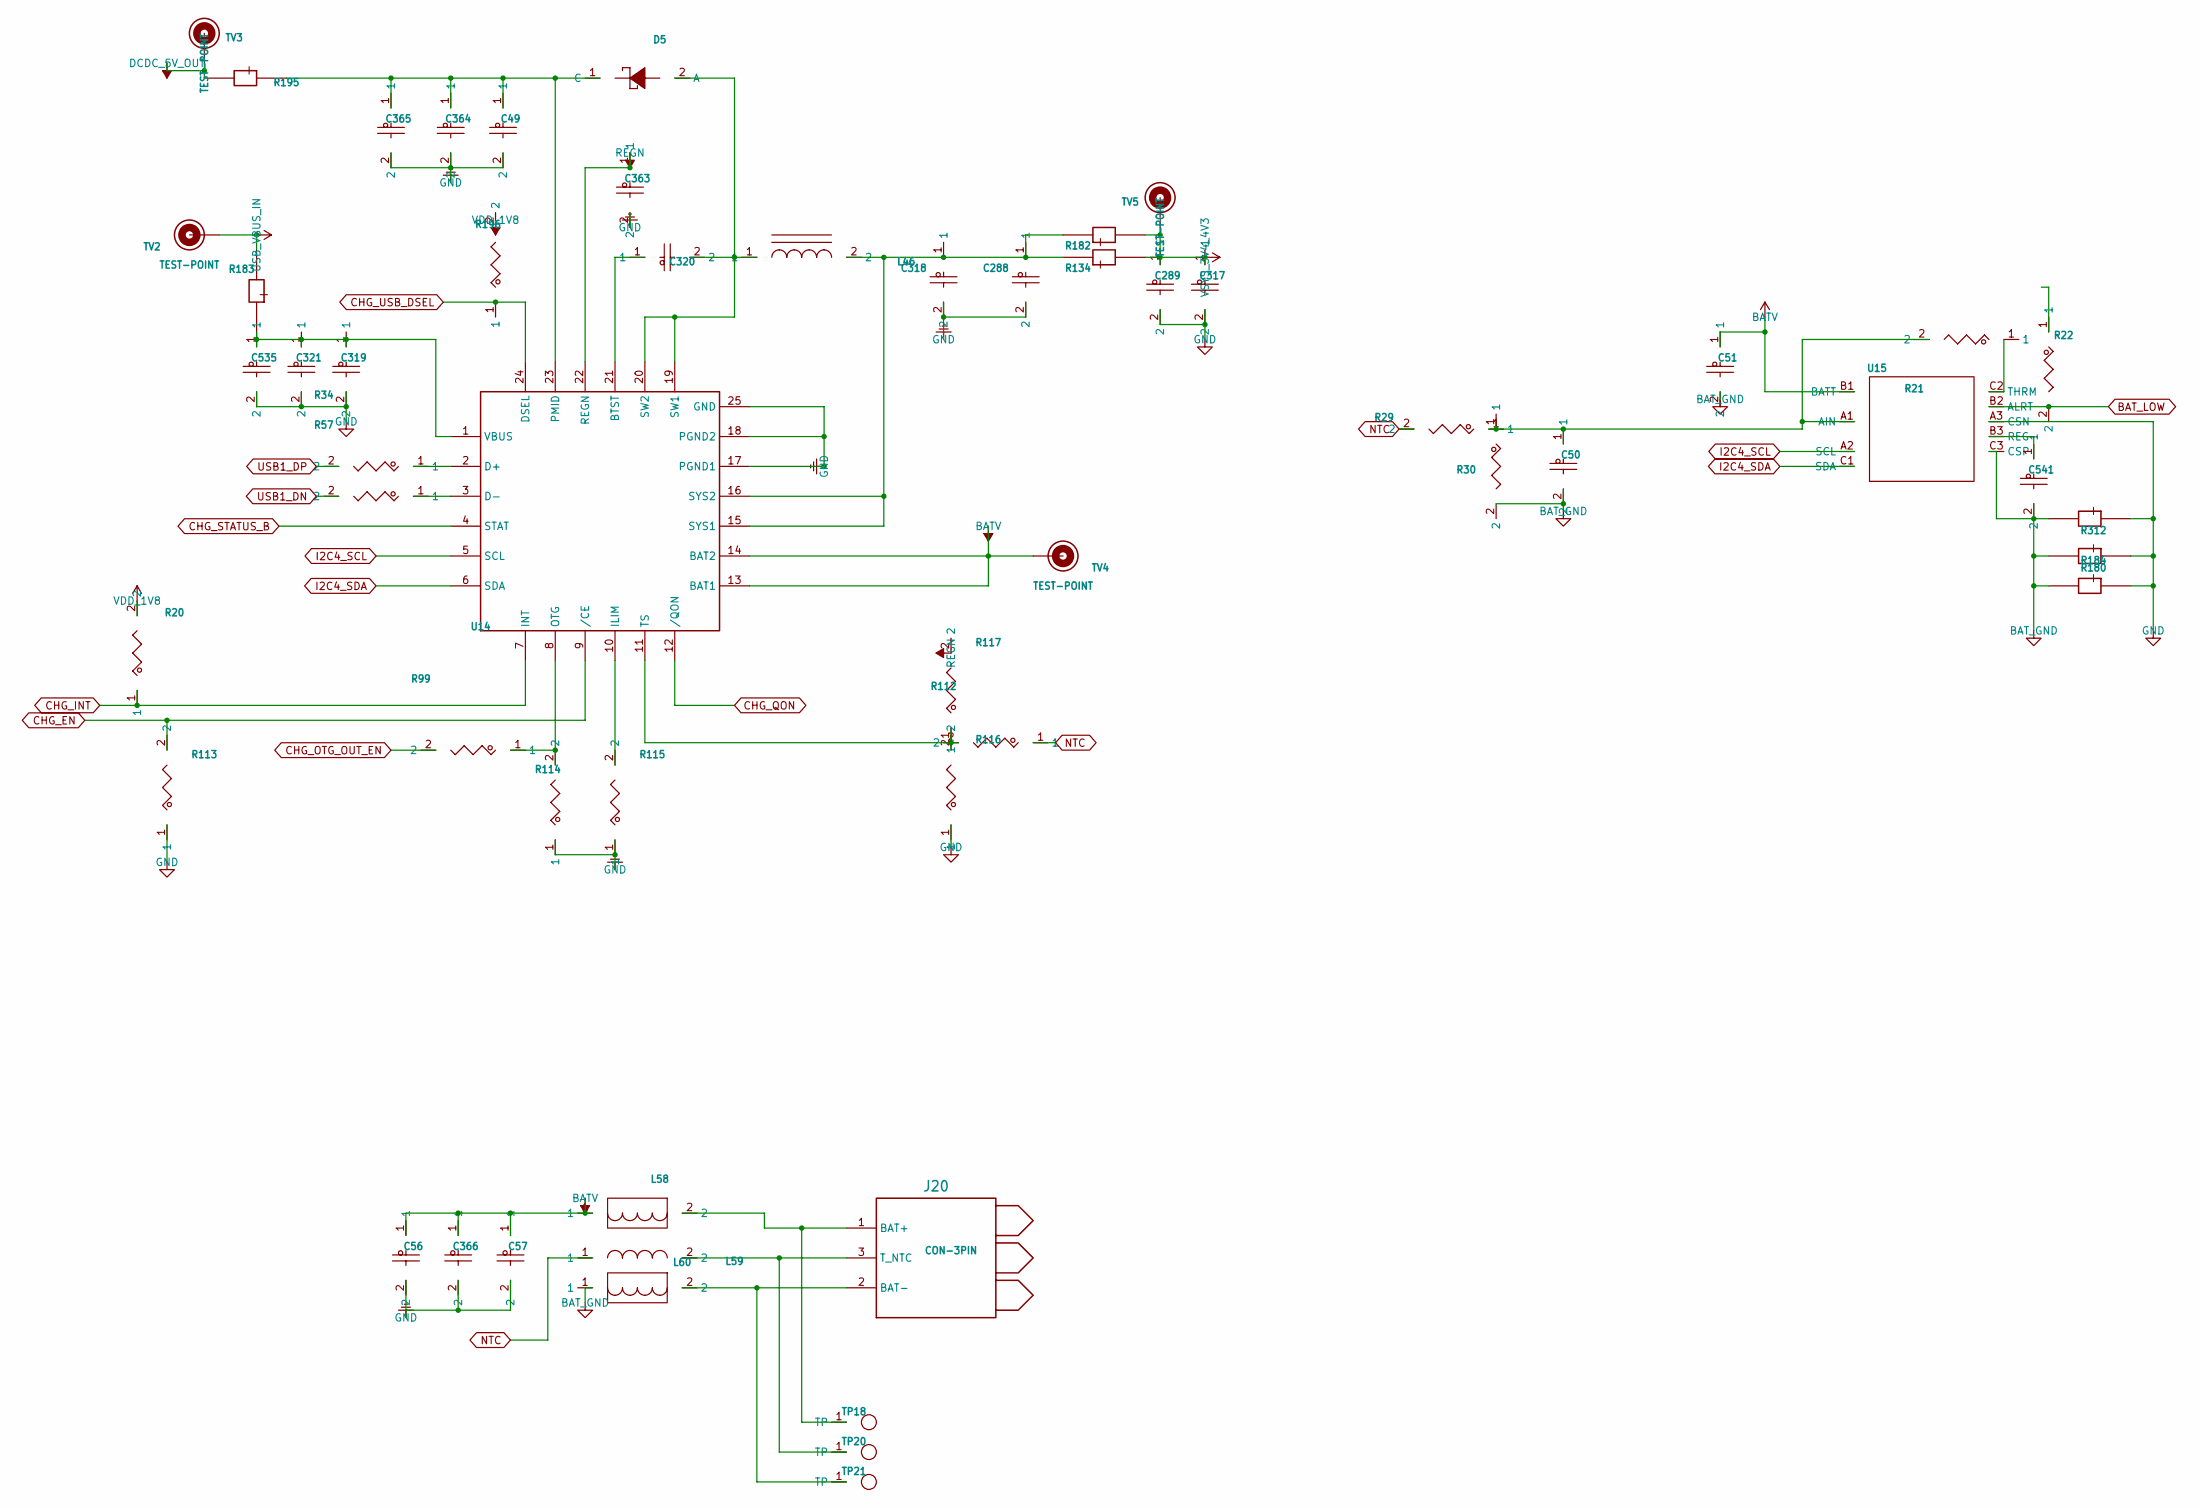
[picture p49: schematic librem5_mainboard_sheet12.kicad_sch]

Parts:
C49, C319, C363, C364: C0603; VOLTAGE 35V
C50: C0201
C51, C57, C317, C318, C366, C541: C0201; VOLTAGE 6.3V
C56, C288, C289: C0603; VOLTAGE 6.3V
C320, C321, C365, C535: C0402; VOLTAGE 35V
D5: ZLLS400
J20: CON-3PIN
L46: INDUCTOR_IRON_1
L58, L59: BEAD-4030
L60: BEAD-0402
R20, R21, R22, R29, R30, R34, R57, R99, R112, R113, R114, R115, R116, R117, R196: RES_2
R134, R180, R182, R183, R184, R195, R312: CURRENT_R
TP18, TP20, TP21: T_POINT_R
TV2, TV3, TV4, TV5: TEST-POINT
U14: BQ25895-25
U15: MAX17047_0

Connections:
BATV: C51.1, C56.1, C57.1, C366.1, L58.1, TV4.1, U14.13 (BAT1), U14.14 (BAT2), U15.B1 (BATT)
BAT_GND: C50.2, C51.2, C541.2, L59.1, R30.2, R180.2, R184.2, R312.2, U15.C3 (CSP)
BAT_LOW: R22.2, U15.B2 (ALRT)
CHG_EN: R113.2, U14.9 (/CE)
CHG_INT: R20.1, U14.7 (INT)
CHG_OTG_OUT_EN: R99.2
CHG_QON: U14.12 (/QON)
CHG_STATUS_B: U14.4 (STAT)
CHG_USB_DSEL: R196.1, U14.24 (DSEL)
DCDC_5V_OUT: R195.2, TV3.1
GND: C49.2, C56.2, C57.2, C288.2, C289.2, C317.2, C318.2, C319.2, C321.2, C363.2, C364.2, C365.2, C366.2, C535.2, R113.1, R114.1, R115.1, R116.1, R180.1, R184.1, R312.1, U14.17 (PGND1), U14.18 (PGND2), U14.25 (GND), U15.A3 (CSN)
I2C4_SCL: U14.5 (SCL), U15.A2 (SCL)
I2C4_SDA: U14.6 (SDA), U15.C1 (SDA)
NTC: L60.1, R29.2, R112.1
unnamed: C50.1, R21.2, R29.1, R30.1, U15.A1 (AIN)
unnamed: C288.1, C318.1, L46.2, R134.1, R182.1, U14.15 (SYS1), U14.16 (SYS2)
unnamed: C319.1, C321.1, C535.1, R183.1, U14.1 (VBUS)
unnamed: C320.1, U14.21 (BTST)
unnamed: C320.2, D5.2 (A), L46.1, U14.19 (SW1), U14.20 (SW2)
unnamed: C49.1, C364.1, C365.1, D5.1 (C), R195.1, U14.23 (PMID)
unnamed: C541.1, U15.B3 (REG)
unnamed: J20.1 (BAT+), L58.2, TP18.1
unnamed: J20.2 (BAT-), L59.2, TP21.1
unnamed: J20.3 (T_NTC), L60.2, TP20.1
unnamed: R21.1, U15.C2 (THRM)
unnamed: R34.1, U14.2 (D+)
unnamed: R57.1, U14.3 (D-)
unnamed: R112.2, R116.2, R117.1, U14.11 (TS)
unnamed: R99.1, R114.2, U14.8 (OTG)
unnamed: R115.2, U14.10 (ILIM)
REGN: C363.1, R117.2, U14.22 (REGN)
USB1_DN: R57.2
USB1_DP: R34.2
USB_VBUS_IN: R183.2, TV2.1
VDD_1V8: R20.2, R196.2
VSYS_3V4_4V3: C289.1, C317.1, R134.2, R182.2, TV5.1
