gralco/l5-schematic/CAD/PADS/librem5_mainboard/librem5_mainboard_kicad_conversion/librem5_mainboard_sheet13.kicad_sch

## KiCad design CAD/PADS/librem5_mainboard/librem5_mainboard_kicad_conversion/librem5_mainboard_sheet13.kicad_sch (2026-05-21)

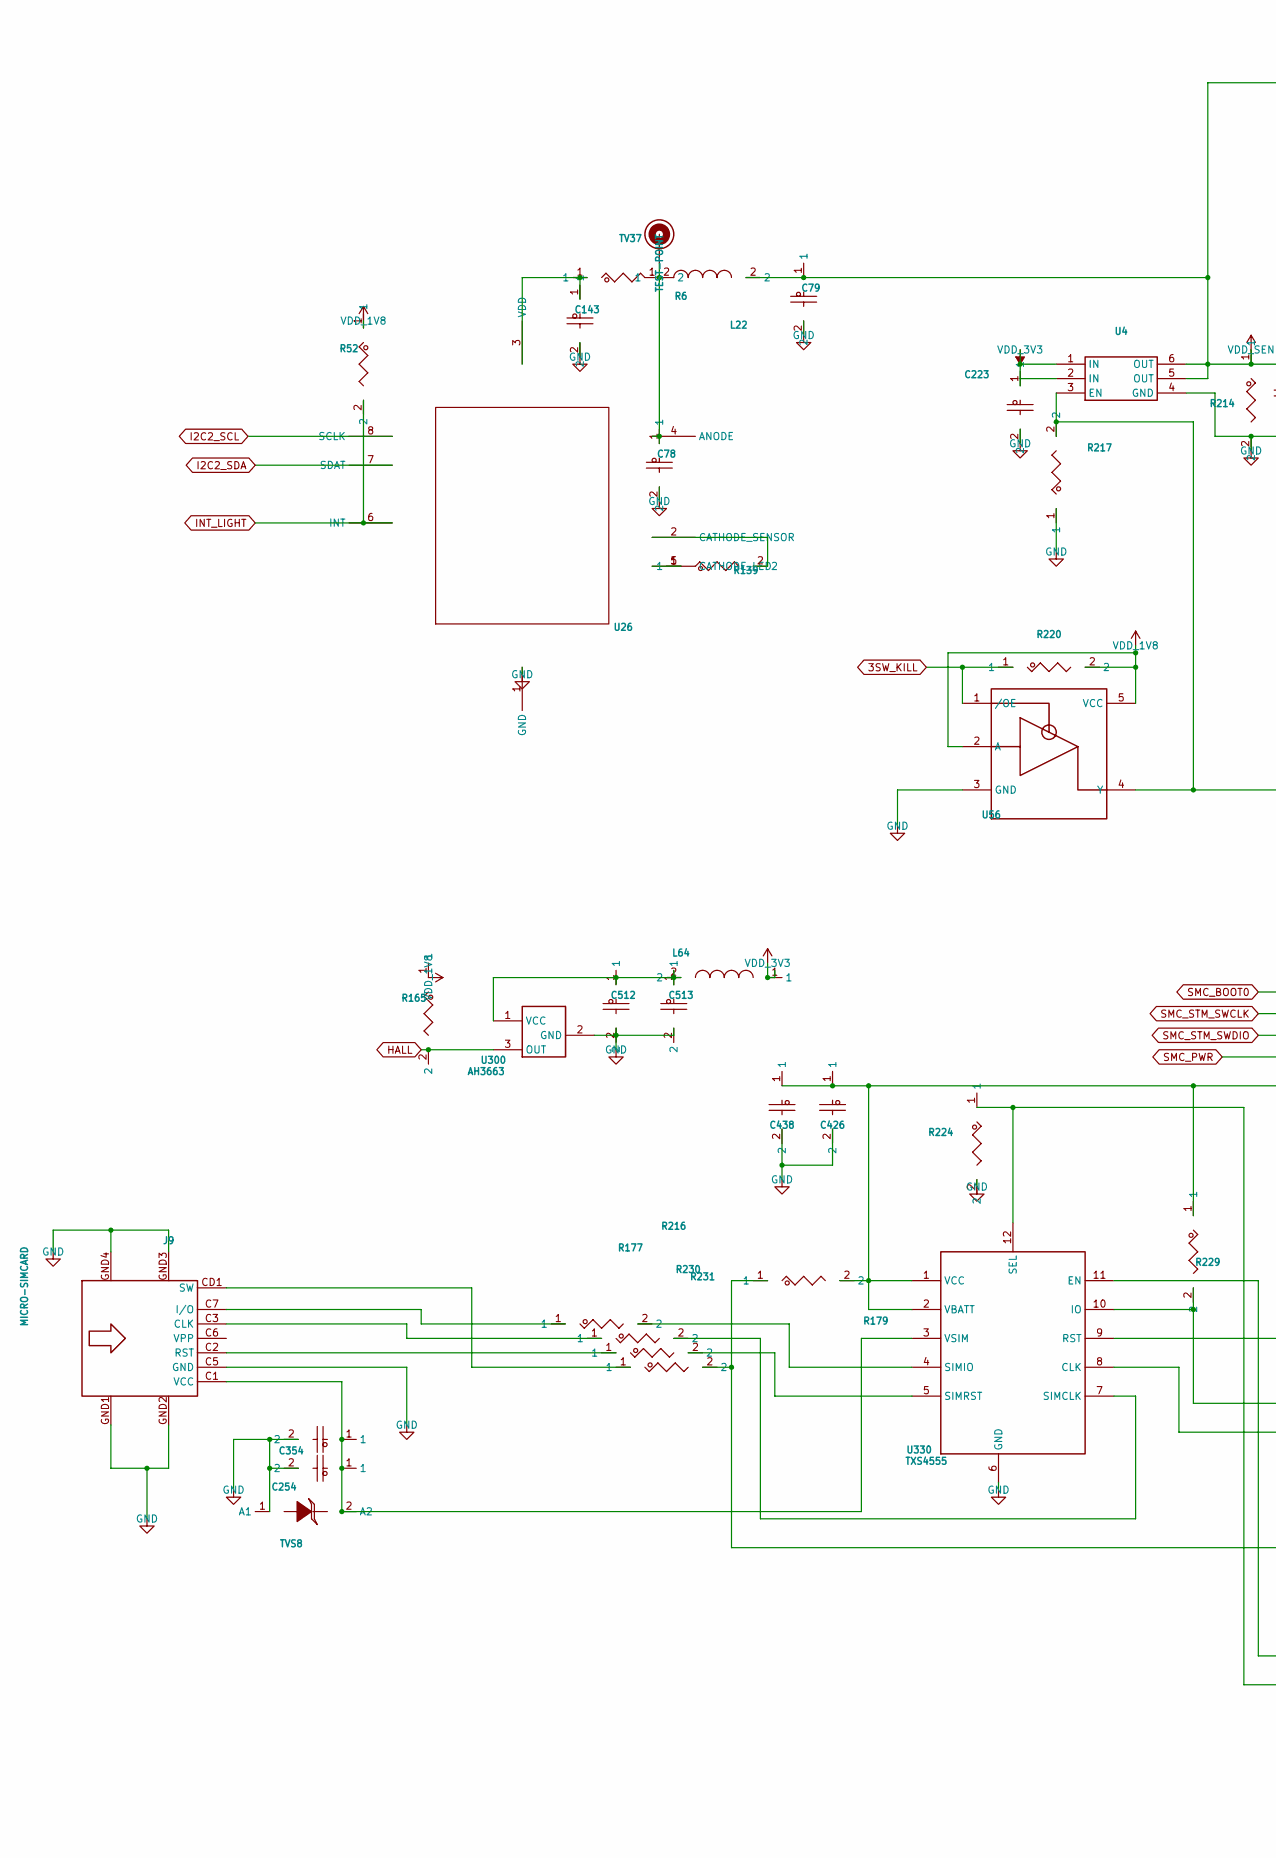
[picture p50: schematic librem5_mainboard_sheet13.kicad_sch, part in row 1, column 1]

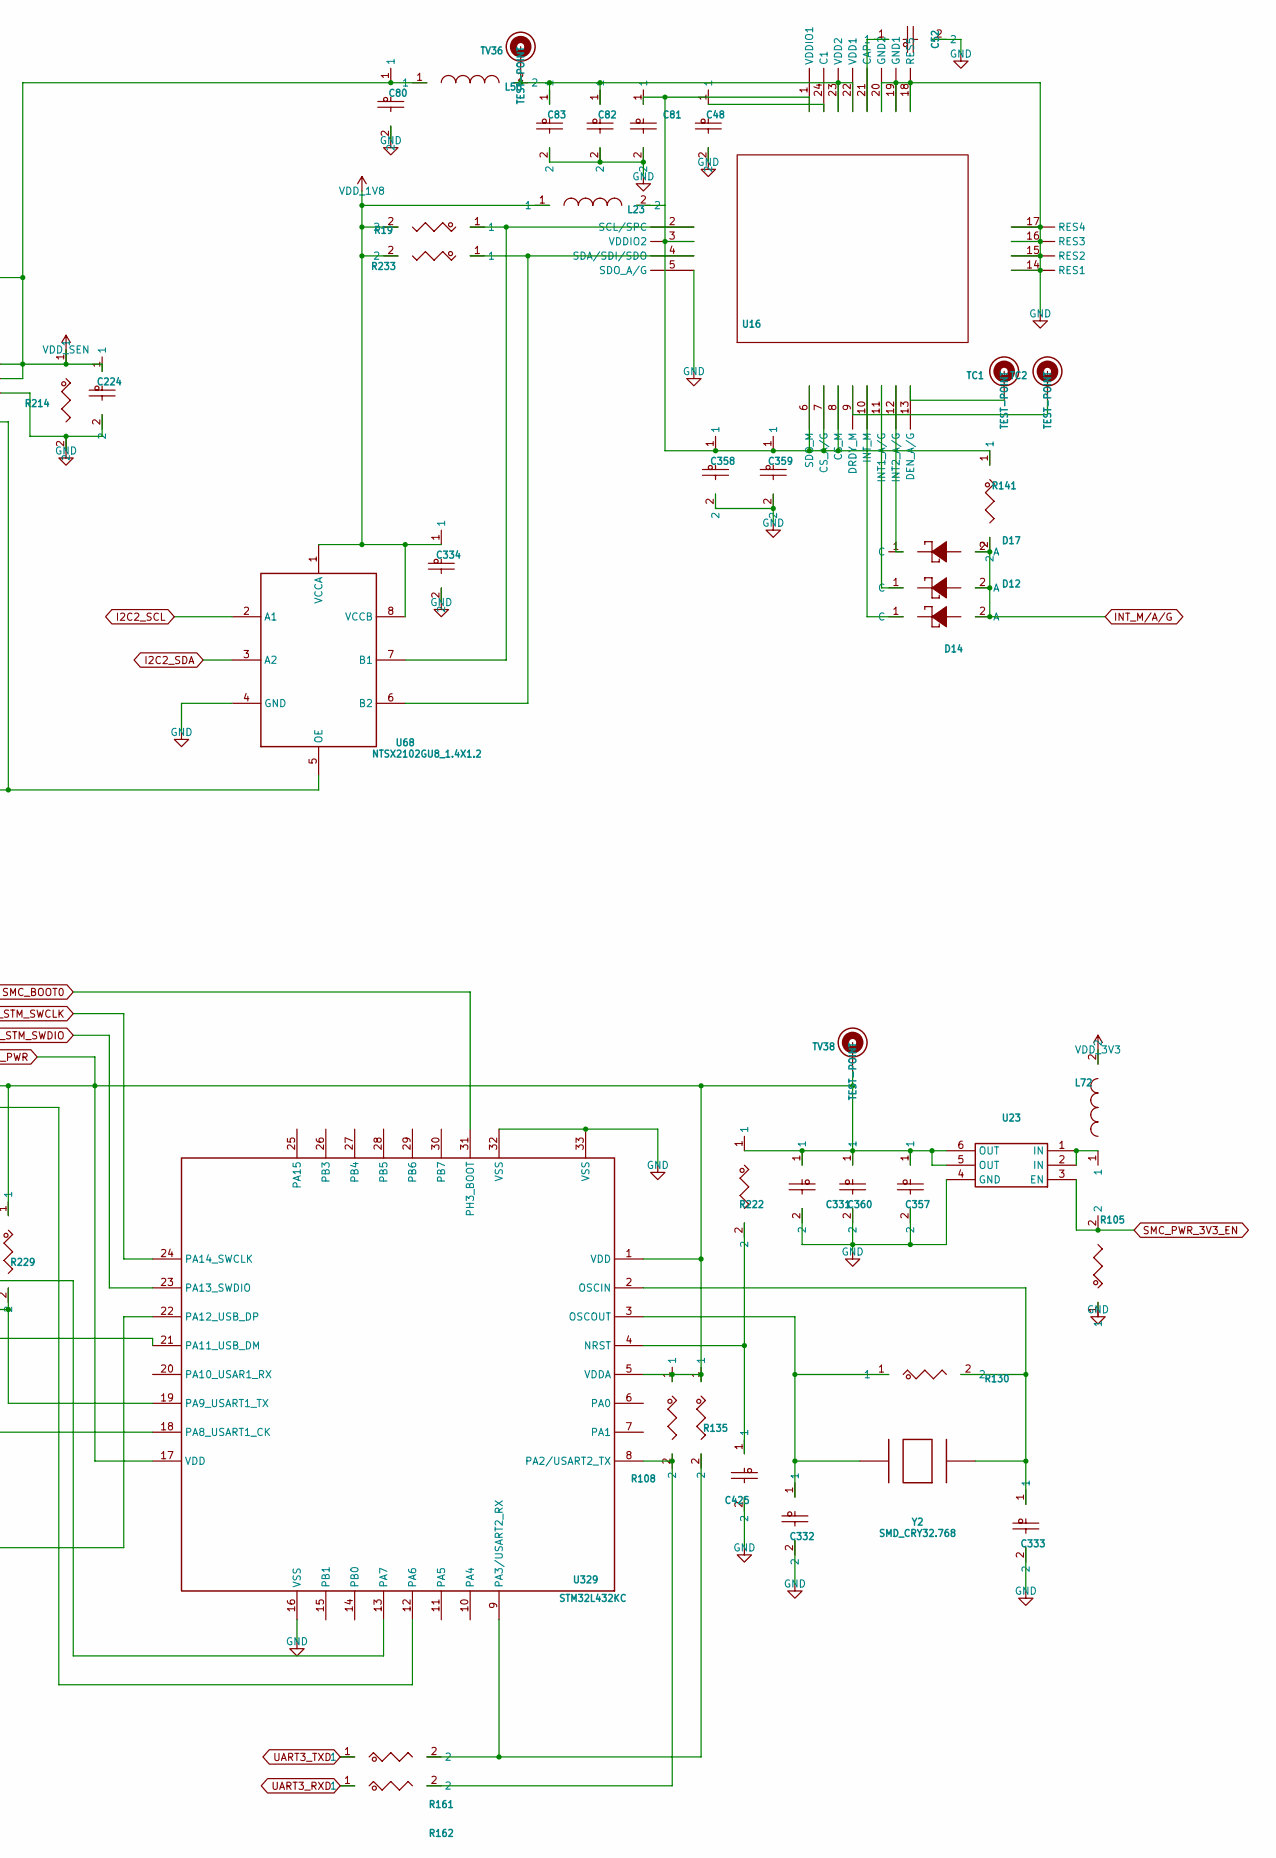
[picture p51: schematic librem5_mainboard_sheet13.kicad_sch, part in row 1, column 2]

Parts:
C48, C79, C80, C81, C82, C143, C223, C224, C254, C331, C334, C354, C357, C358, C359, C425, C426, C438, C512: C0201; VOLTAGE 6.3V
C52: C0201; VOLTAGE 25V
C78, C360, C513: C0402; VOLTAGE 6.3V
C83: C0603; VOLTAGE 6.3V
C332, C333: C0201
D12, D14, D17: DIODE_SCHTKY_0
J9: MICRO-SIMCARD
L22, L23, L56, L64, L72: BEAD-0402
R6, R19, R52, R105, R108, R130, R135, R139, R141, R161, R162, R165, R177, R179, R214, R216, R217, R220, R222, R224, R229, R230, R231, R233: RES_2
TC1, TC2: TEST-POINT
TV36, TV37, TV38: TEST-POINT
TVS8: TVS_0402_882
U4, U23: AP2281
U16: LSM9DS1
U26: VCNL4040
U56: 74LVC1G125-SC70-5
U68: NTSX2102GU8_1.4X1.2
U300: AH3663
U329: STM32L432KC
U330: TXS4555
Y2: SMD_CRY32.768

Connections:
3SW_KILL: R220.1, U56.1 (/OE)
GND: C48.2, C52.2, C78.2, C79.2, C80.2, C81.2, C82.2, C83.2, C143.2, C223.2, C224.2, C254.2, C331.2, C332.2, C333.2, C334.2, C354.2, C357.2, C358.2, C359.2, C360.2, C425.2, C426.2, C438.2, C512.2, C513.2, J9.C5 (GND), J9.GND1, J9.GND2, J9.GND3, J9.GND4, R105.1, R214.2, R217.1, R224.2, TVS8.1 (A1), U4.4 (GND), U16.5 (SDO_A/G), U16.14 (RES1), U16.15 (RES2), U16.16 (RES3), U16.17 (RES4), U16.18 (RES5), U16.19 (GND1), U16.20 (GND2), U23.4 (GND), U26.1 (GND), U56.3 (GND), U68.4 (GND), U300.2 (GND), U329.16 (VSS), U329.32 (VSS), U329.33 (VSS), U330.6 (GND)
HALL: R165.2, U300.3 (OUT)
I2C2_SCL: U26.8 (SCLK), U68.2 (A1)
I2C2_SDA: U26.7 (SDAT), U68.3 (A2)
INT_LIGHT: R52.2, U26.6 (INT)
INT_M/A/G: D12.2 (A), D14.2 (A), D17.2 (A), R141.2
unnamed: C48.1, U16.24 (C1)
unnamed: C52.1, U16.21 (CAP)
unnamed: C78.1, L22.1, R6.2, TV37.1, U26.4 (ANODE)
unnamed: C82.1, C83.1, L56.2, TV36.1, U16.22 (VDD1), U16.23 (VDD2)
unnamed: C143.1, R6.1, U26.3 (VDD)
unnamed: C254.1, C354.1, J9.C1 (VCC), TVS8.2 (A2), U330.3 (VSIM)
unnamed: C332.1, R130.1, U329.3 (OSCOUT), Y2.2
unnamed: C333.1, R130.2, U329.2 (OSCIN), Y2.1
unnamed: C81.1, C358.1, C359.1, R141.1, U16.1 (VDDIO1), U16.3 (VDDIO2), U16.6 (SDO_M), U16.7 (CS_A/G), U16.8 (CS_M)
unnamed: C425.1, R222.2, U329.4 (NRST)
unnamed: C512.1, C513.1, L64.2, U300.1 (VCC)
unnamed: D12.1 (C), U16.11 (INT1_A/G)
unnamed: D14.1 (C), U16.10 (INT_M)
unnamed: D17.1 (C), U16.12 (INT2_A/G)
unnamed: J9.C2 (RST), R230.1
unnamed: J9.C3 (CLK), R216.1
unnamed: J9.C7 (I/O), R177.1
unnamed: J9.CD1 (SW), R231.1
unnamed: L72.1, U23.1 (IN), U23.2 (IN)
unnamed: R19.1, U16.2 (SCL/SPC), U68.7 (B1)
unnamed: R108.2, R162.2, U329.8 (PA2/USART2_TX)
unnamed: R135.2, R161.2, U329.9 (PA3/USART2_RX)
unnamed: R139.1, U26.5 (CATHODE_LED)
unnamed: R139.2, U26.2 (CATHODE_SENSOR)
unnamed: R177.2, U330.4 (SIMIO)
unnamed: R179.1, R231.2, U329.22 (PA12_USB_DP)
unnamed: R216.2, U330.7 (SIMCLK)
unnamed: R217.2, U4.3 (EN), U56.4 (Y), U68.5 (OE)
unnamed: R224.1, U329.12 (PA6), U330.12 (SEL)
unnamed: R229.2, U329.19 (PA9_USART1_TX), U330.10 (IO)
unnamed: R230.2, U330.5 (SIMRST)
unnamed: R233.1, U16.4 (SDA/SDI/SDO), U68.6 (B2)
unnamed: TC1.1, U16.13 (DEN_A/G)
unnamed: TC2.1, U16.9 (DRDY_M)
unnamed: U329.13 (PA7), U330.11 (EN)
unnamed: U329.18 (PA8_USART1_CK), U330.8 (CLK)
unnamed: U329.21 (PA11_USB_DM), U330.9 (RST)
SMC_BOOT0: U329.31 (PH3_BOOT)
SMC_PWR: C331.1, C357.1, C360.1, C426.1, C438.1, R108.1, R135.1, R179.2, R222.1, R229.1, TV38.1, U23.5 (OUT), U23.6 (OUT), U329.1 (VDD), U329.5 (VDDA), U329.17 (VDD), U330.1 (VCC), U330.2 (VBATT)
SMC_PWR_3V3_EN: R105.2, U23.3 (EN)
SMC_STM_SWCLK: U329.24 (PA14_SWCLK)
SMC_STM_SWDIO: U329.23 (PA13_SWDIO)
UART3_RXD: R162.1
UART3_TXD: R161.1
VDD_1V8: C334.1, L23.1, R19.2, R52.1, R165.1, R220.2, R233.2, U56.2 (A), U56.5 (VCC), U68.1 (VCCA), U68.8 (VCCB)
VDD_3V3: C223.1, L64.1, L72.2, U4.1 (IN)
VDD_SEN: C79.1, C80.1, C224.1, L22.2, L56.1, R214.1, U4.5 (OUT), U4.6 (OUT)
