gralco/l5-schematic/CAD/PADS/librem5_mainboard/librem5_mainboard_kicad_conversion/librem5_mainboard_sheet14.kicad_sch

## KiCad design CAD/PADS/librem5_mainboard/librem5_mainboard_kicad_conversion/librem5_mainboard_sheet14.kicad_sch (2026-05-21)

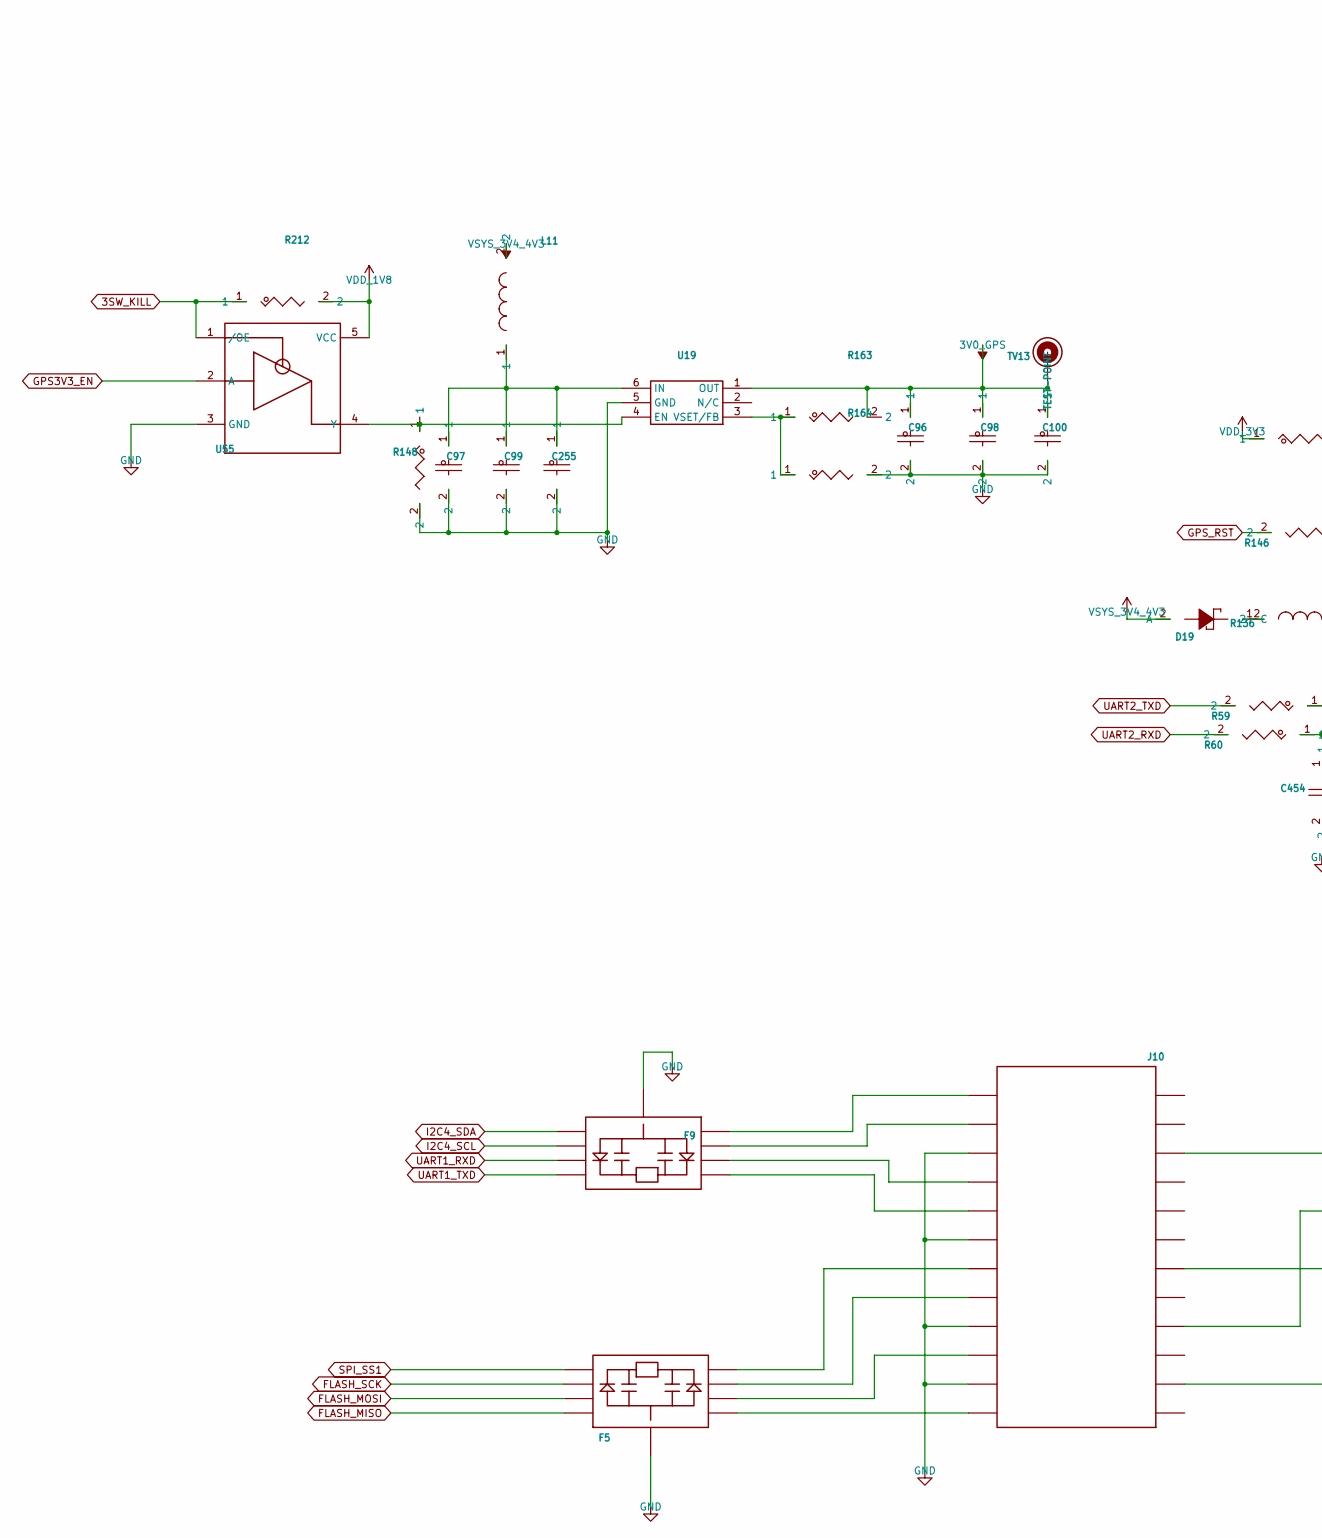
[picture p52: schematic librem5_mainboard_sheet14.kicad_sch, part in row 1, column 1]

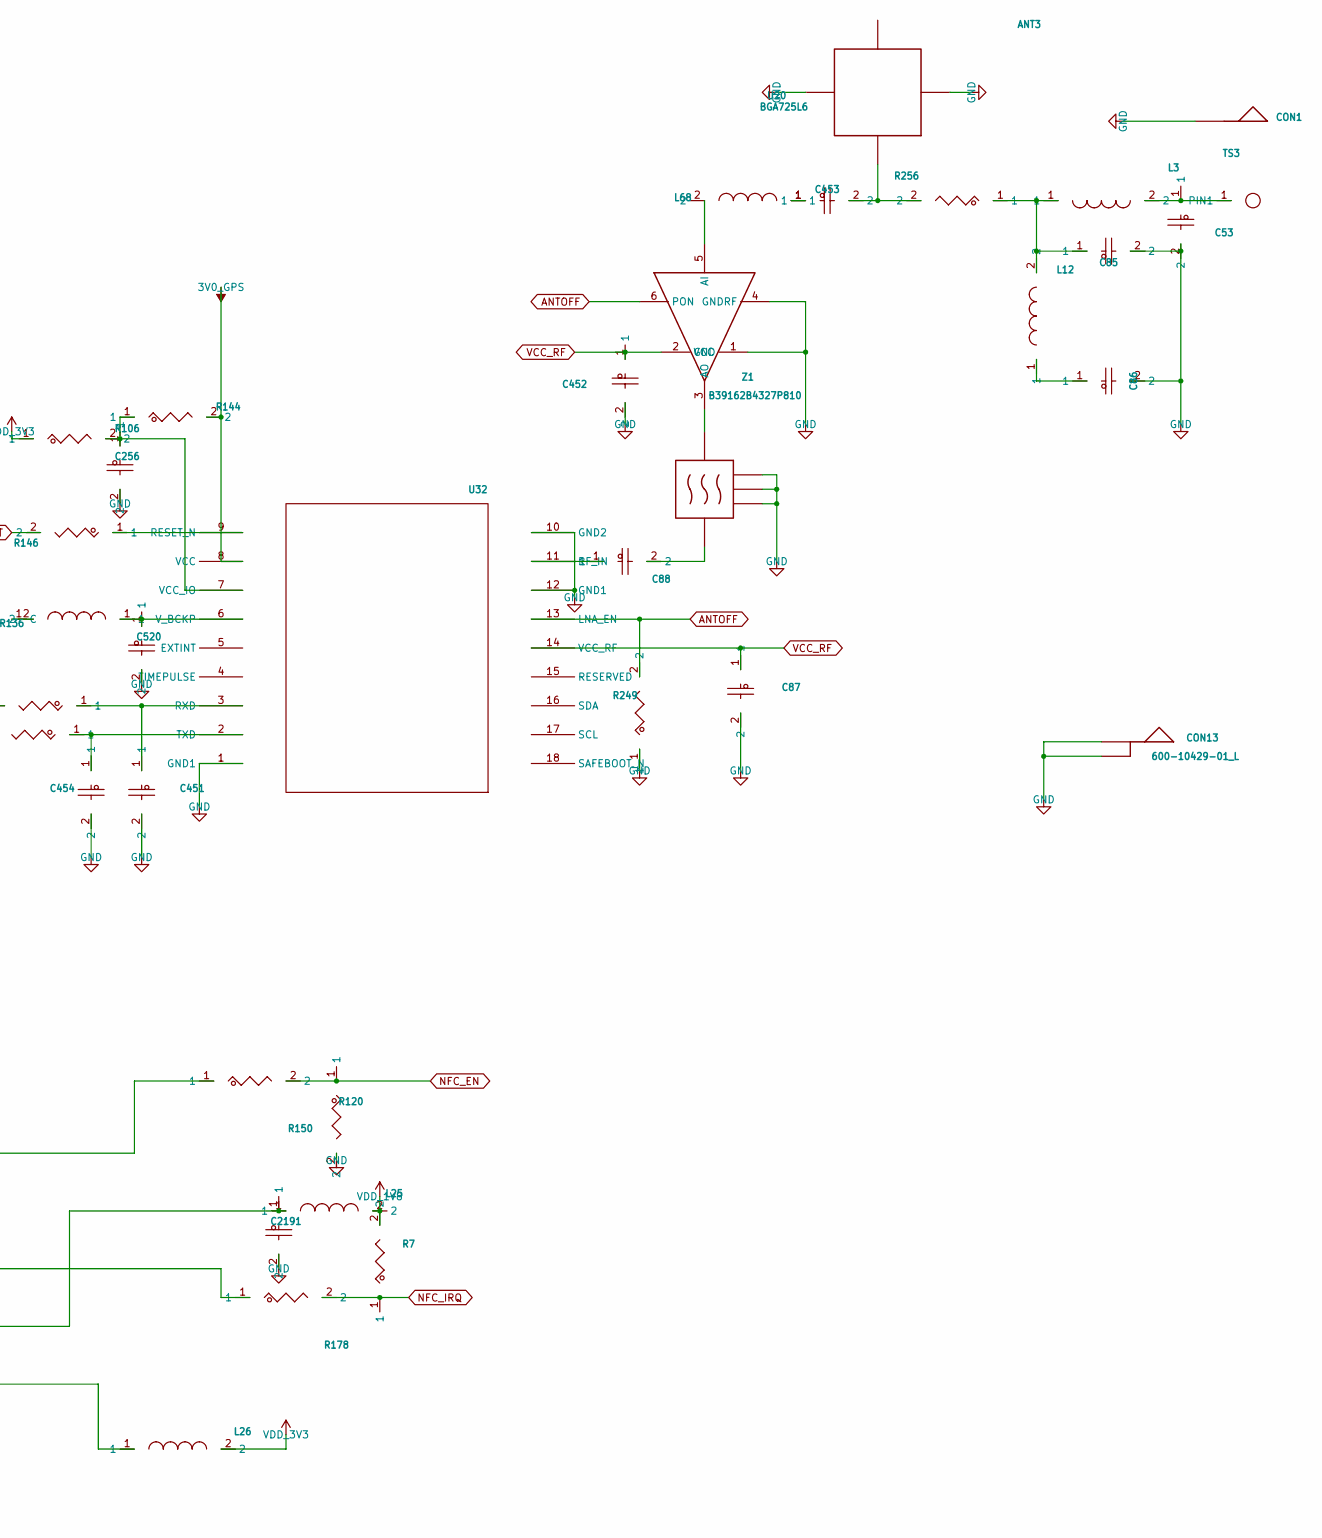
[picture p53: schematic librem5_mainboard_sheet14.kicad_sch, part in row 1, column 2]

Parts:
ANT3: APEX2X2
C53, C85, C86, C87, C451, C452, C454: C0201
C88, C100, C255, C453: C0201; VOLTAGE 25V
C96, C97: C0402; VOLTAGE 6.3V
C98, C99, C520, C2191: C0201; VOLTAGE 6.3V
C256: C0201; VOLTAGE 50V
CON1: ANT_CON_3
CON13: 600-10429-01_L
D19: DIODE_SCHTKY_0
F5, F9: FILTER_ESD_BUS4
J10: CAMERA24PIN035-NFC
L3, L25, L26, L68: BEAD-0201
L11, L12: BEAD-0402
R7, R59, R60, R106, R120, R144, R146, R148, R150, R163, R164, R178, R212, R256: RES_2
R136: BEAD-0201
R249: R_0201
TS3: SC-M1.4
TV13: TEST-POINT
U19: TPS78001DRV
U20: BGA725L6
U32: MAX-8
U55: 74LVC1G125-SC70-5
Z1: B39162B4327P810

Connections:
3SW_KILL: R212.1, U55.1 (/OE)
3V0_GPS: C96.1, C98.1, C100.1, R144.2, R163.2, TV13.1, U19.1 (OUT), U32.8 (VCC)
ANTOFF: R249.2, U20.6 (PON), U32.13 (LNA_EN)
FLASH_MISO: F5.4
FLASH_MOSI: F5.3
FLASH_SCK: F5.2
GND: ANT3.3, ANT3.4, C53.2, C85.2, C86.2, C87.2, C96.2, C97.2, C98.2, C99.2, C100.2, C255.2, C256.2, C451.2, C452.2, C454.2, C520.2, C2191.2, CON1.1, CON13.1, CON13.2, F5.9, F9.9, J10.5, J10.11, J10.17, J10.21, R120.2, R148.2, R164.2, R249.1, U19.5 (GND), U20.1 (GND), U20.4 (GNDRF), U32.1 (GND1), U32.10 (GND2), U32.12 (GND1), U55.3 (GND), Z1.2, Z1.3, Z1.5
GPS3V3_EN: U55.2 (A)
GPS_RST: R146.2
I2C4_SCL: F9.6
I2C4_SDA: F9.5
NFC_EN: R120.1, R150.2
NFC_IRQ: R7.1, R178.2
unnamed: ANT3.1, C453.2, R256.2
unnamed: C53.1, L3.2, TS3.1
unnamed: C85.1, L3.1, L12.2, R256.1
unnamed: C86.1, L12.1
unnamed: C88.1, U32.11 (RF_IN)
unnamed: C88.2, Z1.4
unnamed: C97.1, C99.1, C255.1, L11.1, U19.6 (IN)
unnamed: C256.1, R106.2, R144.1, U32.7 (VCC_IO)
unnamed: C451.1, R59.1, U32.3 (RXD)
unnamed: C453.1, L68.1
unnamed: C454.1, R60.1, U32.2 (TXD)
unnamed: C520.1, R136.1, U32.6 (V_BCKP)
unnamed: C2191.1, J10.18, L25.1
unnamed: CON13.3 (GND), CON13.4 (GND), CON13.5 (GND)
unnamed: D19.1 (C), R136.2
unnamed: F5.5, J10.23
unnamed: F5.6, J10.19
unnamed: F5.7, J10.15
unnamed: F5.8, J10.13
unnamed: F9.1, J10.9
unnamed: F9.2, J10.7
unnamed: F9.3, J10.3
unnamed: F9.4, J10.1
unnamed: J10.6, R150.1
unnamed: J10.14, R178.1
unnamed: J10.22, L26.1
unnamed: L68.2, U20.5 (AI)
unnamed: R146.1, U32.9 (RESET_N)
unnamed: R148.1, U19.4 (EN), U55.4 (Y)
unnamed: R163.1, R164.1, U19.3 (VSET/FB)
unnamed: U20.3 (AO), Z1.1
SPI_SS1: F5.1
UART1_RXD: F9.7
UART1_TXD: F9.8
UART2_RXD: R60.2
UART2_TXD: R59.2
VCC_RF: C87.1, C452.1, U20.2 (VCC), U32.14 (VCC_RF)
VDD_1V8: L25.2, R7.2, R212.2, U55.5 (VCC)
VDD_3V3: L26.2, R106.1
VSYS_3V4_4V3: D19.2 (A), L11.2
