gralco/l5-schematic/CAD/PADS/librem5_mainboard/librem5_mainboard_kicad_conversion/librem5_mainboard_sheet15.kicad_sch

## KiCad design CAD/PADS/librem5_mainboard/librem5_mainboard_kicad_conversion/librem5_mainboard_sheet15.kicad_sch (2026-05-21)

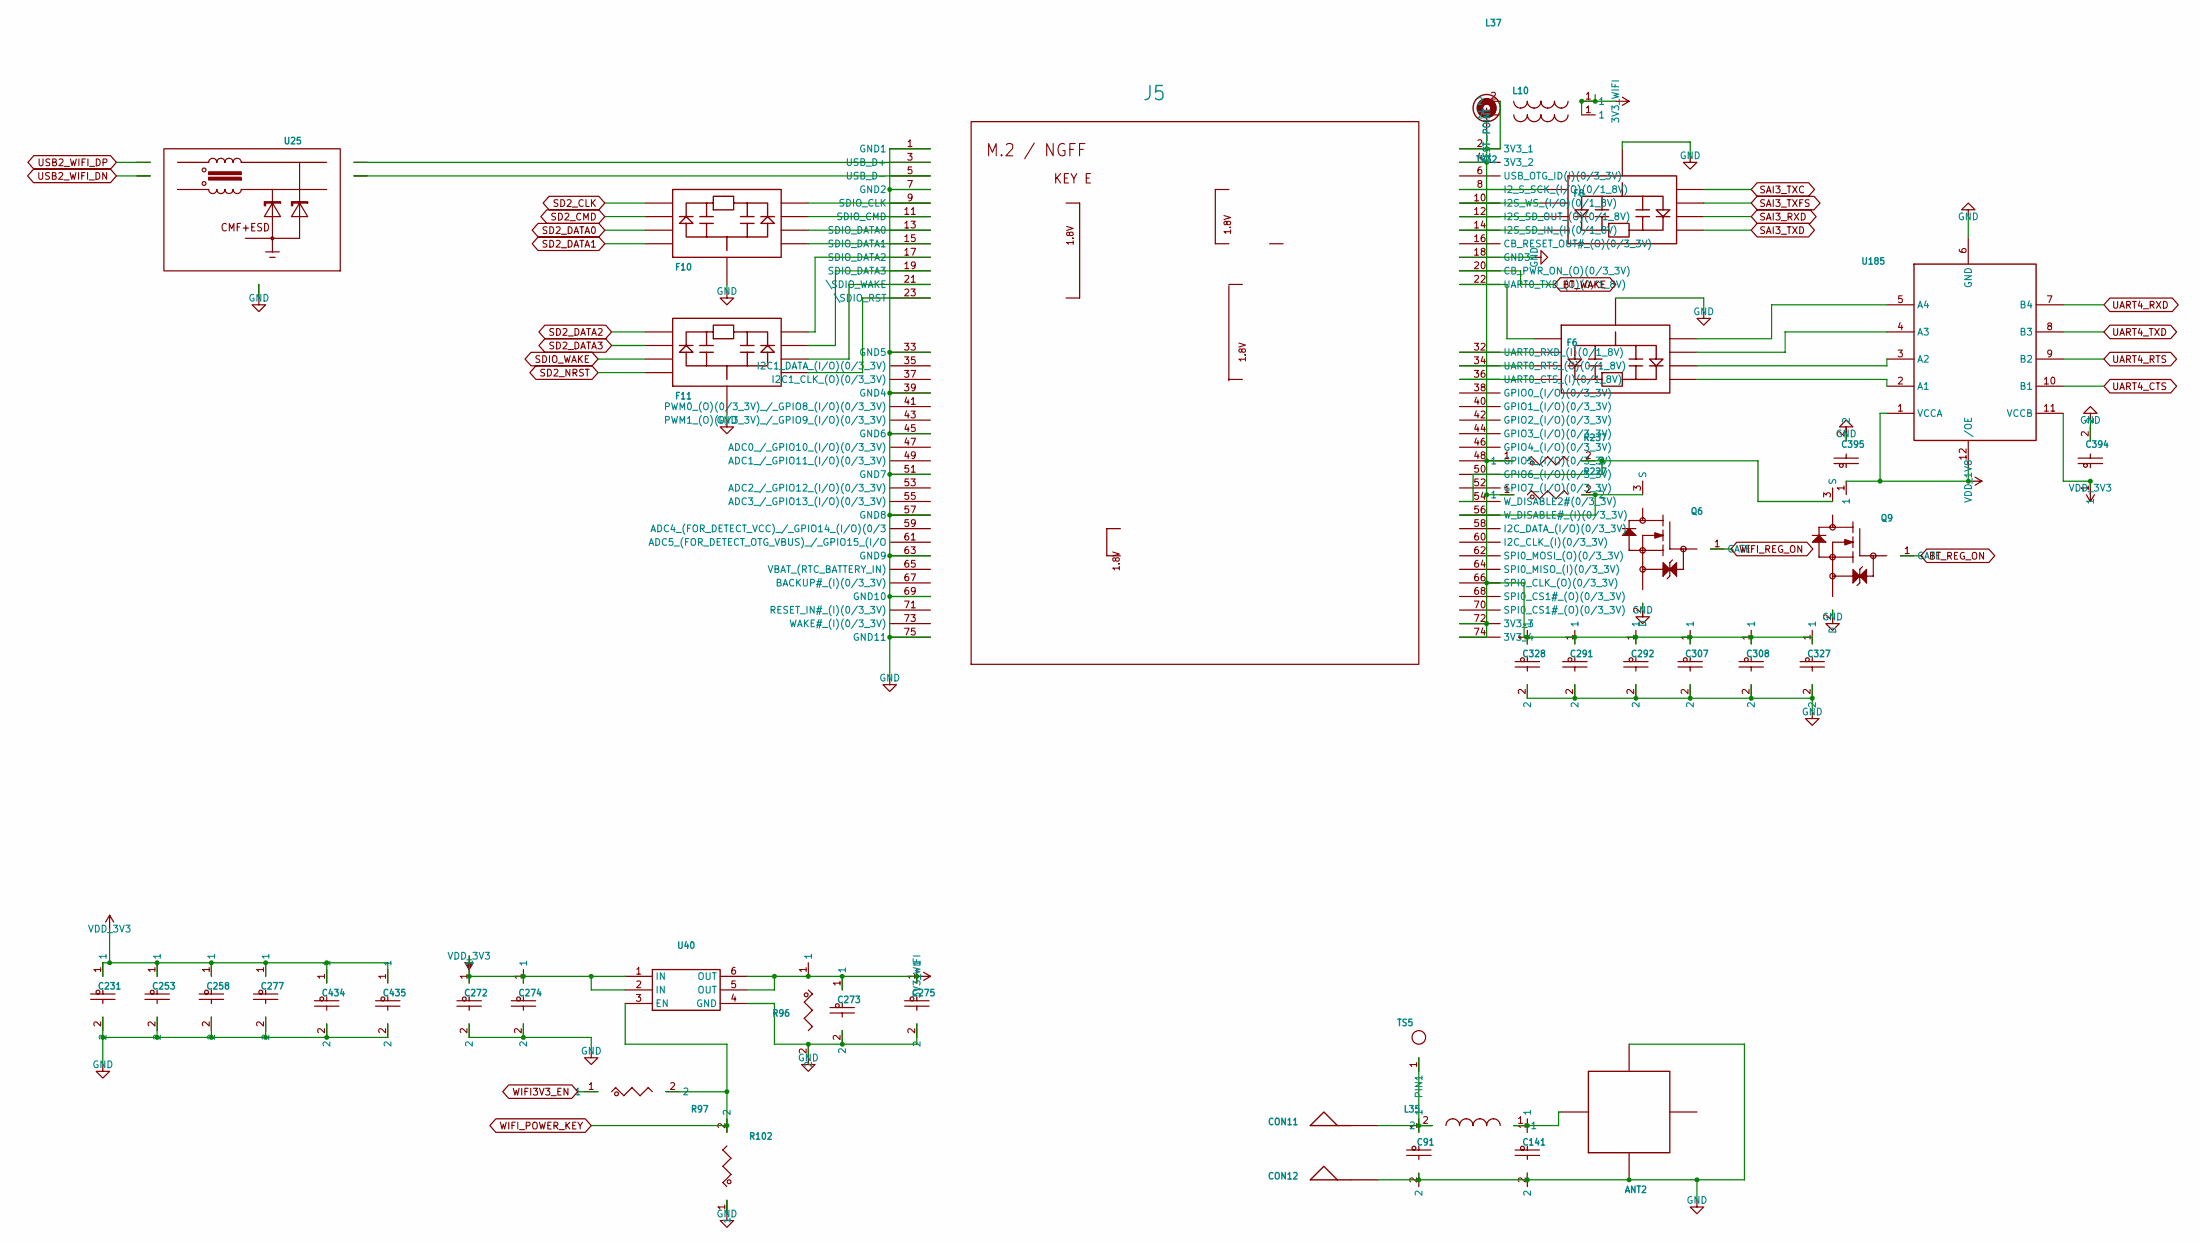
[picture p54: schematic librem5_mainboard_sheet15.kicad_sch]

Parts:
ANT2: APEX2X2
C91, C141: C0201
C231, C253, C258, C277, C308, C327: C0603; VOLTAGE 6.3V
C272, C273, C434, C435: C0402; VOLTAGE 6.3V
C274, C275, C291, C292, C307, C328, C394, C395: C0201; VOLTAGE 6.3V
CON11, CON12: ANT_CON1
F6, F8, F10, F11: FILTER_ESD_BUS4
J5: KEY_E
L10, L37: BEAD-0402
L35: BEAD-0201
Q6, Q9: 2SK3018
R96, R97, R102, R227, R237: RES_2
TS5: SC-M1.4
TV32: TEST-POINT
U25: PCMF1USB3S_5P
U40: AP2281
U185: NTBA104_XQFN12

Connections:
3V3_WIFI: C273.1, C275.1, L10.1, L37.1, R96.1, U40.5 (OUT), U40.6 (OUT)
BT_REG_ON: Q9.1 (GATE)
BT_WAKE: J5.20 (CB_PWR_ON_(O)(0/3_3V))
GND: ANT2.3, ANT2.4, C91.2, C141.2, C231.2, C253.2, C258.2, C272.2, C273.2, C274.2, C275.2, C277.2, C291.2, C292.2, C307.2, C308.2, C327.2, C328.2, C394.2, C395.2, C434.2, C435.2, CON12.1, F6.9, F8.9, F10.9, F11.9, J5.1 (GND1), J5.7 (GND2), J5.18 (GND3), J5.33 (GND5), J5.39 (GND4), J5.45 (GND6), J5.51 (GND7), J5.57 (GND8), J5.63 (GND9), J5.69 (GND10), J5.75 (GND11), Q6.2 (D), Q9.2 (D), R96.2, R102.1, U25.3, U40.4 (GND), U185.6 (GND)
unnamed: ANT2.1, C141.1, L35.1
unnamed: C91.1, CON11.1, L35.2, TS5.1
unnamed: C291.1, C292.1, C307.1, C308.1, C327.1, C328.1, J5.2 (3V3_1), J5.4 (3V3_2), J5.72 (3V3_3), J5.74 (3V3_4), L10.2, R227.1, R237.1, TV32.1
unnamed: F6.1, J5.36 (UART0_CTS_(I)(0/1_8V))
unnamed: F6.2, J5.34 (UART0_RTS_(O)(0/1_8V))
unnamed: F6.3, J5.32 (UART0_RXD_(I)(0/1_8V))
unnamed: F6.4, J5.22 (UART0_TXD_(O)(0/1_8V))
unnamed: F6.5, U185.5 (A4)
unnamed: F6.6, U185.4 (A3)
unnamed: F6.7, U185.3 (A2)
unnamed: F6.8, U185.2 (A1)
unnamed: F8.1, J5.14 (I2S_SD_IN_(I)(0/1_8V))
unnamed: F8.2, J5.12 (I2S_SD_OUT_(O)(0/1_8V))
unnamed: F8.3, J5.10 (I2S_WS_(I/O)(0/1_8V))
unnamed: F8.4, J5.8 (I2_S_SCK_(I/O)(0/1_8V))
unnamed: F10.5, J5.15 (SDIO_DATA1)
unnamed: F10.6, J5.13 (SDIO_DATA0)
unnamed: F10.7, J5.11 (SDIO_CMD)
unnamed: F10.8, J5.9 (SDIO_CLK)
unnamed: F11.5, J5.23 (\SDIO_RST)
unnamed: F11.6, J5.21 (\SDIO_WAKE)
unnamed: F11.7, J5.19 (SDIO_DATA3)
unnamed: F11.8, J5.17 (SDIO_DATA2)
unnamed: J5.3 (USB_D+), U25.1
unnamed: J5.5 (USB_D-), U25.2
unnamed: J5.54 (W_DISABLE2#(0/3_3V)), Q9.3 (S), R237.2
unnamed: J5.56 (W_DISABLE#_(I)(0/3_3V)), Q6.3 (S), R227.2
SAI3_RXD: F8.7
SAI3_TXC: F8.5
SAI3_TXD: F8.8
SAI3_TXFS: F8.6
SD2_CLK: F10.1
SD2_CMD: F10.2
SD2_DATA0: F10.3
SD2_DATA1: F10.4
SD2_DATA2: F11.1
SD2_DATA3: F11.2
SD2_NRST: F11.4
SDIO_WAKE: F11.3
UART4_CTS: U185.10 (B1)
UART4_RTS: U185.9 (B2)
UART4_RXD: U185.7 (B4)
UART4_TXD: U185.8 (B3)
USB2_WIFI_DN: U25.5
USB2_WIFI_DP: U25.4
VDD_1V8: C395.1, U185.1 (VCCA), U185.12 (/OE)
VDD_3V3: C231.1, C253.1, C258.1, C272.1, C274.1, C277.1, C394.1, C434.1, C435.1, U40.1 (IN), U40.2 (IN), U185.11 (VCCB)
WIFI3V3_EN: R97.1
WIFI_POWER_KEY: R97.2, R102.2, U40.3 (EN)
WIFI_REG_ON: Q6.1 (GATE)
