gralco/l5-schematic/CAD/PADS/librem5_mainboard/librem5_mainboard_kicad_conversion/librem5_mainboard_sheet16.kicad_sch

## KiCad design CAD/PADS/librem5_mainboard/librem5_mainboard_kicad_conversion/librem5_mainboard_sheet16.kicad_sch (2026-05-21)

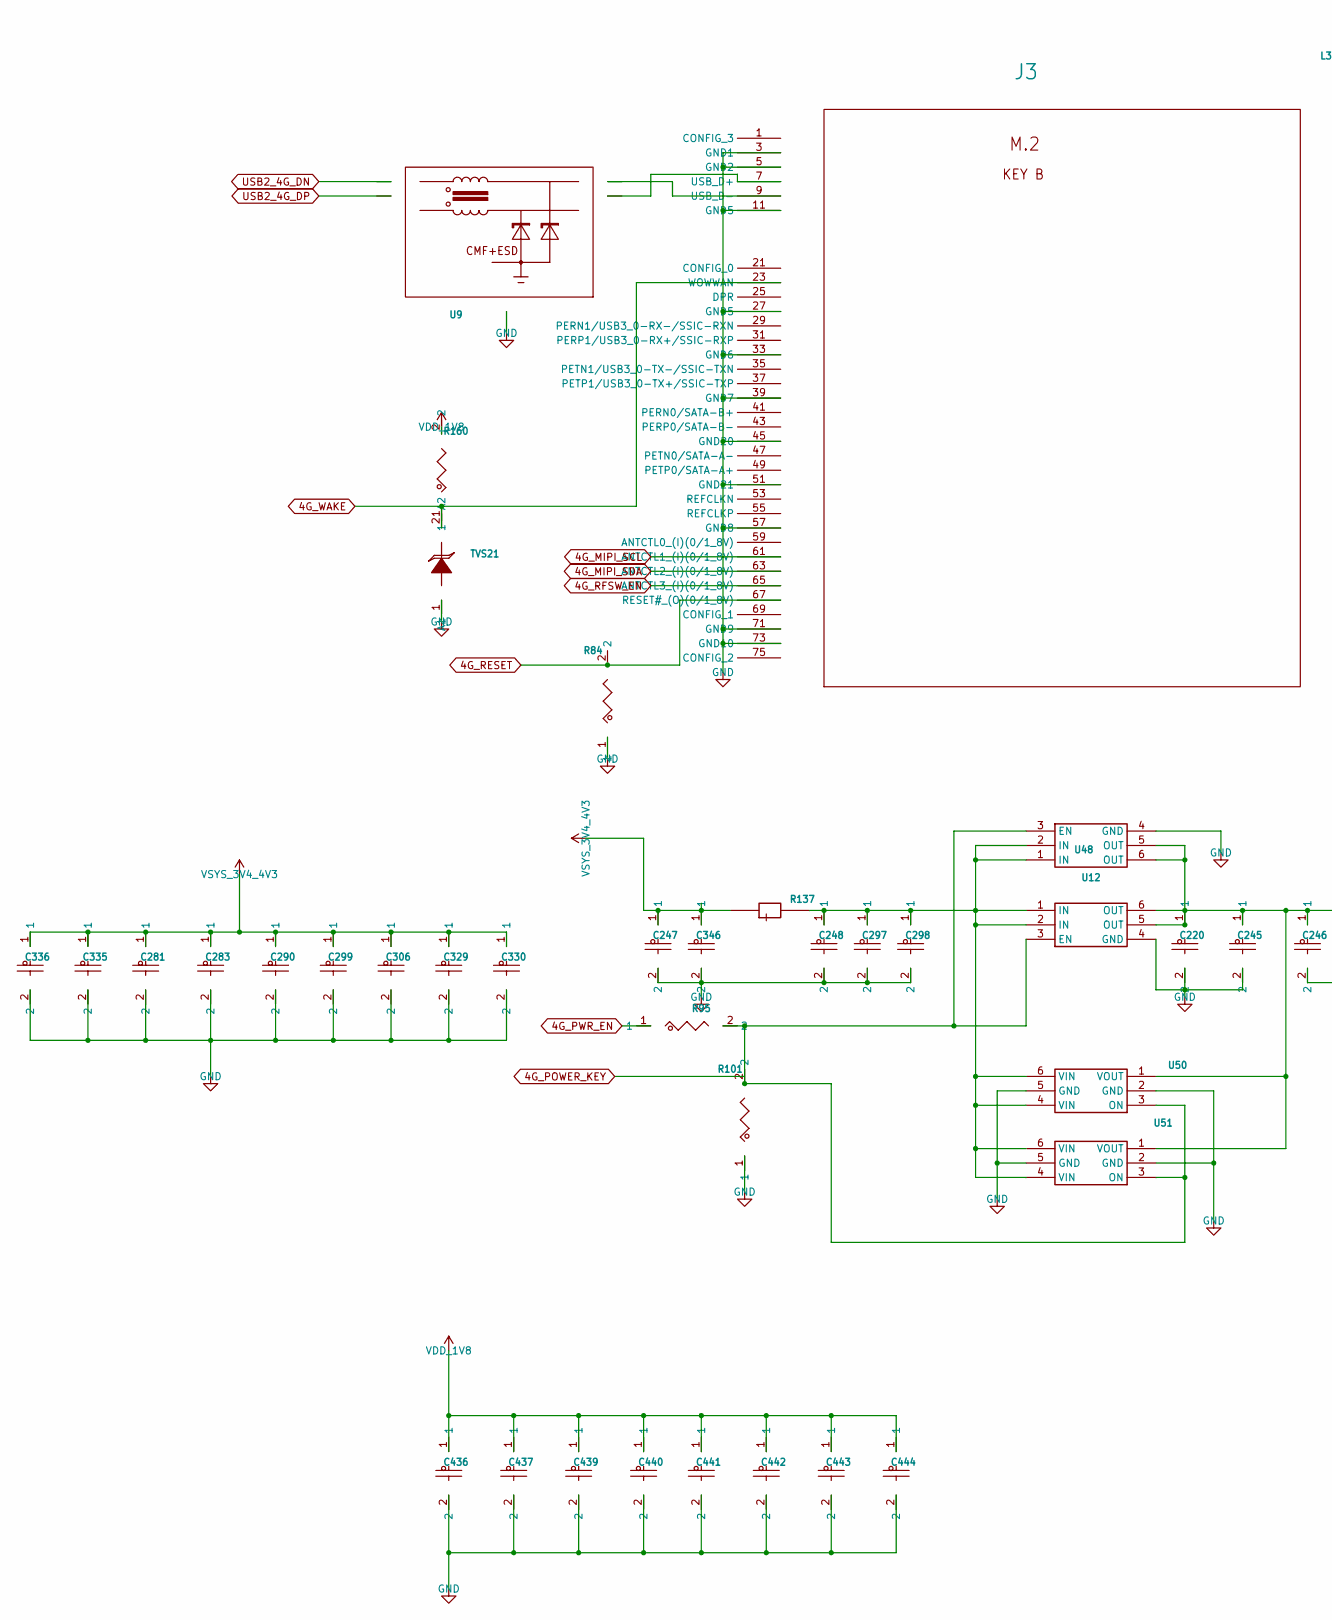
[picture p55: schematic librem5_mainboard_sheet16.kicad_sch, part in row 1, column 1]

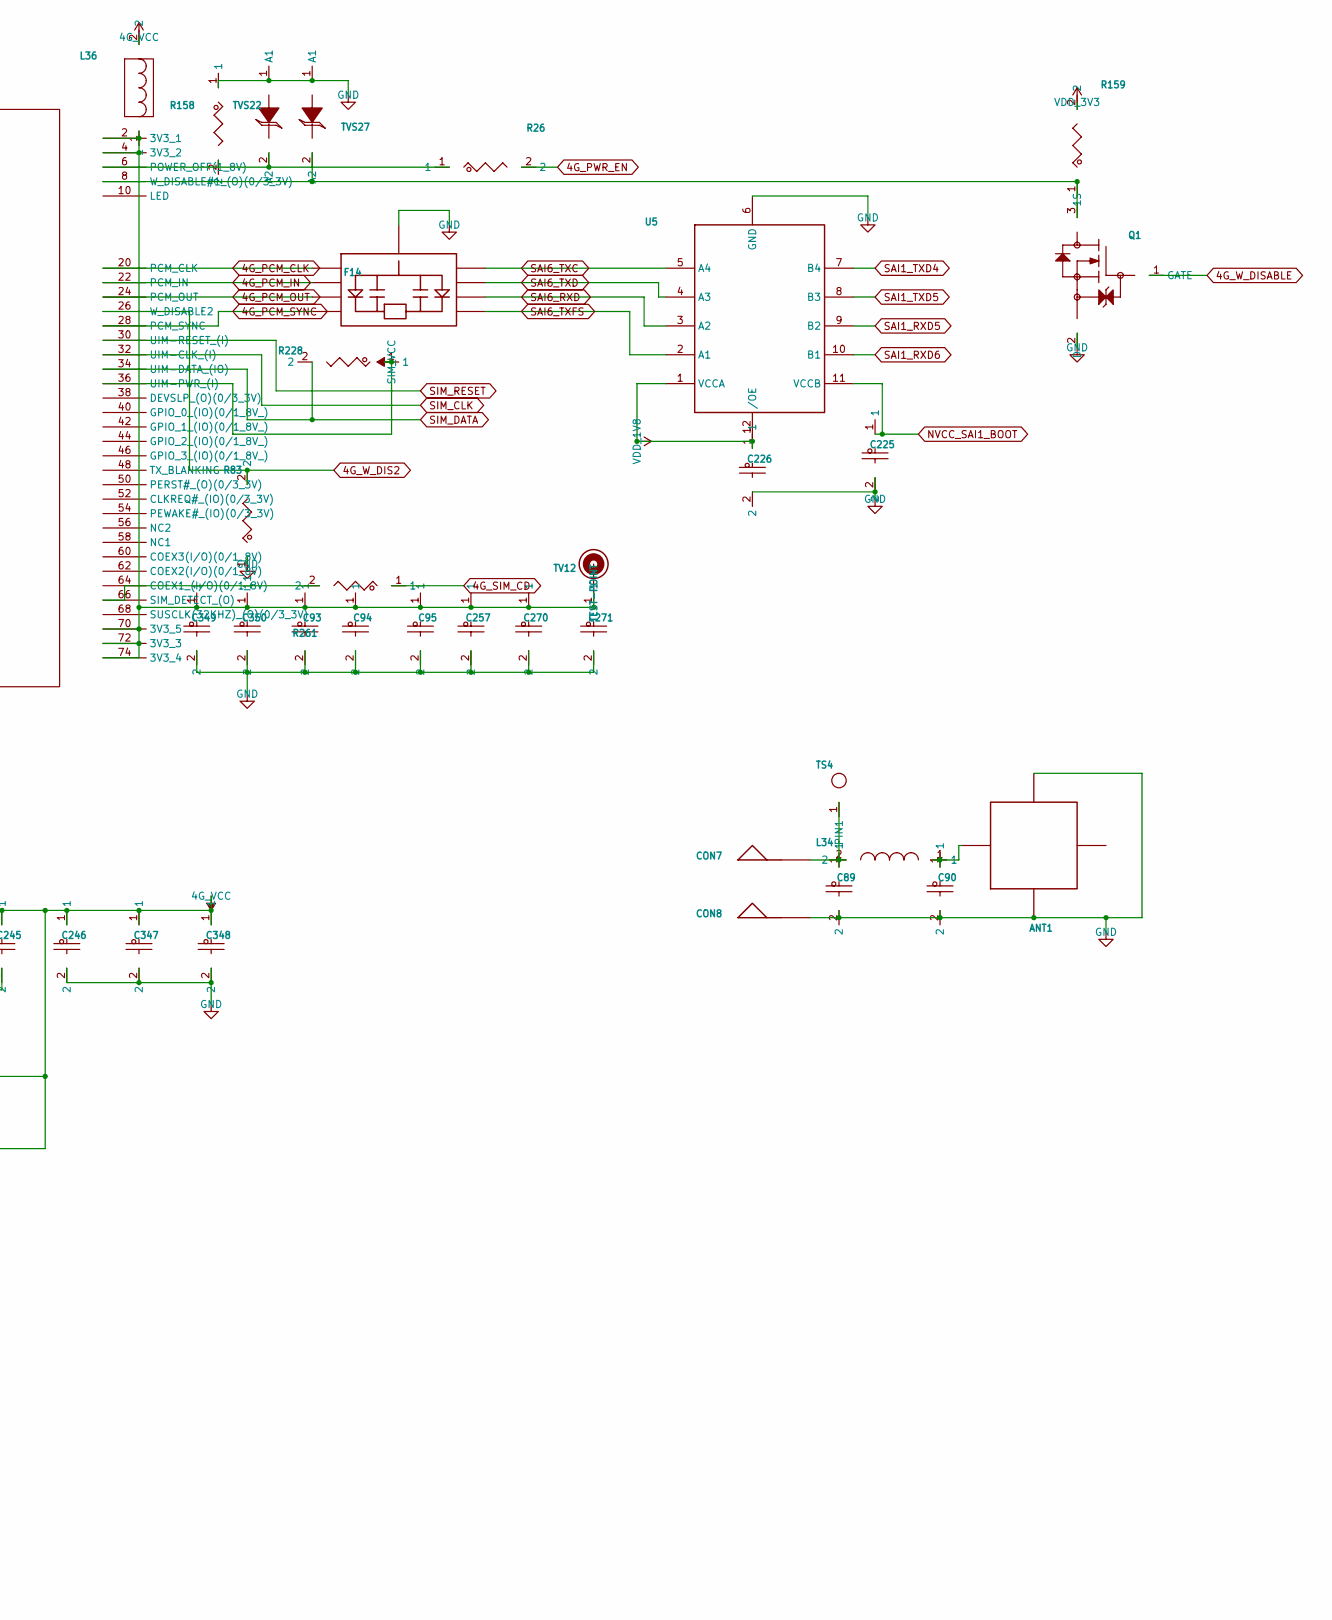
[picture p56: schematic librem5_mainboard_sheet16.kicad_sch, part in row 1, column 2]

Parts:
ANT1: APEX2X2
C89, C90: C0201
C93, C94, C95, C225, C226, C257, C298, C346, C347, C348, C349, C350, C436, C437, C439, C440, C441, C442, C443, C444: C0201; VOLTAGE 6.3V
C220, C245, C246, C247, C248, C270, C271, C281, C283, C290, C299, C306, C329, C330, C335, C336: C0603; VOLTAGE 6.3V
C297: C0402; VOLTAGE 6.3V
CON7, CON8: ANT_CON1
F14: FILTER_ESD_BUS4
J3: KEY_B
L34: BEAD-0201
L36: BEAD-4030
Q1: 2SK3018
R26, R83, R84, R95, R101, R158, R159, R160, R228: RES_2
R137: CURRENT_R
R261: R_0201
TS4: SC-M1.4
TV12: TEST-POINT
TVS21, TVS22, TVS27: TVS_0402_882
U5: NTBA104_XQFN12
U9: PCMF1USB3S_5P
U12, U48: AP2281
U50, U51: TPS22929D

Connections:
4G_MIPI_SCL: J3.61 (ANTCTL1_(I)(0/1_8V))
4G_MIPI_SDA: J3.63 (ANTCTL2_(I)(0/1_8V))
4G_PCM_CLK: F14.4, J3.20 (PCM_CLK)
4G_PCM_IN: F14.3, J3.22 (PCM_IN)
4G_PCM_OUT: F14.2, J3.24 (PCM_OUT)
4G_PCM_SYNC: F14.1, J3.28 (PCM_SYNC)
4G_PWR_EN: R26.2, R95.1
4G_RESET: J3.67 (RESET#_(O)(0/1_8V)), R84.2
4G_RFSW_EN: J3.65 (ANTCTL3_(I)(0/1_8V))
4G_SIM_CD: R261.1
4G_VCC: C220.1, C245.1, C246.1, C347.1, C348.1, L36.2, U12.5 (OUT), U12.6 (OUT), U48.5 (OUT), U48.6 (OUT), U50.1 (VOUT), U51.1 (VOUT)
4G_WAKE: J3.23 (WOWWAN), R160.1, TVS21.2 (A2)
4G_W_DIS2: J3.26 (W_DISABLE2), R83.2
4G_W_DISABLE: Q1.1 (GATE)
GND: ANT1.3, ANT1.4, C89.2, C90.2, C93.2, C94.2, C95.2, C220.2, C225.2, C226.2, C245.2, C246.2, C247.2, C248.2, C257.2, C270.2, C271.2, C281.2, C283.2, C290.2, C297.2, C298.2, C299.2, C306.2, C329.2, C330.2, C335.2, C336.2, C346.2, C347.2, C348.2, C349.2, C350.2, C436.2, C437.2, C439.2, C440.2, C441.2, C442.2, C443.2, C444.2, CON8.1, F14.9, J3.3 (GND1), J3.5 (GND2), J3.11 (GND5), J3.27 (GND5), J3.33 (GND6), J3.39 (GND7), J3.45 (GND20), J3.51 (GND21), J3.57 (GND8), J3.71 (GND9), J3.73 (GND10), Q1.2 (D), R83.1, R84.1, R101.1, R158.1, TVS21.1 (A1), TVS22.1 (A1), TVS27.1 (A1), U5.6 (GND), U9.3, U12.4 (GND), U48.4 (GND), U50.2 (GND), U50.5 (GND), U51.2 (GND), U51.5 (GND)
NVCC_SAI1_BOOT: C225.1, U5.11 (VCCB)
unnamed: ANT1.1, C90.1, L34.1
unnamed: C89.1, CON7.1, L34.2, TS4.1
unnamed: C248.1, C297.1, C298.1, R137.2, U12.1 (IN), U12.2 (IN), U48.1 (IN), U48.2 (IN), U50.4 (VIN), U50.6 (VIN), U51.4 (VIN), U51.6 (VIN)
unnamed: C93.1, C94.1, C95.1, C257.1, C270.1, C271.1, C349.1, C350.1, J3.2 (3V3_1), J3.4 (3V3_2), J3.70 (3V3_5), J3.72 (3V3_3), J3.74 (3V3_4), L36.1, TV12.1
unnamed: J3.6 (POWER_OFF(1_8V)), R26.1, TVS22.2 (A2)
unnamed: J3.7 (USB_D+), U9.2
unnamed: J3.8 (W_DISABLE#1_(O)(0/3_3V)), Q1.3 (S), R159.1, TVS27.2 (A2)
unnamed: J3.9 (USB_D-), U9.1
unnamed: J3.66 (SIM_DETECT_(O)), R261.2
unnamed: R95.2, R101.2, U12.3 (EN), U48.3 (EN), U50.3 (ON), U51.3 (ON)
SAI1_RXD5: U5.9 (B2)
SAI1_RXD6: U5.10 (B1)
SAI1_TXD4: U5.7 (B4)
SAI1_TXD5: U5.8 (B3)
SAI6_RXD: F14.7, U5.3 (A2)
SAI6_TXC: F14.5, U5.5 (A4)
SAI6_TXD: F14.6, U5.4 (A3)
SAI6_TXFS: F14.8, U5.2 (A1)
SIM_CLK: J3.32 (UIM-CLK_(I))
SIM_DATA: J3.34 (UIM-DATA_(IO)), R228.2
SIM_RESET: J3.30 (UIM-RESET_(I))
SIM_VCC: J3.36 (UIM-PWR_(I)), R228.1
USB2_4G_DN: U9.4
USB2_4G_DP: U9.5
VDD_1V8: C226.1, C436.1, C437.1, C439.1, C440.1, C441.1, C442.1, C443.1, C444.1, R160.2, U5.1 (VCCA), U5.12 (/OE)
VDD_3V3: R159.2
VSYS_3V4_4V3: C247.1, C281.1, C283.1, C290.1, C299.1, C306.1, C329.1, C330.1, C335.1, C336.1, C346.1, R137.1
