gralco/l5-schematic/CAD/PADS/librem5_mainboard/librem5_mainboard_kicad_conversion/librem5_mainboard_sheet17.kicad_sch

## KiCad design CAD/PADS/librem5_mainboard/librem5_mainboard_kicad_conversion/librem5_mainboard_sheet17.kicad_sch (2026-05-21)

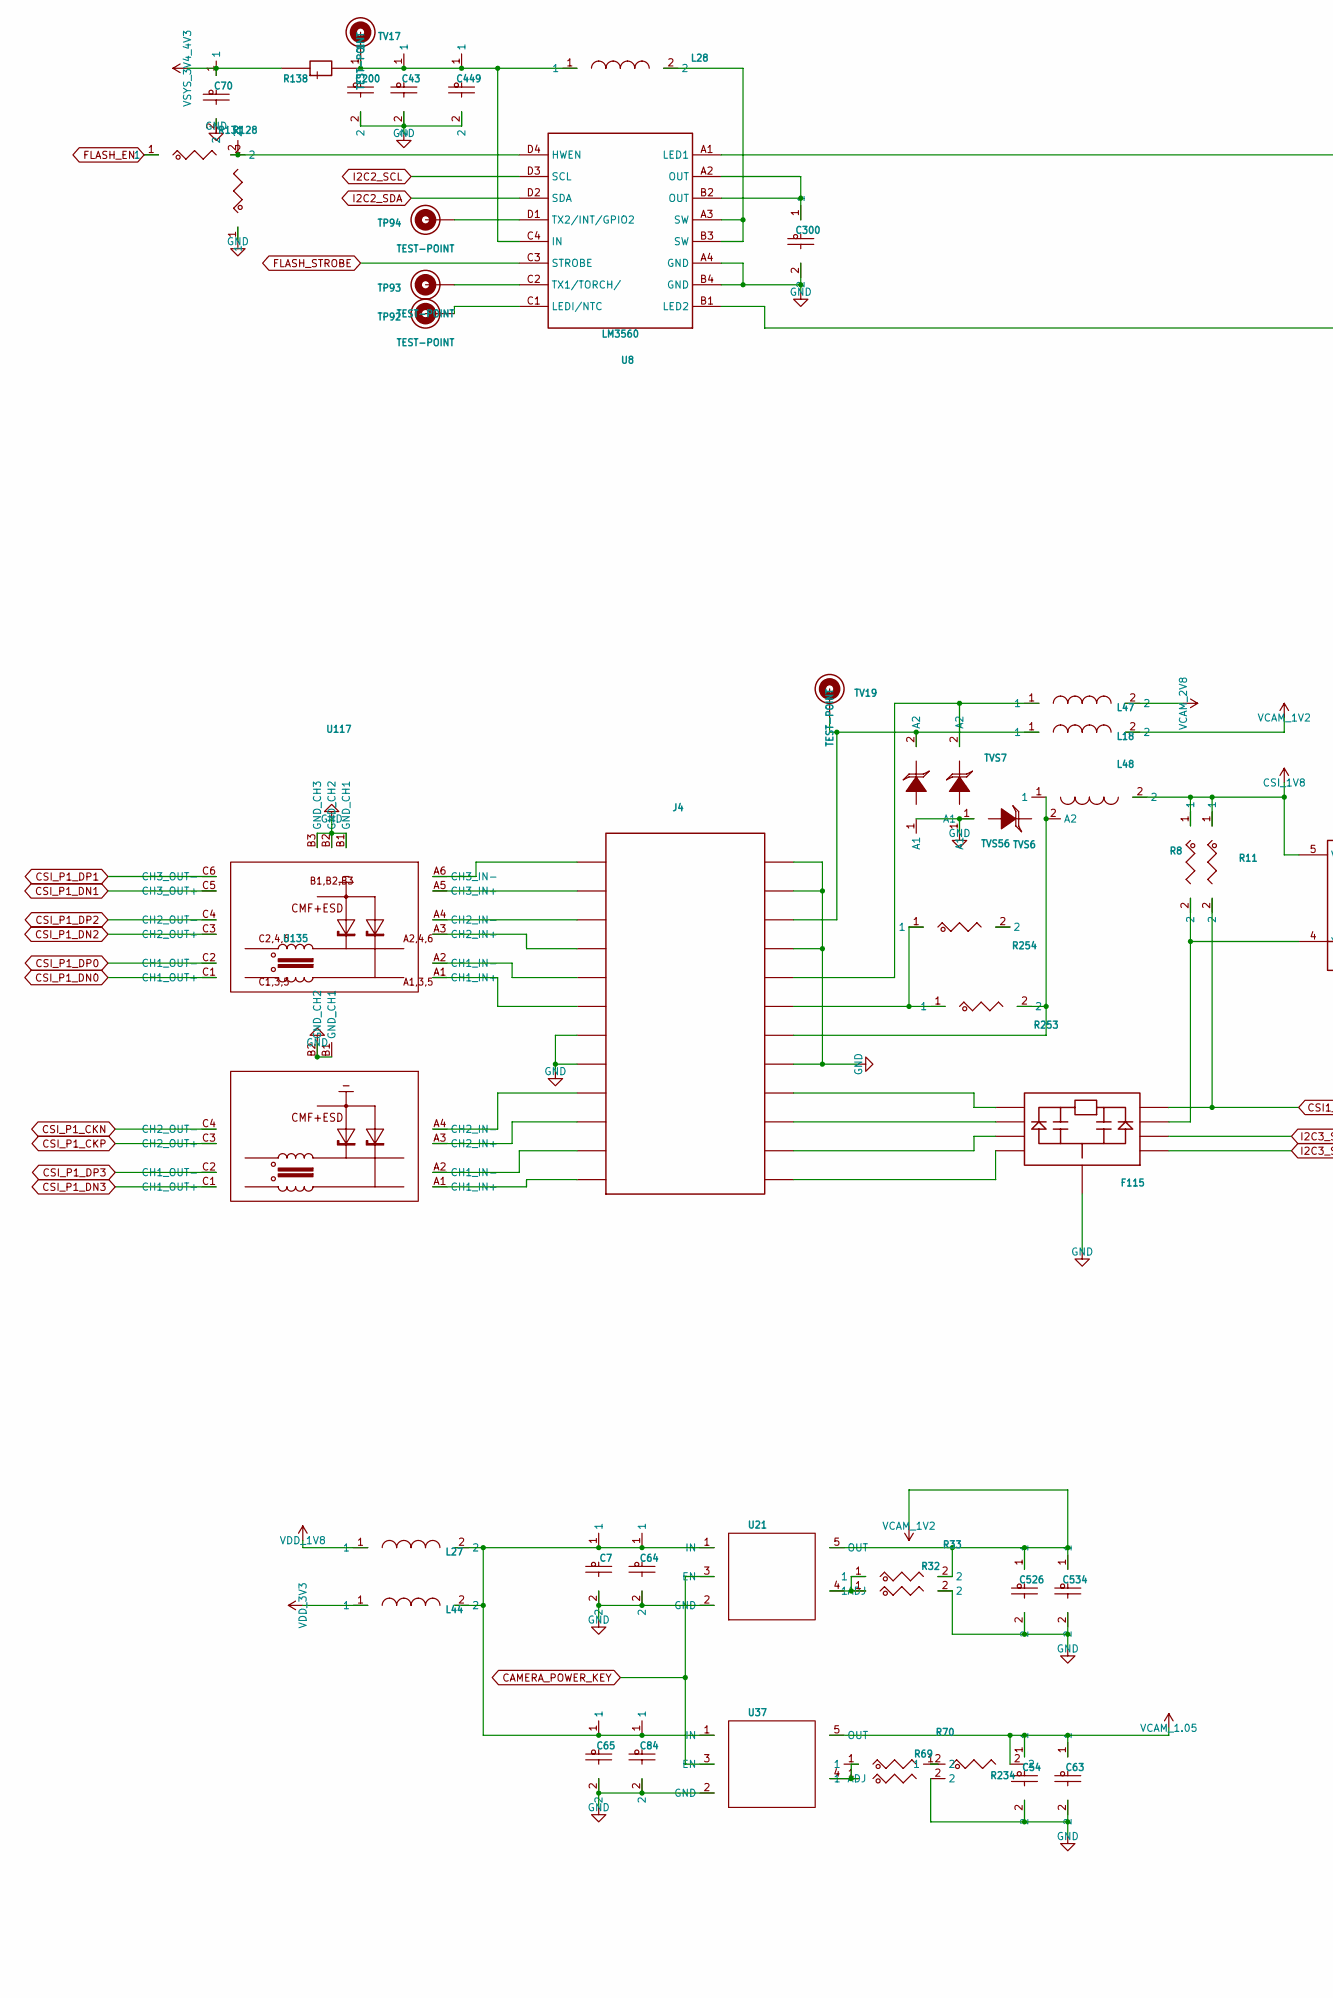
[picture p57: schematic librem5_mainboard_sheet17.kicad_sch, part in row 1, column 1]

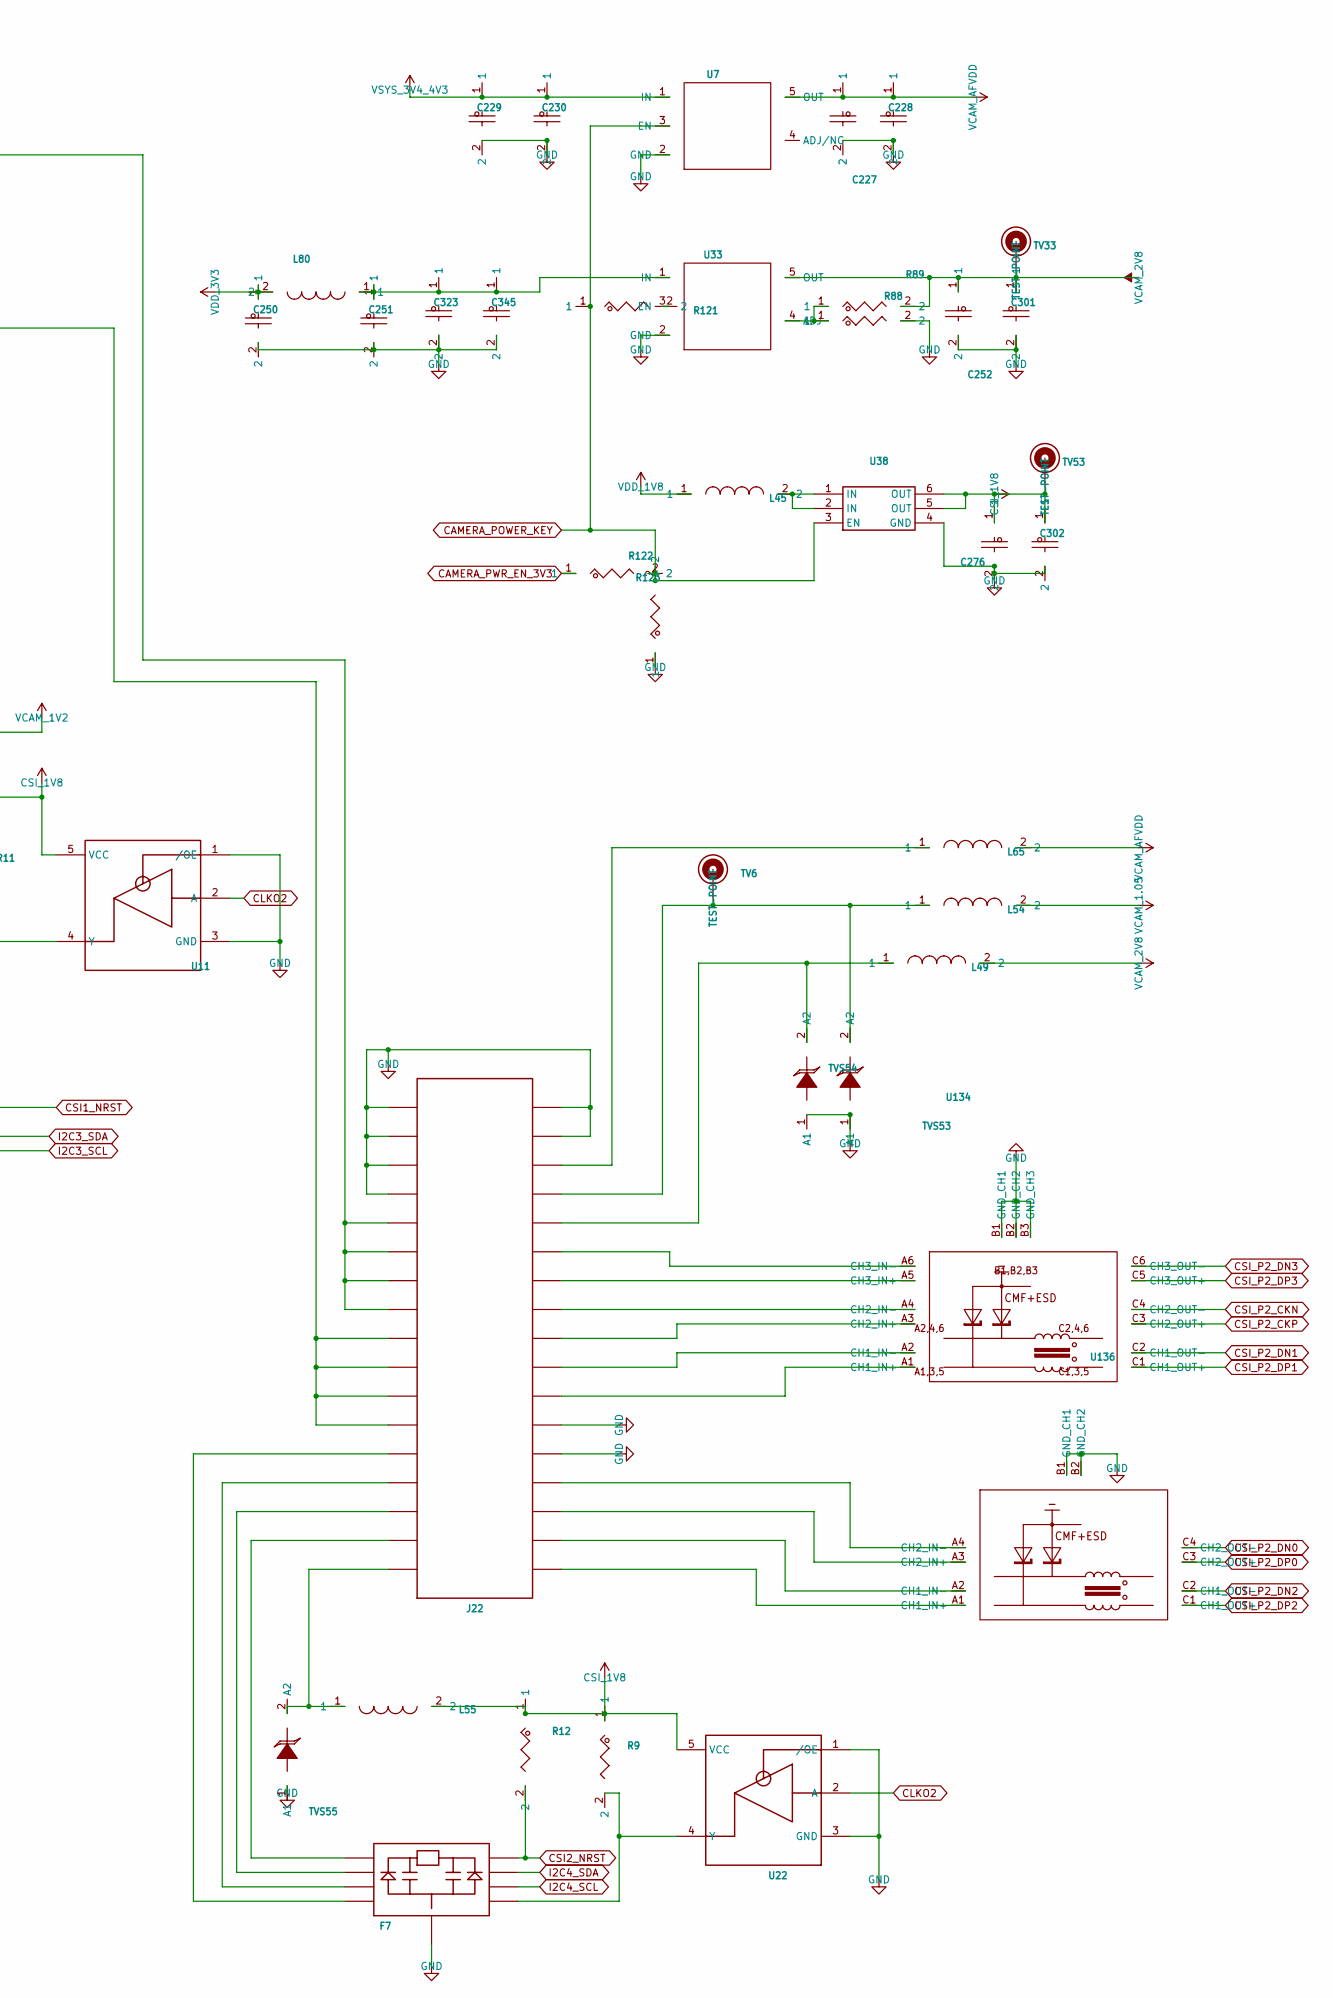
[picture p58: schematic librem5_mainboard_sheet17.kicad_sch, part in row 1, column 2]

Parts:
C7, C43, C54, C65, C300, C449, C526: C0603; VOLTAGE 6.3V
C63, C64, C84, C200, C228, C230, C301, C302, C323, C345, C534: C0201; VOLTAGE 6.3V
C70, C227, C229, C250, C251, C252, C276: C0402; VOLTAGE 6.3V
F7, F115: FILTER_ESD_BUS4
J4: OK-06F024-04
J22: CON-34; CON-OK-06M034-4-CZX
L18, L27, L44, L45, L47, L48, L49, L54, L55, L65, L80: BEAD-0402
L28: INDUCTOR
R8, R9, R11, R12, R32, R33, R69, R70, R88, R89, R121, R122, R123, R128, R131, R234, R253, R254: RES_2
R138: CURRENT_R
TP92, TP93, TP94: TEST-POINT
TV6, TV17, TV19, TV33, TV53: TEST-POINT
TVS6, TVS7, TVS53, TVS54, TVS55, TVS56: TVS_0402_882
U7: ME6211C__M5G
U8: LM3560
U11, U22: 74LVC1G125-SC70-5
U21, U33, U37: MIC5233_ADJ_SOT23_5P
U38: AP2281
U117, U134: PCMF3USB3S
U135, U136: PCMF2USB3S_10P

Connections:
CAMERA_POWER_KEY: R121.1, R122.2, R123.2, U7.3 (EN), U21.3 (EN), U37.3 (EN), U38.3 (EN)
CAMERA_PWR_EN_3V3: R122.1
CLKO2: U11.2 (A), U22.2 (A)
CSI1_NRST: F115.1, R11.2
CSI2_NRST: F7.8, R12.2
CSI_1V8: C276.1, C302.1, L48.2, L55.2, R8.1, R9.1, R11.1, R12.1, TV53.1, U11.5 (VCC), U22.5 (VCC), U38.5 (OUT), U38.6 (OUT)
CSI_P1_CKN: U135.C4 (CH2_OUT-)
CSI_P1_CKP: U135.C3 (CH2_OUT+)
CSI_P1_DN0: U117.C1 (CH1_OUT+)
CSI_P1_DN1: U117.C5 (CH3_OUT+)
CSI_P1_DN2: U117.C3 (CH2_OUT+)
CSI_P1_DN3: U135.C1 (CH1_OUT+)
CSI_P1_DP0: U117.C2 (CH1_OUT-)
CSI_P1_DP1: U117.C6 (CH3_OUT-)
CSI_P1_DP2: U117.C4 (CH2_OUT-)
CSI_P1_DP3: U135.C2 (CH1_OUT-)
CSI_P2_CKN: U134.C4 (CH2_OUT-)
CSI_P2_CKP: U134.C3 (CH2_OUT+)
CSI_P2_DN0: U136.C4 (CH2_OUT-)
CSI_P2_DN1: U134.C2 (CH1_OUT-)
CSI_P2_DN2: U136.C2 (CH1_OUT-)
CSI_P2_DN3: U134.C6 (CH3_OUT-)
CSI_P2_DP0: U136.C3 (CH2_OUT+)
CSI_P2_DP1: U134.C1 (CH1_OUT+)
CSI_P2_DP2: U136.C1 (CH1_OUT+)
CSI_P2_DP3: U134.C5 (CH3_OUT+)
FLASH_EN: R128.1
FLASH_STROBE: U8.C3 (STROBE)
GND: C7.2, C43.2, C54.2, C63.2, C64.2, C65.2, C70.2, C84.2, C200.2, C227.2, C228.2, C229.2, C230.2, C250.2, C251.2, C252.2, C276.2, C300.2, C301.2, C302.2, C323.2, C345.2, C449.2, C526.2, C534.2, F7.9, F115.9, J4.2, J4.4, J4.8, J4.13, J4.15, J4.16, J22.5, J22.6, J22.16, J22.17, J22.18, J22.19, J22.20, J22.21, R32.2, R69.2, R88.2, R123.1, R131.1, TVS6.1 (A1), TVS7.1 (A1), TVS53.1 (A1), TVS54.1 (A1), TVS55.1 (A1), TVS56.1 (A1), U7.2 (GND), U8.A4 (GND), U8.B4 (GND), U11.1 (/OE), U11.3 (GND), U21.2 (GND), U22.1 (/OE), U22.3 (GND), U33.2 (GND), U37.2 (GND), U38.4 (GND), U117.B1 (GND_CH1), U117.B2 (GND_CH2), U117.B3 (GND_CH3), U134.B1 (GND_CH1), U134.B2 (GND_CH2), U134.B3 (GND_CH3), U135.B1 (GND_CH1), U135.B2 (GND_CH2), U136.B1 (GND_CH1), U136.B2 (GND_CH2)
I2C2_SCL: U8.D3 (SCL)
I2C2_SDA: U8.D2 (SDA)
I2C3_SCL: F115.4
I2C3_SDA: F115.3
I2C4_SCL: F7.6
I2C4_SDA: F7.7
unnamed: C7.1, C64.1, C65.1, C84.1, L27.2, L44.2, U21.1 (IN), U37.1 (IN)
unnamed: C43.1, C200.1, C449.1, L28.1, R138.2, TV17.1, U8.C4 (IN)
unnamed: C251.1, C323.1, C345.1, L80.1, U33.1 (IN)
unnamed: C300.1, U8.A2 (OUT), U8.B2 (OUT)
unnamed: F7.1, J22.33
unnamed: F7.2, J22.32
unnamed: F7.3, J22.31
unnamed: F7.4, J22.30
unnamed: F7.5, R9.2, U22.4 (Y)
unnamed: F115.2, R8.2, U11.4 (Y)
unnamed: F115.5, J4.24
unnamed: F115.6, J4.22
unnamed: F115.7, J4.20
unnamed: F115.8, J4.18
unnamed: J4.1, U117.A6 (CH3_IN-)
unnamed: J4.3, U117.A5 (CH3_IN+)
unnamed: J4.5, U117.A4 (CH2_IN-)
unnamed: J4.6, L18.1, TV19.1, TVS7.2 (A2)
unnamed: J4.7, U117.A3 (CH2_IN+)
unnamed: J4.9, U117.A2 (CH1_IN-)
unnamed: J4.10, L47.1, TVS6.2 (A2)
unnamed: J4.11, U117.A1 (CH1_IN+)
unnamed: J4.12, R253.1, R254.1
unnamed: J4.14, L48.1, R253.2, TVS56.2 (A2)
unnamed: J4.17, U135.A4 (CH2_IN-)
unnamed: J4.19, U135.A3 (CH2_IN+)
unnamed: J4.21, U135.A2 (CH1_IN-)
unnamed: J4.23, U135.A1 (CH1_IN+)
unnamed: J22.1, U136.A1 (CH1_IN+)
unnamed: J22.2, U136.A2 (CH1_IN-)
unnamed: J22.3, U136.A3 (CH2_IN+)
unnamed: J22.4, U136.A4 (CH2_IN-)
unnamed: J22.7, U134.A1 (CH1_IN+)
unnamed: J22.8, U134.A2 (CH1_IN-)
unnamed: J22.9, U134.A3 (CH2_IN+)
unnamed: J22.10, U134.A4 (CH2_IN-)
unnamed: J22.11, U134.A5 (CH3_IN+)
unnamed: J22.12, U134.A6 (CH3_IN-)
unnamed: J22.13, L49.1, TVS54.2 (A2)
unnamed: J22.14, L54.1, TV6.1, TVS53.2 (A2)
unnamed: J22.15, L65.1
unnamed: J22.22, J22.23, J22.24, J22.25, U8.A1 (LED1)
unnamed: J22.26, J22.27, J22.28, J22.29, U8.B1 (LED2)
unnamed: J22.34, L55.1, TVS55.2 (A2)
unnamed: L28.2, U8.A3 (SW), U8.B3 (SW)
unnamed: L45.2, U38.1 (IN), U38.2 (IN)
unnamed: R32.1, R33.1, U21.4 (ADJ)
unnamed: R69.1, R70.1, U37.4 (ADJ)
unnamed: R88.1, R89.1, U33.4 (ADJ)
unnamed: R121.2, U33.3 (EN)
unnamed: R128.2, R131.2, U8.D4 (HWEN)
unnamed: R70.2, R234.1
unnamed: TP92.1, U8.C1 (LEDI/NTC)
unnamed: TP93.1, U8.C2 (TX1/TORCH/)
unnamed: TP94.1, U8.D1 (TX2/INT/GPIO2)
VCAM_1.05: C54.1, C63.1, L54.2, R234.2, U37.5 (OUT)
VCAM_1V2: C526.1, C534.1, L18.2, R33.2, U21.5 (OUT)
VCAM_2V8: C252.1, C301.1, L47.2, L49.2, R89.2, TV33.1, U33.5 (OUT)
VCAM_AFVDD: C227.1, C228.1, L65.2, U7.5 (OUT)
VDD_1V8: L27.1, L45.1
VDD_3V3: C250.1, L44.1, L80.2
VSYS_3V4_4V3: C70.1, C229.1, C230.1, R138.1, U7.1 (IN)
