gralco/l5-schematic/CAD/PADS/librem5_mainboard/librem5_mainboard_kicad_conversion/librem5_mainboard_sheet18.kicad_sch

## KiCad design CAD/PADS/librem5_mainboard/librem5_mainboard_kicad_conversion/librem5_mainboard_sheet18.kicad_sch (2026-05-21)

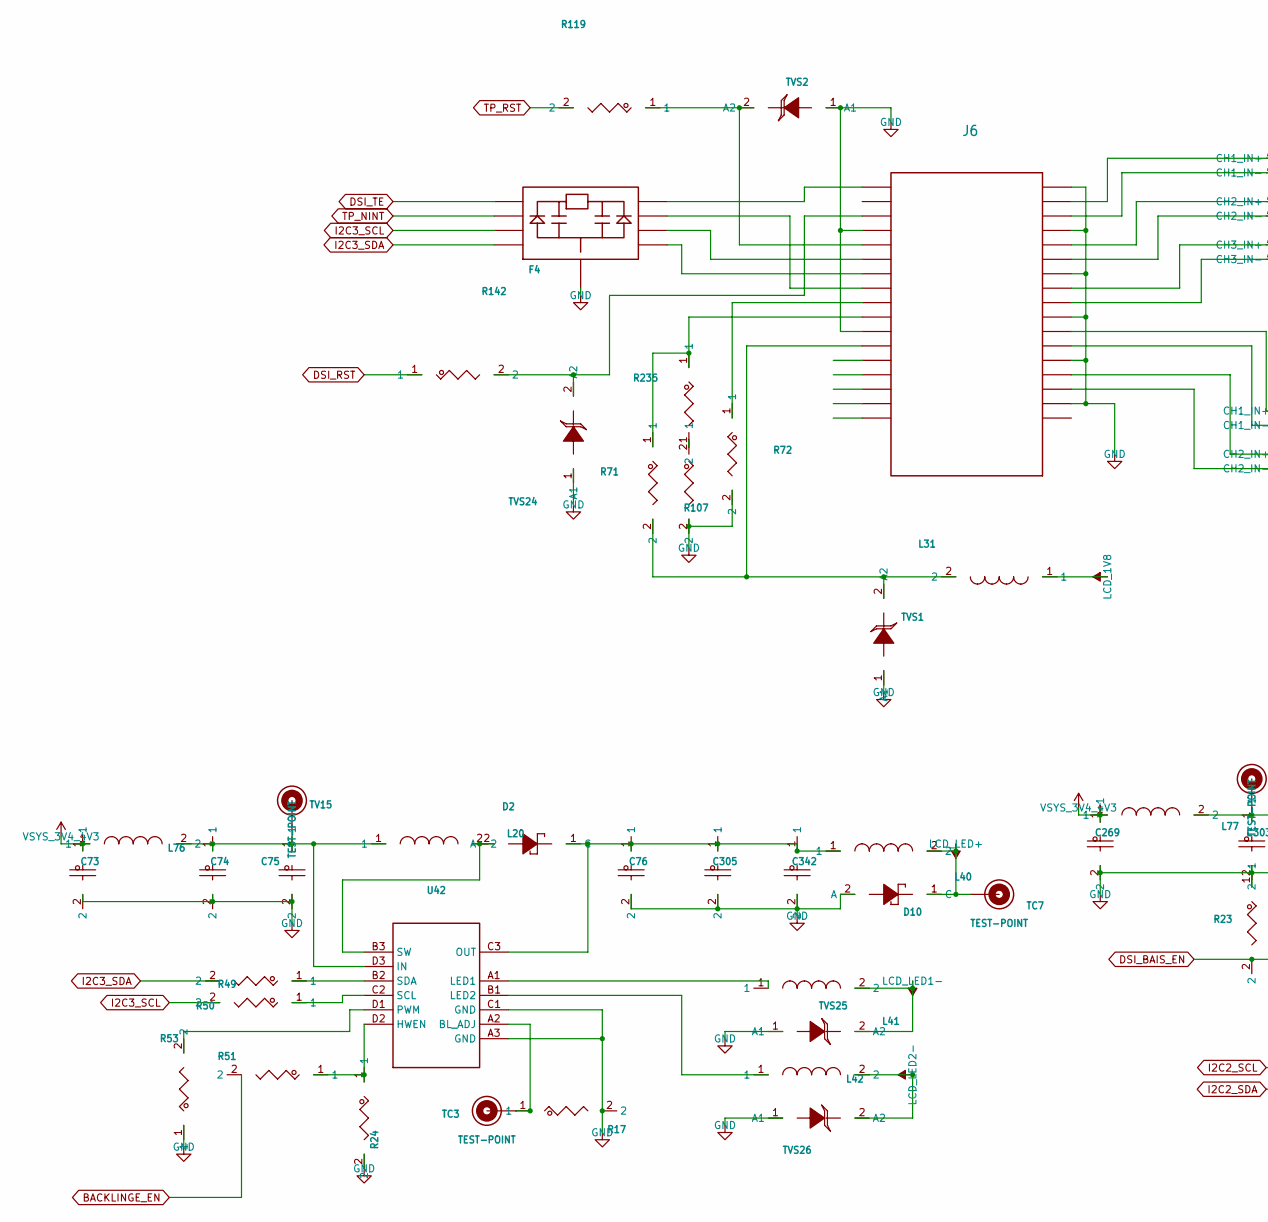
[picture p59: schematic librem5_mainboard_sheet18.kicad_sch, part in row 1, column 1]

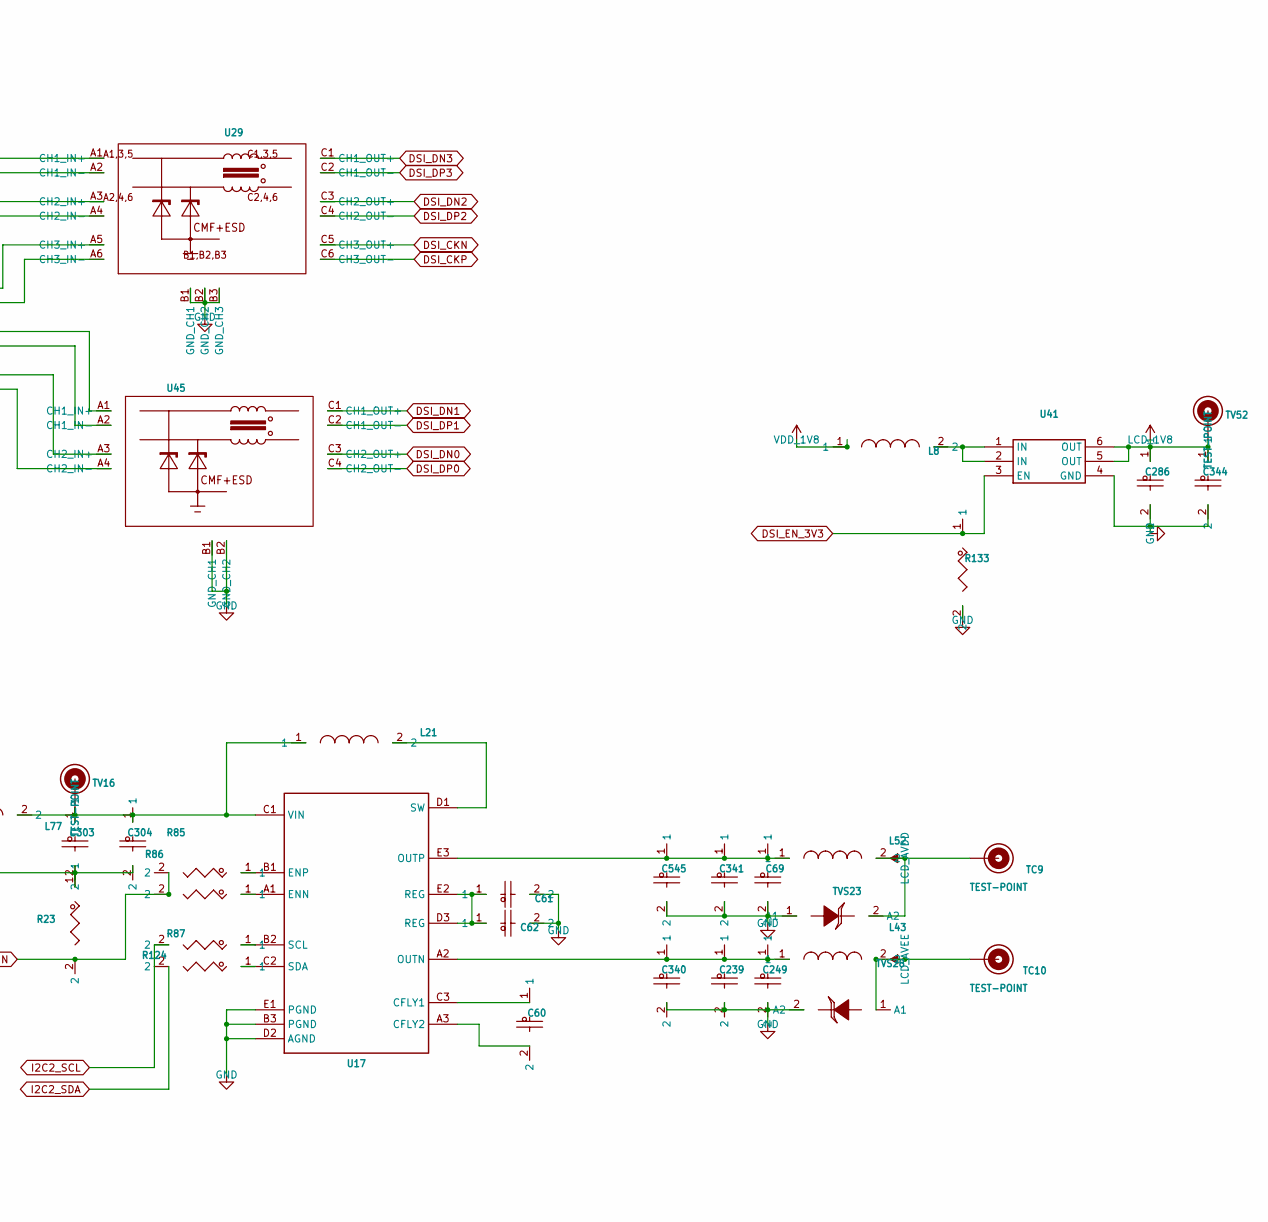
[picture p60: schematic librem5_mainboard_sheet18.kicad_sch, part in row 1, column 2]

Parts:
C60, C61, C62, C69, C239, C249, C341: C0402; VOLTAGE 35V
C73, C74, C269, C286, C303: C0402; VOLTAGE 6.3V
C75, C304, C344: C0201; VOLTAGE 6.3V
C76, C305: C0603; VOLTAGE 35V
C340, C342, C545: C0201; VOLTAGE 35V
D2: ZLLS400
D10: PTVS24VS1UR
F4: FILTER_ESD_BUS4
J6: OK-06F034-04
L8, L31, L40, L41, L42, L76, L77: BEAD-0402
L20, L21: INDUCTOR
L43, L52: BEAD-0201
R17, R23, R24, R49, R50, R51, R53, R71, R72, R85, R86, R87, R107, R119, R124, R133, R142, R235: RES_2
TC3, TC7, TC9, TC10: TEST-POINT
TV15, TV16, TV52: TEST-POINT
TVS1, TVS2, TVS23, TVS24, TVS25, TVS26, TVS28: TVS_0402_882
U17: TPS65132
U29: PCMF3USB3S
U41: AP2281
U42: LM36922-1
U45: PCMF2USB3S_10P

Connections:
BACKLINGE_EN: R51.2
DSI_BAIS_EN: R23.2, R85.2, R86.2
DSI_CKN: U29.C5 (CH3_OUT+)
DSI_CKP: U29.C6 (CH3_OUT-)
DSI_DN0: U45.C3 (CH2_OUT+)
DSI_DN1: U45.C1 (CH1_OUT+)
DSI_DN2: U29.C3 (CH2_OUT+)
DSI_DN3: U29.C1 (CH1_OUT+)
DSI_DP0: U45.C4 (CH2_OUT-)
DSI_DP1: U45.C2 (CH1_OUT-)
DSI_DP2: U29.C4 (CH2_OUT-)
DSI_DP3: U29.C2 (CH1_OUT-)
DSI_EN_3V3: R133.1, U41.3 (EN)
DSI_RST: R142.1
DSI_TE: F4.1
GND: C61.2, C62.2, C69.2, C73.2, C74.2, C75.2, C76.2, C239.2, C249.2, C269.2, C286.2, C303.2, C304.2, C305.2, C340.2, C341.2, C342.2, C344.2, C545.2, D10.2 (A), F4.9, J6.1, J6.4, J6.7, J6.10, J6.13, J6.16, J6.24, J6.31, R17.2, R23.1, R24.2, R53.1, R72.2, R107.2, R133.2, TVS1.1 (A1), TVS2.1 (A1), TVS23.1 (A1), TVS24.1 (A1), TVS25.1 (A1), TVS26.1 (A1), TVS28.2 (A2), U17.B3 (PGND), U17.D2 (AGND), U17.E1 (PGND), U29.B1 (GND_CH1), U29.B2 (GND_CH2), U29.B3 (GND_CH3), U41.4 (GND), U42.A3 (GND), U42.C1 (GND), U45.B1 (GND_CH1), U45.B2 (GND_CH2)
I2C2_SCL: R87.2
I2C2_SDA: R124.2
I2C3_SCL: F4.3, R50.2
I2C3_SDA: F4.4, R49.2
LCD_1V8: C286.1, C344.1, L31.1, TV52.1, U41.5 (OUT), U41.6 (OUT)
LCD_AVDD: L52.2, TC9.1, TVS23.2 (A2)
LCD_AVEE: L43.2, TC10.1, TVS28.1 (A1)
LCD_LED1-: L41.2, TVS25.2 (A2)
LCD_LED2-: L42.2, TVS26.2 (A2)
LCD_LED+: D10.1 (C), L40.2, TC7.1
unnamed: C60.1, U17.C3 (CFLY1)
unnamed: C60.2, U17.A3 (CFLY2)
unnamed: C61.1, C62.1, U17.D3 (REG), U17.E2 (REG)
unnamed: C74.1, C75.1, L20.1, L76.2, TV15.1, U42.D3 (IN)
unnamed: C239.1, C249.1, C340.1, L43.1, U17.A2 (OUTN)
unnamed: C303.1, C304.1, L21.1, L77.2, TV16.1, U17.C1 (VIN)
unnamed: C76.1, C305.1, C342.1, D2.1 (C), L40.1, U42.C3 (OUT)
unnamed: C69.1, C341.1, C545.1, L52.1, U17.E3 (OUTP)
unnamed: D2.2 (A), L20.2, U42.B3 (SW)
unnamed: F4.5, J6.28
unnamed: F4.6, J6.29
unnamed: F4.7, J6.27
unnamed: F4.8, J6.34
unnamed: J6.2, U29.A1 (CH1_IN+)
unnamed: J6.3, U29.A2 (CH1_IN-)
unnamed: J6.5, U29.A3 (CH2_IN+)
unnamed: J6.6, U29.A4 (CH2_IN-)
unnamed: J6.8, U29.A5 (CH3_IN+)
unnamed: J6.9, U29.A6 (CH3_IN-)
unnamed: J6.11, U45.A1 (CH1_IN+)
unnamed: J6.12, U45.A2 (CH1_IN-)
unnamed: J6.14, U45.A3 (CH2_IN+)
unnamed: J6.15, U45.A4 (CH2_IN-)
unnamed: J6.23, L31.2, R71.2, TVS1.2 (A2)
unnamed: J6.25, R71.1, R235.1
unnamed: J6.26, R72.1
unnamed: J6.30, R119.1, TVS2.2 (A2)
unnamed: J6.32, R142.2, TVS24.2 (A2)
unnamed: L8.2, U41.1 (IN), U41.2 (IN)
unnamed: L21.2, U17.D1 (SW)
unnamed: L41.1, U42.A1 (LED1)
unnamed: L42.1, U42.B1 (LED2)
unnamed: R17.1, TC3.1, U42.A2 (BL_ADJ)
unnamed: R24.1, R51.1, U42.D2 (HWEN)
unnamed: R49.1, U42.B2 (SDA)
unnamed: R50.1, U42.C2 (SCL)
unnamed: R53.2, U42.D1 (PWM)
unnamed: R85.1, U17.B1 (ENP)
unnamed: R86.1, U17.A1 (ENN)
unnamed: R87.1, U17.B2 (SCL)
unnamed: R107.1, R235.2
unnamed: R124.1, U17.C2 (SDA)
TP_NINT: F4.2
TP_RST: R119.2
VDD_1V8: L8.1
VSYS_3V4_4V3: C73.1, C269.1, L76.1, L77.1
