gralco/l5-schematic/CAD/PADS/librem5_mainboard/librem5_mainboard_kicad_conversion/librem5_mainboard_sheet19.kicad_sch

## KiCad design CAD/PADS/librem5_mainboard/librem5_mainboard_kicad_conversion/librem5_mainboard_sheet19.kicad_sch (2026-05-21)

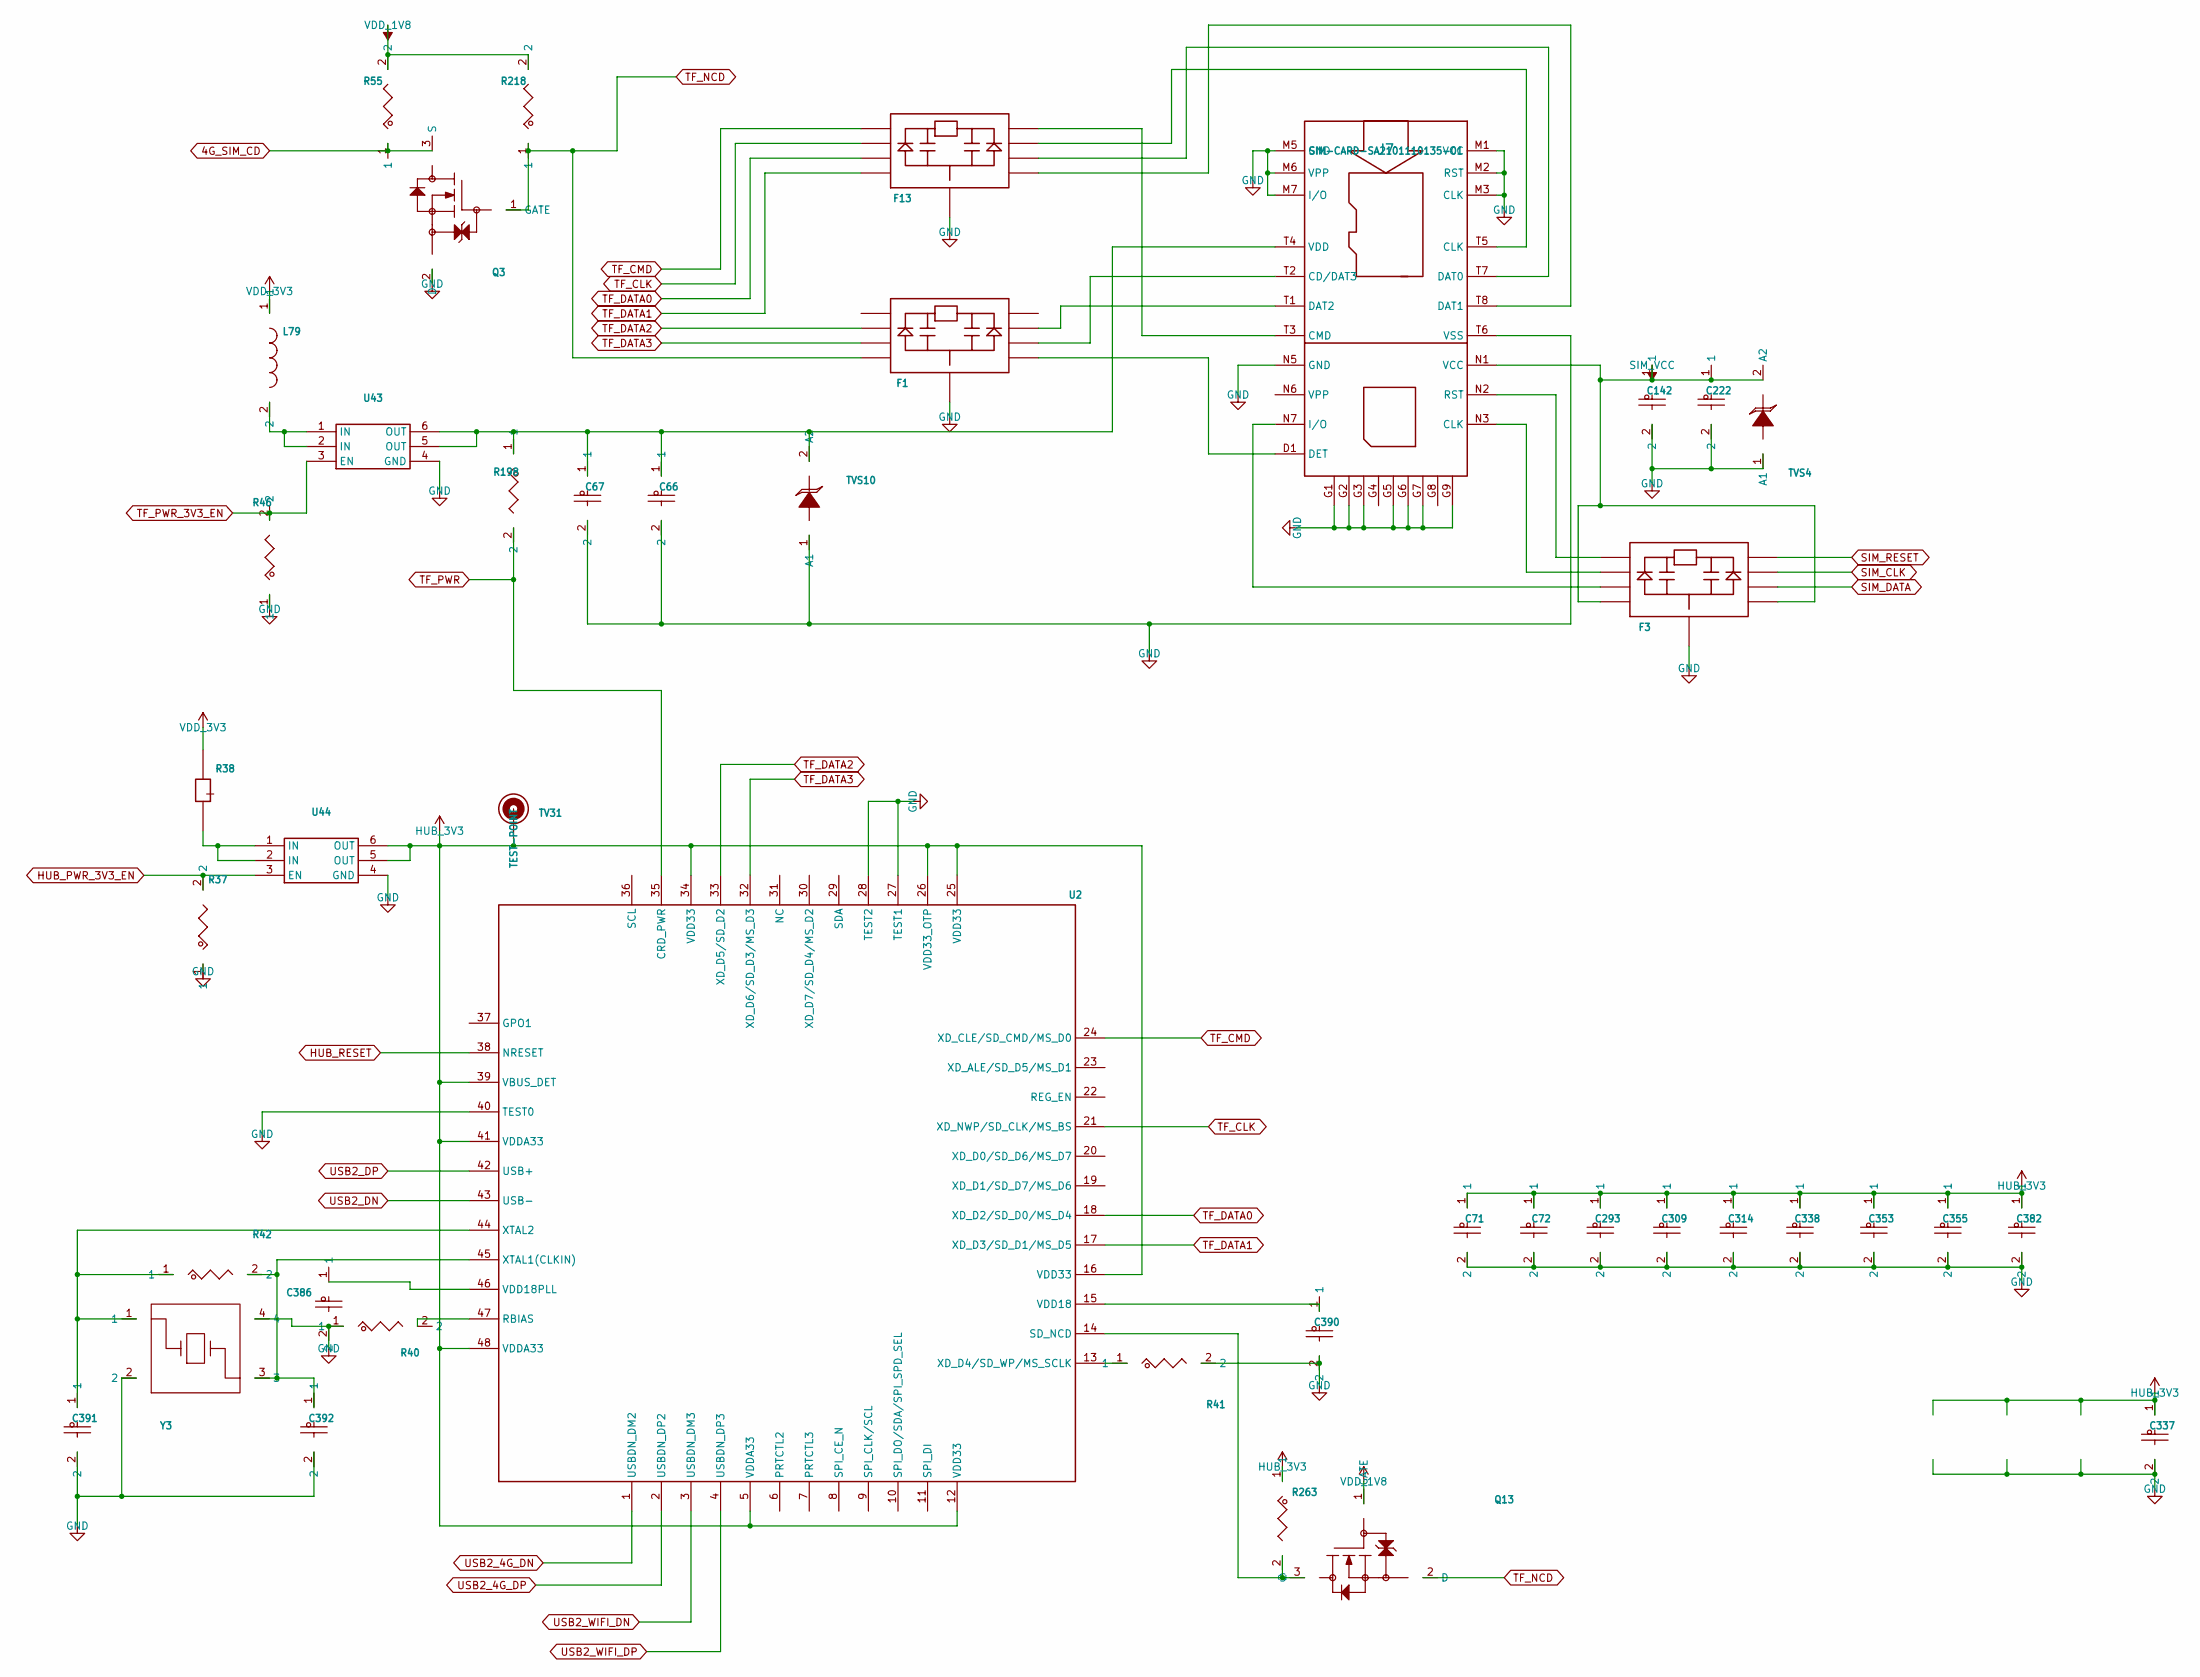
[picture p61: schematic librem5_mainboard_sheet19.kicad_sch]

Parts:
C66, C71, C72, C142, C293, C309, C314, C338, C353, C355, C386, C390: C0201; VOLTAGE 6.3V
C67: C0603; VOLTAGE 6.3V
C222, C337, C382: C0402; VOLTAGE 6.3V
C391, C392: C0201; VOLTAGE 25V
F1, F3, F13: FILTER_ESD_BUS4
J7: SIM-CARD-SA2101110135-01
L79: BEAD-0402
Q3, Q13: 2SK3018
R37, R40, R41, R42, R46, R55, R198, R218: RES_2
R38: CURRENT_R
R263: R_0201
TV31: TEST-POINT
TVS4, TVS10: TVS_0402_882
U2: USB2642
U43, U44: AP2281
Y3: XTAL_13Y

Connections:
4G_SIM_CD: Q3.3 (S), R55.1
GND: C66.2, C67.2, C71.2, C72.2, C142.2, C222.2, C293.2, C309.2, C314.2, C337.2, C338.2, C353.2, C355.2, C382.2, C386.2, C390.2, C391.2, C392.2, F1.9, F3.9, F13.9, J7.G1, J7.G2, J7.G3, J7.G5, J7.G6, J7.G7, J7.G9, J7.M1 (VCC), J7.M2 (RST), J7.M3 (CLK), J7.M5 (GND), J7.M6 (VPP), J7.M7 (I/O), J7.N5 (GND), J7.T6 (VSS), Q3.2 (D), R37.1, R40.1, R41.2, R46.1, TVS4.1 (A1), TVS10.1 (A1), U2.27 (TEST1), U2.28 (TEST2), U2.40 (TEST0), U43.4 (GND), U44.4 (GND), Y3.2, Y3.4
HUB_3V3: C71.1, C72.1, C293.1, C309.1, C314.1, C337.1, C338.1, C353.1, C355.1, C382.1, R263.1, TV31.1, U2.5 (VDDA33), U2.12 (VDD33), U2.16 (VDD33), U2.25 (VDD33), U2.26 (VDD33_OTP), U2.34 (VDD33), U2.39 (VBUS_DET), U2.41 (VDDA33), U2.48 (VDDA33), U44.5 (OUT), U44.6 (OUT)
HUB_PWR_3V3_EN: R37.2, U44.3 (EN)
HUB_RESET: U2.38 (NRESET)
unnamed: C66.1, C67.1, J7.T4 (VDD), R198.1, TVS10.2 (A2), U43.5 (OUT), U43.6 (OUT)
unnamed: C386.1, U2.46 (VDD18PLL)
unnamed: C390.1, U2.15 (VDD18)
unnamed: C391.1, R42.1, U2.44 (XTAL2), Y3.1
unnamed: C392.1, R42.2, U2.45 (XTAL1(CLKIN)), Y3.3
unnamed: F1.5, J7.D1 (DET)
unnamed: F1.6, J7.T2 (CD/DAT3)
unnamed: F1.7, J7.T1 (DAT2)
unnamed: F3.1, J7.N2 (RST)
unnamed: F3.2, J7.N3 (CLK)
unnamed: F3.3, J7.N7 (I/O)
unnamed: F13.5, J7.T8 (DAT1)
unnamed: F13.6, J7.T7 (DAT0)
unnamed: F13.7, J7.T5 (CLK)
unnamed: F13.8, J7.T3 (CMD)
unnamed: L79.2, U43.1 (IN), U43.2 (IN)
unnamed: Q13.3 (S), R263.2, U2.14 (SD_NCD)
unnamed: R38.1, U44.1 (IN), U44.2 (IN)
unnamed: R40.2, U2.47 (RBIAS)
unnamed: R41.1, U2.13 (XD_D4/SD_WP/MS_SCLK)
SIM_CLK: F3.7
SIM_DATA: F3.6
SIM_RESET: F3.8
SIM_VCC: C142.1, C222.1, F3.4, F3.5, J7.N1 (VCC), TVS4.2 (A2)
TF_CLK: F13.2, U2.21 (XD_NWP/SD_CLK/MS_BS)
TF_CMD: F13.1, U2.24 (XD_CLE/SD_CMD/MS_D0)
TF_DATA0: F13.3, U2.18 (XD_D2/SD_D0/MS_D4)
TF_DATA1: F13.4, U2.17 (XD_D3/SD_D1/MS_D5)
TF_DATA2: F1.2, U2.33 (XD_D5/SD_D2)
TF_DATA3: F1.3, U2.32 (XD_D6/SD_D3/MS_D3)
TF_NCD: F1.4, Q3.1 (GATE), Q13.2 (D), R218.1
TF_PWR: R198.2, U2.35 (CRD_PWR)
TF_PWR_3V3_EN: R46.2, U43.3 (EN)
USB2_4G_DN: U2.1 (USBDN_DM2)
USB2_4G_DP: U2.2 (USBDN_DP2)
USB2_DN: U2.43 (USB-)
USB2_DP: U2.42 (USB+)
USB2_WIFI_DN: U2.3 (USBDN_DM3)
USB2_WIFI_DP: U2.4 (USBDN_DP3)
VDD_1V8: Q13.1 (GATE), R55.2, R218.2
VDD_3V3: L79.1, R38.2
