gralco/l5-schematic/CAD/PADS/librem5_mainboard/librem5_mainboard_kicad_conversion/librem5_mainboard_sheet20.kicad_sch

## KiCad design CAD/PADS/librem5_mainboard/librem5_mainboard_kicad_conversion/librem5_mainboard_sheet20.kicad_sch (2026-05-21)

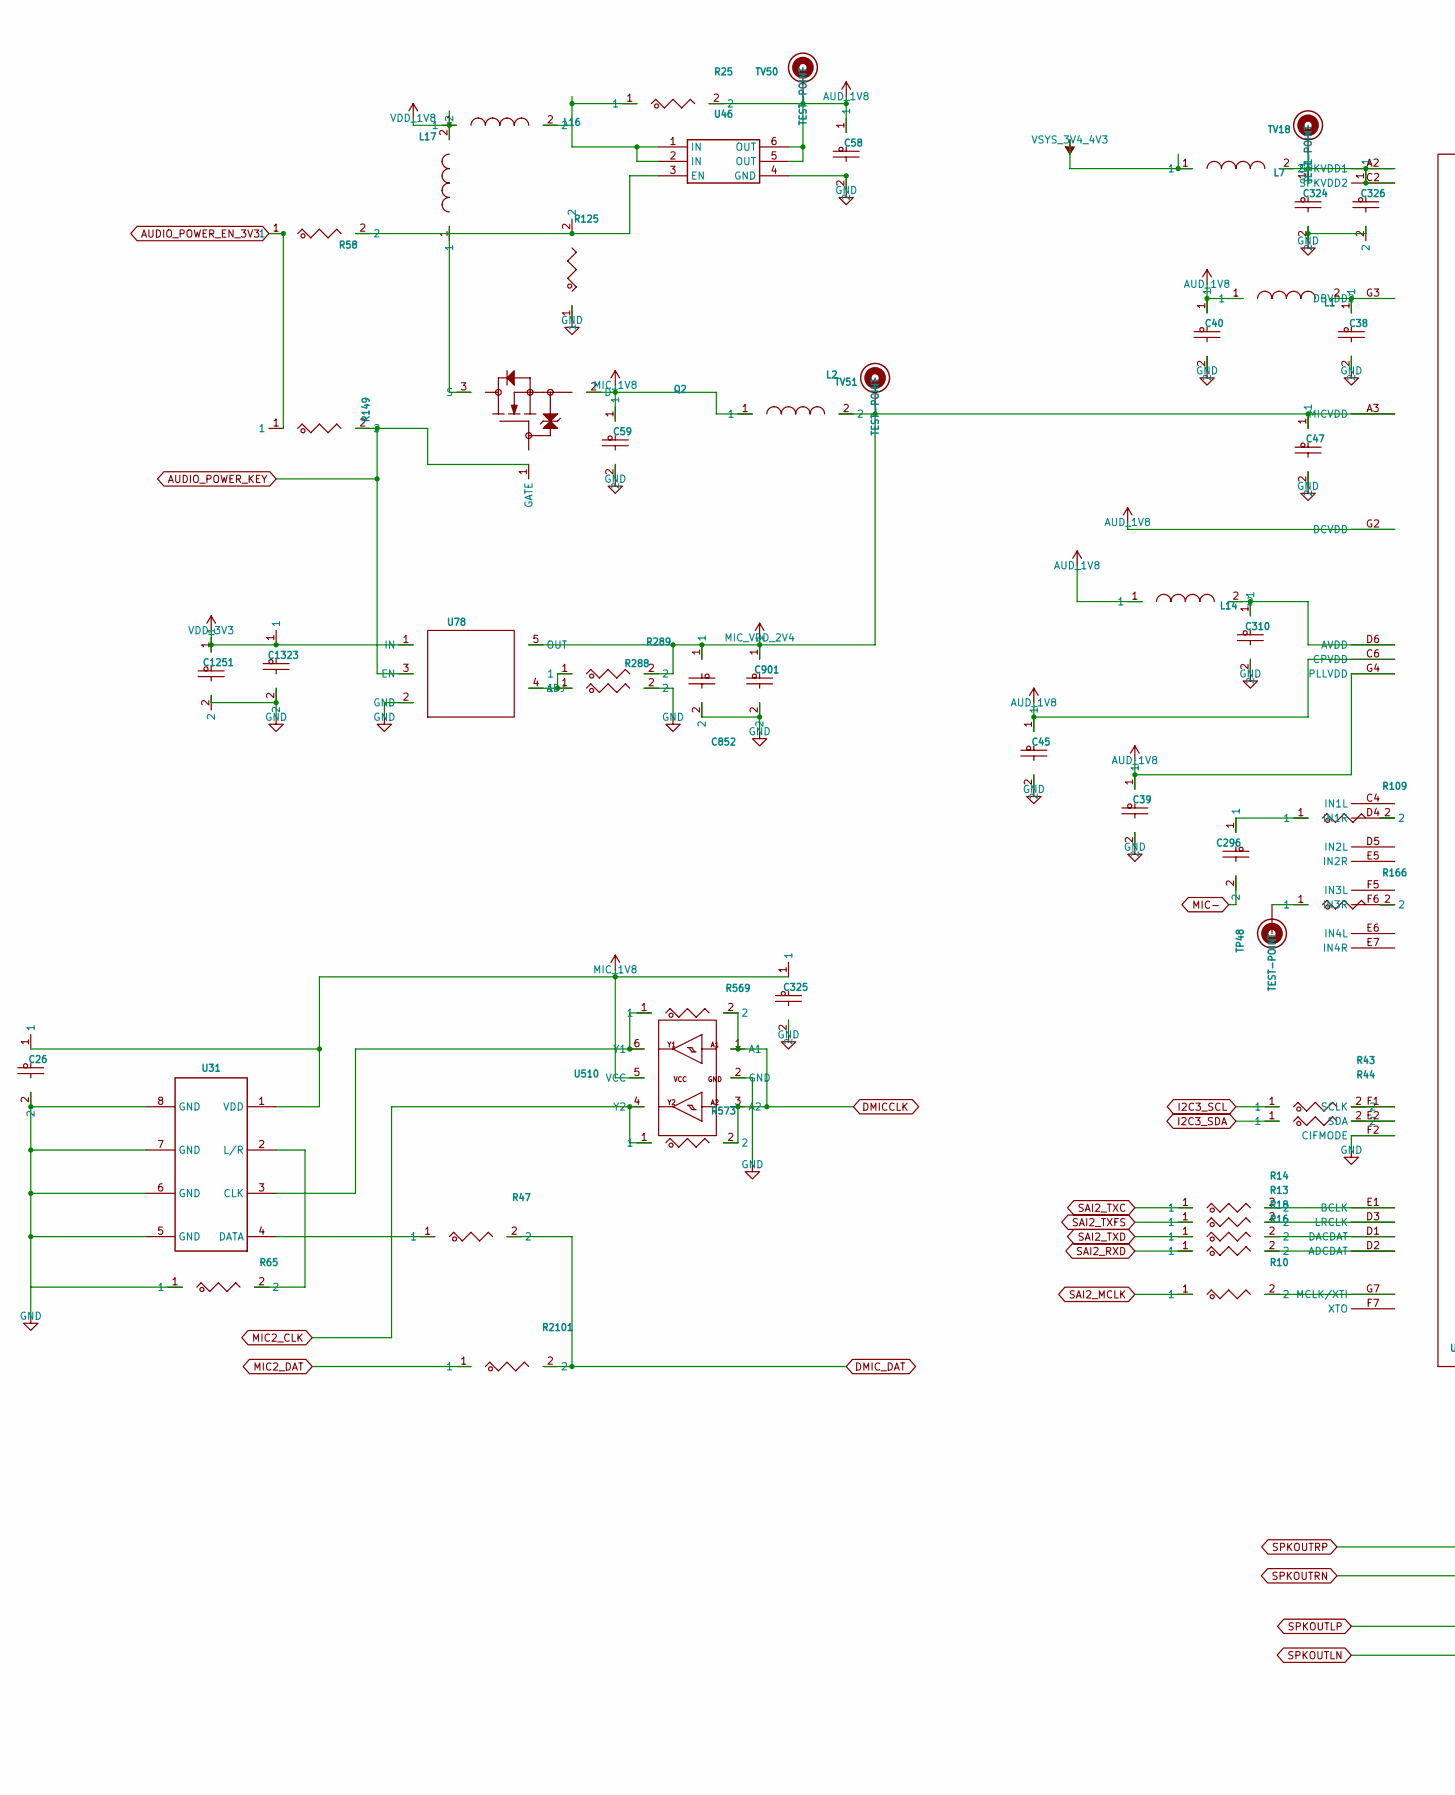
[picture p62: schematic librem5_mainboard_sheet20.kicad_sch, part in row 1, column 1]

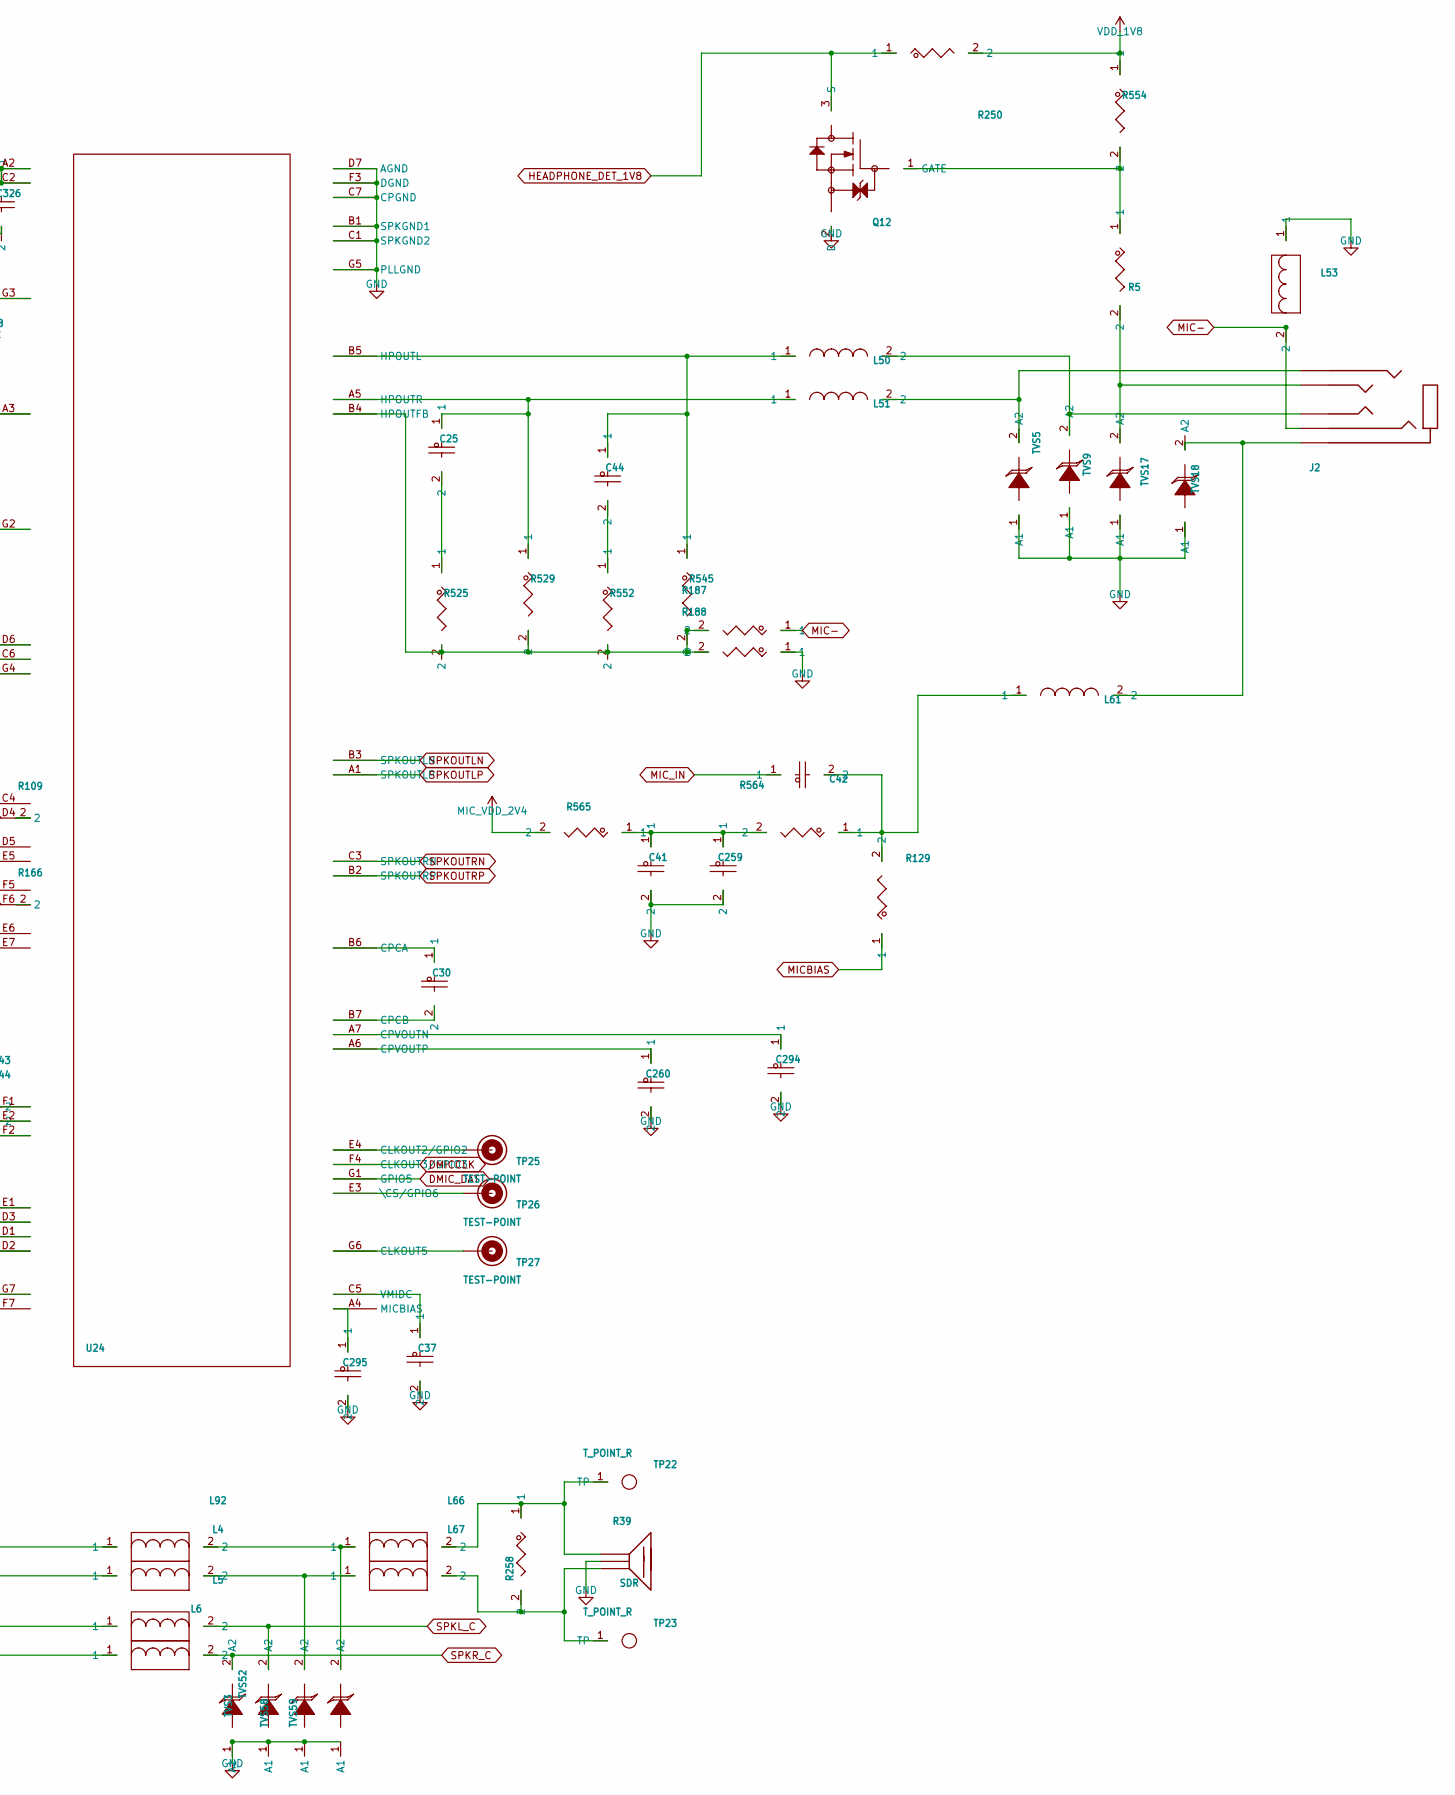
[picture p63: schematic librem5_mainboard_sheet20.kicad_sch, part in row 1, column 2]

Parts:
C25, C26, C38, C40, C42, C44, C58, C295, C296, C325, C326, C901, C1323: C0201; VOLTAGE 6.3V
C30, C37, C39, C45, C47, C59, C260, C294, C310, C852, C1251: C0402; VOLTAGE 6.3V
C41: C0603
C259: C0201
C324: C0603; VOLTAGE 6.3V
J2: JACK-JA-36A1-111
L1, L2, L7, L14, L16, L17, L50, L51, L61: BEAD-0402
L4, L5, L6, L53, L66, L67, L92: BEAD0603
Q2, Q12: 2SK3018
R5, R10, R13, R14, R16, R18, R25, R43, R44, R47, R58, R65, R109, R125, R129, R149, R166, R187, R188, R258, R288, R289, R525, R529, R545, R552, R554, R564, R565, R569, R573, R2101: RES_2
R39: SDR
R250: R_0201
TP22, TP23: T_POINT_R
TP25, TP26, TP27, TP48: TEST-POINT
TV18, TV50, TV51: TEST-POINT
TVS3, TVS5, TVS9, TVS17, TVS18, TVS52, TVS58, TVS59: TVS_0402_882
U24: WM8962
U31: 3SM222FMT1KA
U46: AP2281
U78: MIC5233_ADJ_SOT23_5P
U510: NC7WZ17

Connections:
AUDIO_POWER_EN_3V3: R58.1, R149.1
AUDIO_POWER_KEY: Q2.1 (GATE), R149.2, U78.3 (EN)
AUD_1V8: C39.1, C40.1, C45.1, C58.1, L1.1, L14.1, R25.2, TV50.1, U24.C6 (CPVDD), U24.G2 (DCVDD), U24.G4 (PLLVDD), U46.5 (OUT), U46.6 (OUT)
DMICCLK: R569.2, R573.2, U24.F4 (CLKOUT3/GPIO3), U510.1 (A1), U510.3 (A2)
DMIC_DAT: R47.2, R2101.2, U24.G1 (GPIO5)
GND: C26.2, C37.2, C38.2, C39.2, C40.2, C41.2, C45.2, C47.2, C58.2, C59.2, C259.2, C260.2, C294.2, C295.2, C310.2, C324.2, C325.2, C326.2, C852.2, C901.2, C1251.2, C1323.2, L53.1, Q12.2 (D), R39.3, R125.1, R188.1, R288.2, TVS3.1 (A1), TVS5.1 (A1), TVS9.1 (A1), TVS17.1 (A1), TVS18.1 (A1), TVS52.1 (A1), TVS58.1 (A1), TVS59.1 (A1), U24.B1 (SPKGND1), U24.C1 (SPKGND2), U24.C7 (CPGND), U24.D7 (AGND), U24.F2 (CIFMODE), U24.F3 (DGND), U24.G5 (PLLGND), U31.5 (GND), U31.6 (GND), U31.7 (GND), U31.8 (GND), U46.4 (GND), U78.2 (GND), U510.2 (GND)
HEADPHONE_DET_1V8: Q12.3 (S), R250.1
I2C3_SCL: R43.1
I2C3_SDA: R44.1
MIC2_CLK: R573.1, U510.4 (Y2)
MIC2_DAT: R2101.1
MIC-: C296.2, J2.2, L53.2, R187.1
MICBIAS: R129.1
MIC_1V8: C26.1, C59.1, C325.1, L2.1, Q2.2 (D), U31.1 (VDD), U510.5 (VCC)
MIC_IN: C42.1
MIC_VDD_2V4: C47.1, C852.1, C901.1, L2.2, R289.2, R565.2, TV51.1, U24.A3 (MICVDD), U78.5 (OUT)
unnamed: C25.1, L51.1, R529.1, U24.A5 (HPOUTR)
unnamed: C25.2, R525.1
unnamed: C30.1, U24.B6 (CPCA)
unnamed: C30.2, U24.B7 (CPCB)
unnamed: C37.1, U24.C5 (VMIDC)
unnamed: C38.1, L1.2, U24.G3 (DBVDD)
unnamed: C42.2, L61.1, R129.2, R564.1
unnamed: C44.1, L50.1, R545.1, U24.B5 (HPOUTL)
unnamed: C44.2, R552.1
unnamed: C41.1, C259.1, R564.2, R565.1
unnamed: C260.1, U24.A6 (CPVOUTP)
unnamed: C294.1, U24.A7 (CPVOUTN)
unnamed: C295.1, U24.A4 (MICBIAS)
unnamed: C296.1, R109.1
unnamed: C310.1, L14.2, U24.D6 (AVDD)
unnamed: C324.1, C326.1, L7.2, TV18.1, U24.A2 (SPKVDD1), U24.C2 (SPKVDD2)
unnamed: J2.1, L61.2, TVS18.2 (A2)
unnamed: J2.3, L51.2, TVS5.2 (A2)
unnamed: J2.4, R5.2, TVS17.2 (A2)
unnamed: J2.5, L50.2, TVS9.2 (A2)
unnamed: L4.2, L67.1, TVS58.2 (A2)
unnamed: L17.1, Q2.3 (S)
unnamed: L66.1, L92.2, TVS59.2 (A2)
unnamed: L66.2, R39.1, R258.1, TP22.1
unnamed: L67.2, R39.2, R258.2, TP23.1
unnamed: Q12.1 (GATE), R5.1, R554.2
unnamed: R10.2, U24.G7 (MCLK/XTI)
unnamed: R13.2, U24.D3 (LRCLK)
unnamed: R14.2, U24.E1 (BCLK)
unnamed: R16.2, U24.D2 (ADCDAT)
unnamed: R18.2, U24.D1 (DACDAT)
unnamed: R25.1, U46.1 (IN), U46.2 (IN)
unnamed: R43.2, U24.F1 (SCLK)
unnamed: R44.2, U24.E2 (SDA)
unnamed: R47.1, U31.4 (DATA)
unnamed: R65.2, U31.2 (L/R)
unnamed: R109.2, U24.D4 (IN1R)
unnamed: R58.2, R125.2, U46.3 (EN)
unnamed: R166.1, TP48.1
unnamed: R166.2, U24.F6 (IN3R)
unnamed: R187.2, R188.2, R525.2, R529.2, R545.2, R552.2, U24.B4 (HPOUTFB)
unnamed: R288.1, R289.1, U78.4 (ADJ)
unnamed: R569.1, U31.3 (CLK), U510.6 (Y1)
unnamed: TP25.1, U24.E4 (CLKOUT2/GPIO2)
unnamed: TP26.1, U24.E3 (\CS/GPIO6)
unnamed: TP27.1, U24.G6 (CLKOUT5)
SAI2_MCLK: R10.1
SAI2_RXD: R16.1
SAI2_TXC: R14.1
SAI2_TXD: R18.1
SAI2_TXFS: R13.1
SPKL_C: L5.2, TVS3.2 (A2)
SPKOUTLN: L6.1, U24.B3 (SPKOUTLN)
SPKOUTLP: L5.1, U24.A1 (SPKOUTLP)
SPKOUTRN: L4.1, U24.C3 (SPKOUTRN)
SPKOUTRP: L92.1, U24.B2 (SPKOUTRP)
SPKR_C: L6.2, TVS52.2 (A2)
VDD_1V8: L16.1, L17.2, R250.2, R554.1
VDD_3V3: C1251.1, C1323.1, U78.1 (IN)
VSYS_3V4_4V3: L7.1
