gralco/l5-schematic/CAD/PADS/librem5_mainboard/librem5_mainboard_kicad_conversion/librem5_mainboard_sheet21.kicad_sch

## KiCad design CAD/PADS/librem5_mainboard/librem5_mainboard_kicad_conversion/librem5_mainboard_sheet21.kicad_sch (2026-05-21)

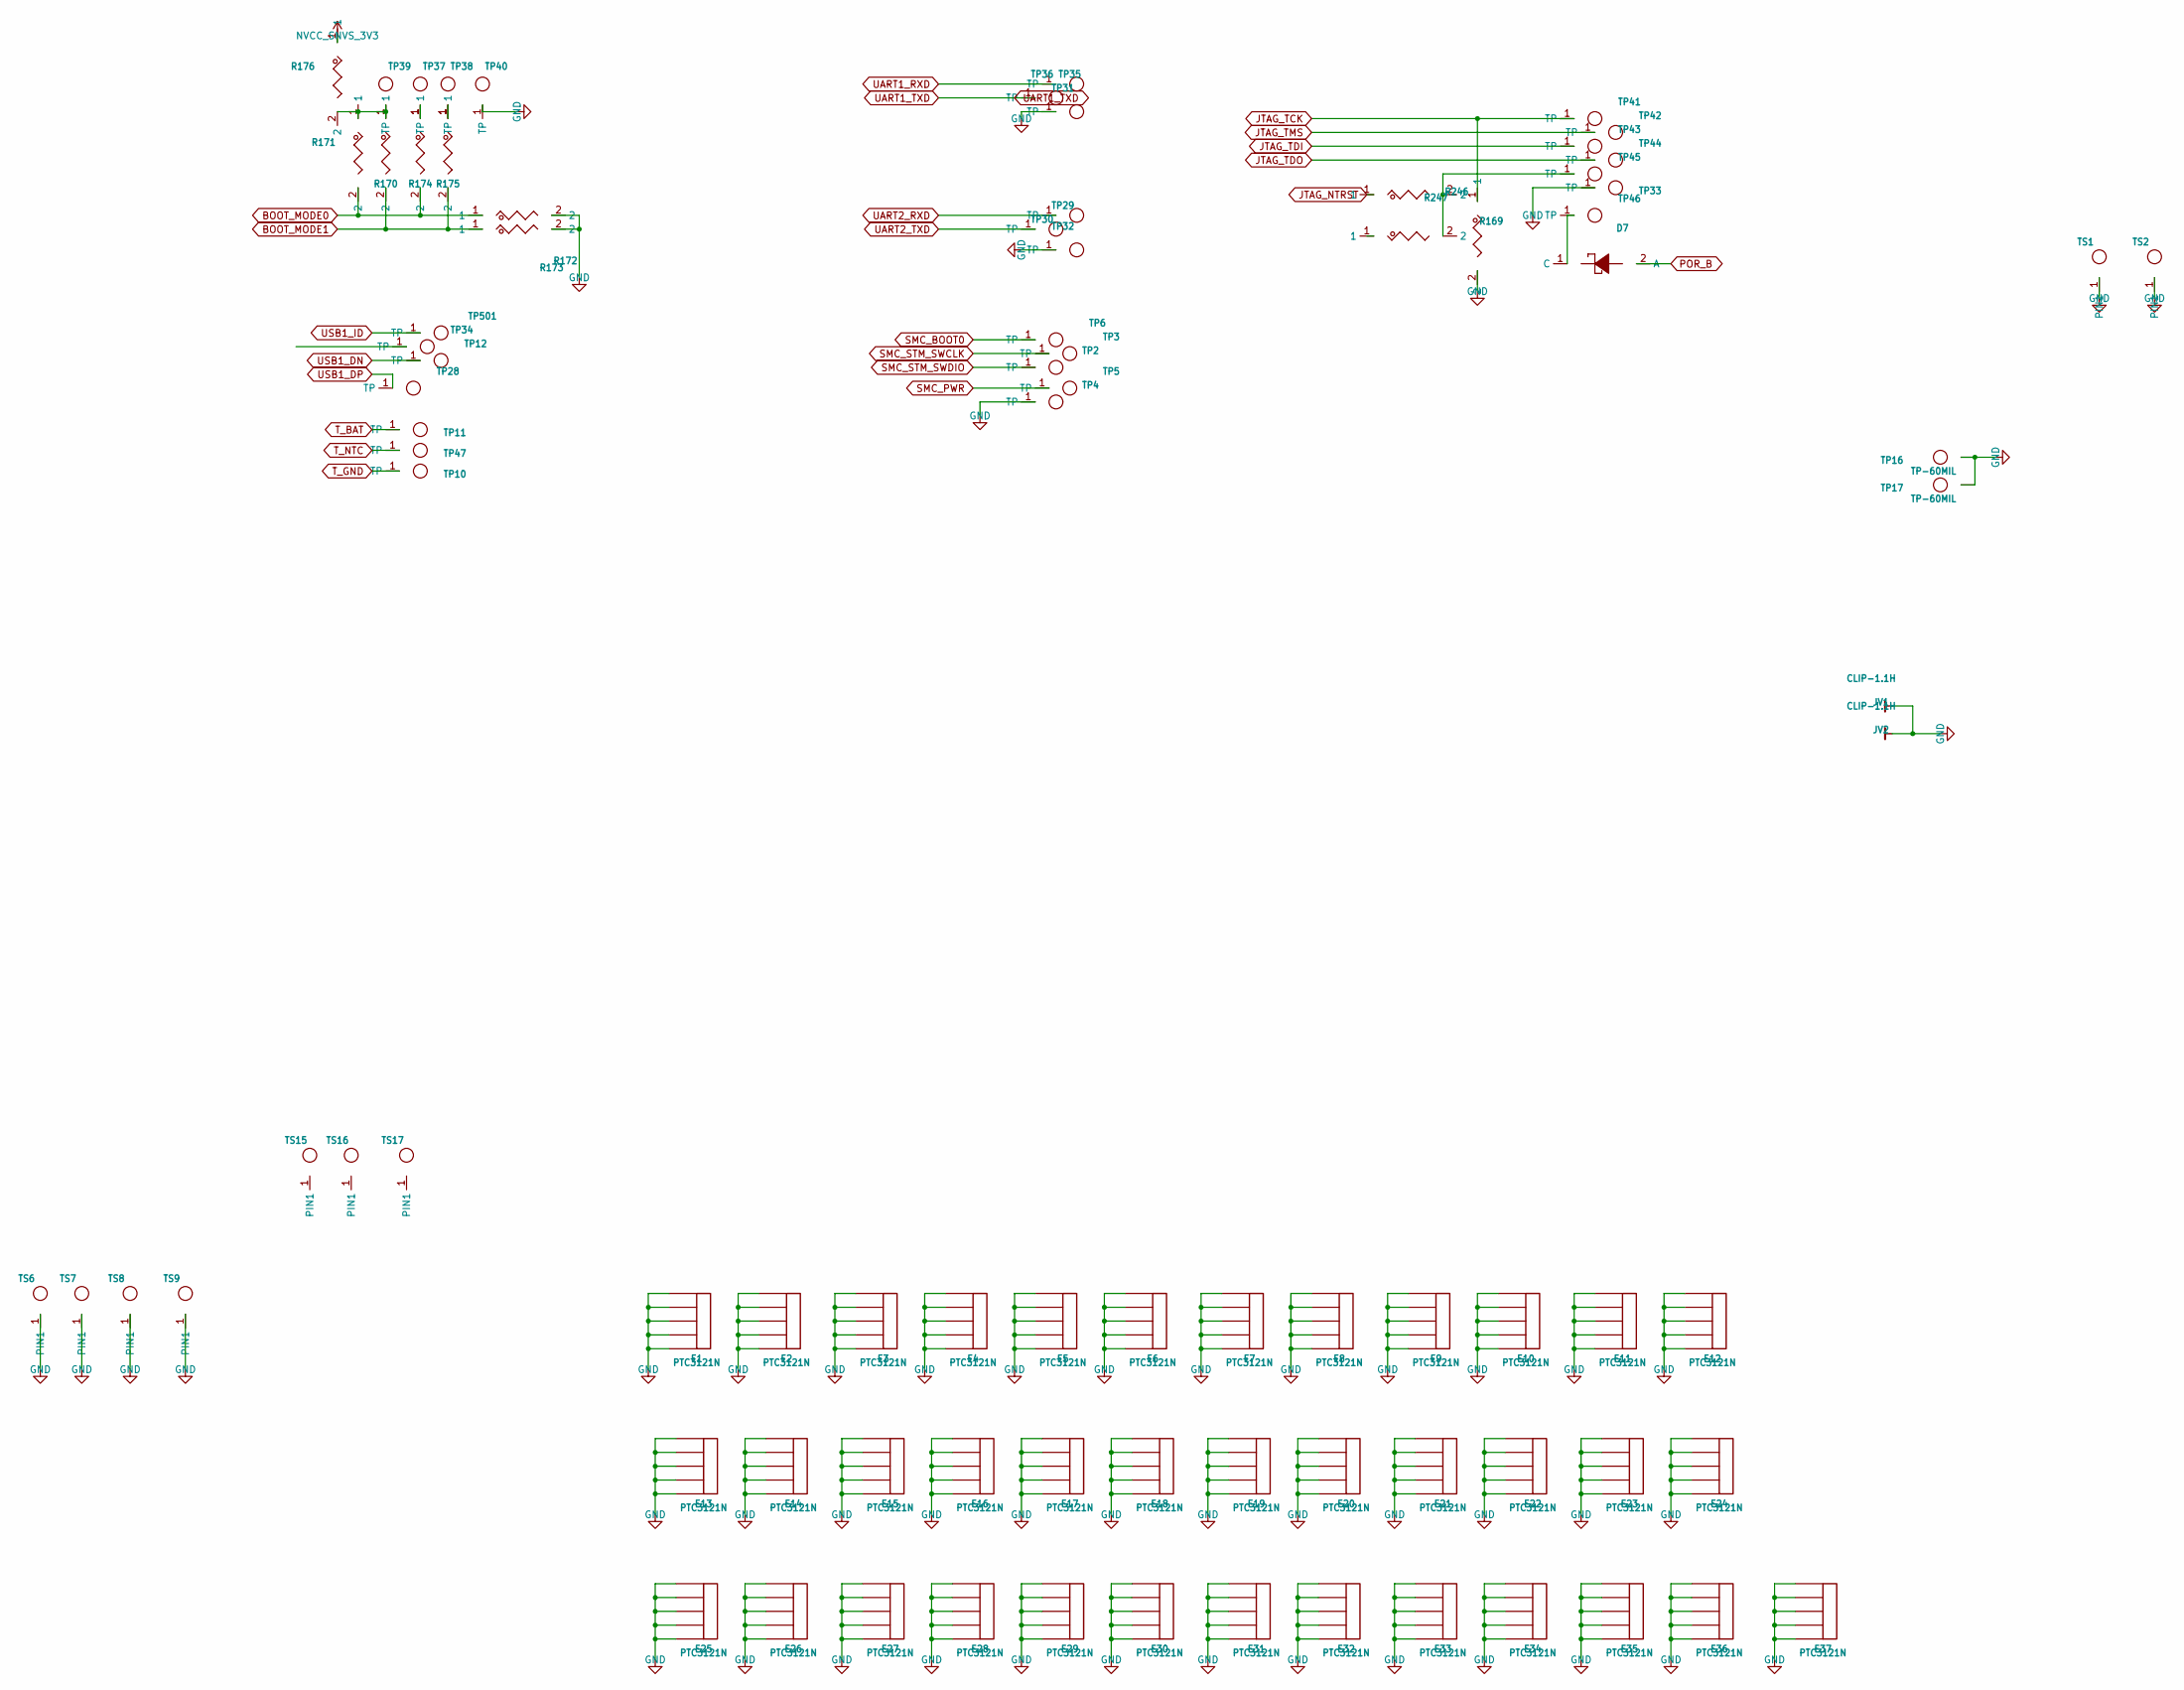
[picture p64: schematic librem5_mainboard_sheet21.kicad_sch]

Parts:
D7: DIODE_SCHTKY_0
E1, E2, E3, E4, E5, E6, E7, E8, E9, E10, E11, E12, E13, E14, E15, E16, E17, E18, E19, E20, E21, E22, E23, E24, E25, E26, E27, E28, E29, E30, E31, E32, E33, E34, E35, E36, E37: PTC3121N
JV1, JV2: CLIP-1.1H
R169, R170, R171, R172, R173, R174, R175, R176, R246, R247: RES_2
TP2, TP3, TP4, TP5, TP6, TP10, TP11, TP12, TP28, TP29, TP30, TP31, TP32, TP33, TP34, TP35, TP36, TP37, TP38, TP39, TP40, TP41, TP42, TP43, TP44, TP45, TP46, TP47, TP501: T_POINT_R
TP16, TP17: TP-60MIL
TS1, TS2: SC-M2
TS6, TS7, TS8, TS9, TS15, TS16, TS17: SC-M1.4

Connections:
BOOT_MODE0: R171.2, R172.1, R174.2
BOOT_MODE1: R170.2, R173.1, R175.2
GND: E1.1, E1.2, E1.3, E1.4, E1.5, E2.1, E2.2, E2.3, E2.4, E2.5, E3.1, E3.2, E3.3, E3.4, E3.5, E4.1, E4.2, E4.3, E4.4, E4.5, E5.1, E5.2, E5.3, E5.4, E5.5, E6.1, E6.2, E6.3, E6.4, E6.5, E7.1, E7.2, E7.3, E7.4, E7.5, E8.1, E8.2, E8.3, E8.4, E8.5, E9.1, E9.2, E9.3, E9.4, E9.5, E10.1, E10.2, E10.3, E10.4, E10.5, E11.1, E11.2, E11.3, E11.4, E11.5, E12.1, E12.2, E12.3, E12.4, E12.5, E13.1, E13.2, E13.3, E13.4, E13.5, E14.1, E14.2, E14.3, E14.4, E14.5, E15.1, E15.2, E15.3, E15.4, E15.5, E16.1, E16.2, E16.3, E16.4, E16.5, E17.1, E17.2, E17.3, E17.4, E17.5, E18.1, E18.2, E18.3, E18.4, E18.5, E19.1, E19.2, E19.3, E19.4, E19.5, E20.1, E20.2, E20.3, E20.4, E20.5, E21.1, E21.2, E21.3, E21.4, E21.5, E22.1, E22.2, E22.3, E22.4, E22.5, E23.1, E23.2, E23.3, E23.4, E23.5, E24.1, E24.2, E24.3, E24.4, E24.5, E25.1, E25.2, E25.3, E25.4, E25.5, E26.1, E26.2, E26.3, E26.4, E26.5, E27.1, E27.2, E27.3, E27.4, E27.5, E28.1, E28.2, E28.3, E28.4, E28.5, E29.1, E29.2, E29.3, E29.4, E29.5, E30.1, E30.2, E30.3, E30.4, E30.5, E31.1, E31.2, E31.3, E31.4, E31.5, E32.1, E32.2, E32.3, E32.4, E32.5, E33.1, E33.2, E33.3, E33.4, E33.5, E34.1, E34.2, E34.3, E34.4, E34.5, E35.1, E35.2, E35.3, E35.4, E35.5, E36.1, E36.2, E36.3, E36.4, E36.5, E37.1, E37.2, E37.3, E37.4, E37.5, JV1.1, JV2.1, R169.2, R172.2, R173.2, TP4.1, TP16.1, TP17.1, TP31.1, TP32.1, TP33.1, TP40.1, TS1.1, TS2.1, TS6.1, TS7.1, TS8.1, TS9.1
JTAG_NTRST: R246.1
JTAG_TCK: R169.1, TP41.1
JTAG_TDI: TP43.1
JTAG_TDO: TP44.1
JTAG_TMS: TP42.1
NVCC_SNVS_3V3: R176.1
unnamed: D7.1 (C), TP46.1
unnamed: R170.1, R171.1, R176.2, TP39.1
unnamed: R174.1, TP37.1
unnamed: R175.1, TP38.1
unnamed: R246.2, R247.2, TP45.1
POR_B: D7.2 (A)
SMC_BOOT0: TP6.1
SMC_PWR: TP5.1
SMC_STM_SWCLK: TP3.1
SMC_STM_SWDIO: TP2.1
T_BAT: TP11.1
T_GND: TP10.1
T_NTC: TP47.1
UART1_RXD: TP35.1
UART1_TXD: TP36.1
UART2_RXD: TP29.1
UART2_TXD: TP30.1
USB1_DN: TP12.1
USB1_DP: TP28.1
USB1_ID: TP501.1
